huapohen/imagine/docs/business/README.md

# 商业材料索引

所有材料日期2026-09-06。业务、成本与销量是计划/估算；没有已确认融资、订单或生产结果。

- [详细可执行商业计划](business-plan.md)
- [演示结构与口径](outline.md)
- [3分钟/8分钟逐字稿](pitch-scripts.md)
- [投资人60问](investor-qa-60.md)
- [半年生态、8种硬件排序与10个月战略检查](ecosystem-and-exit.md)
- [定价/BOM/财务说明](financial-model.md)
- [SKU输入](financial-inputs-skus.csv)、[公共参数](financial-assumptions.csv)、[情景销量输入](financial-scenarios.csv)
- [单台经济输出](financial-sku-economics.csv)、[月度利润现金输出](financial-monthly.csv)、[情景汇总](financial-summary.csv)
- [重算脚本](calculate_financials.py)：在项目根执行 `python3 docs/business/calculate_financials.py`
- [研究事实与来源](../research/findings.md)
- [工厂RFQ模板](../manufacturing-commercial/rfq-template.md)、[验收与排期](../manufacturing-commercial/acceptance-and-schedule.md)、[BOM CSV](../manufacturing-commercial/bom-cost-estimate.csv)、[采购排期CSV](../manufacturing-commercial/procurement-schedule.csv)

最关键未验证项：299元真实购买选择、鼠标对同一软件的增量价值、D7/D30留存、3家工厂同口径报价、小批成本与良率、USB/供电/人体工学、适用合规、本地agent安装权限、企业聚合重识别风险。官方竞品标价与网页性能主张不能代替这些证据。
