huapohen/imagine/docs/business/business-plan.md

# Imagine 可执行商业计划

2026-09-06｜内部决策版｜创始前验证阶段。成本、销量、留存、收入及估值均无实绩；本文件给出可证伪假设和执行门槛。研究事实见 [findings.md](../research/findings.md)，模型见 [financial-model.md](financial-model.md)。

## 1. 决定先做什么

首款是透明有线鼠标，加一个独立的ESP32-S3灯光/触摸/小屏模块，连接电脑本地agent。鼠标运动、按键和滚轮沿用成熟OEM标准USB HID，AI故障时仍能正常办公。用户看到的是一个会安静等候、遇到有用线索才轻轻提示的伙伴。AI能力在电脑运行，不是ESP32运行大模型；云模型仅接收用户选择并明确授权的必要内容。

首批只制造299元目标售价的单一核心版，其他99/199/499/899元是定价验证卡和后续包装方案，不同时采购五套模具。99元普通透明鼠标不承诺AI硬件能力；199元无屏版在299元留存成立后考虑。499元是核心鼠标、桌面底座和受限服务的套装；899元是核心硬件、企业试点配置和明确额度支持包，不是永久无限AI。

成立条件：用户因为减少一次真实遗漏、顺利完成一次交接而继续启用，而不是仅因为透明外壳第一次很漂亮。若相同软件配普通鼠标的效果接近，就转向软件＋可选配件，停止为差异不足的硬件压库存。

## 2. 客户、场景和付费者

首批选择有自主软件安装权、每天处理多个文档/任务、愿意授权单一任务来源的知识工作者：产品经理、项目协调者、独立开发者和小型服务团队负责人。暂不进入金融交易、医疗、涉密办公或严禁外围设备的企业；暂不让HR成为采购与指标定义者。

| 场景 | 用户提供的最少证据 | 主动介入时机 | 最终动作 | 成功证据 |
|---|---|---|---|---|
| 下班前交接 | 手动任务、截止时间、本人更新 | 出现未交接的新状态且接近截止 | 显示交接草稿，用户批准后复制/导出 | 用户确认完成交接，草稿采纳 |
| 等待同事反馈 | 用户明确标记的任务与授权消息增量 | 相关新回复解决阻塞，安静窗口结束 | 灯提示→解释证据→建议下一步 | 提醒“有帮助”，无重复提醒 |
| 长程任务 | 用户自建目标与选择的资料 | 新证据足以改变下一步 | 更新私人任务卡、请求必要批准 | 中断后可恢复，步骤可解释 |
| 专注陪伴 | 用户手动设定专注时段 | 用户允许的休息/结束节点 | 低亮度灯与简短陪伴文字 | 用户愿保留且不觉得被评判 |

“陪伴”是可关闭的语气和可见状态，不是假装有情感需求，不用内疚、连续签到或“老板正在看”等手段驱动使用。休息提醒仅依据用户选择的时间，不推断疲劳、抑郁或身体健康。

企业买的是本人批准的业务交付物和流程阻塞汇总。个人任务原文、浏览轨迹、私聊、录音、键鼠频次、情绪和生理信息不上企业看板。团队统计至少5名不同授权参与者、固定统计周期、禁止个人钻取；不足5人不显示。还必须抑制极端值、小切片、相邻窗口差分推断，并明确撤回/删除流程。人数阈值不是匿名化证明。

## 3. 产品边界与首期实现

从Active Agent已有思路复用事件、长期任务、证据、安静窗口、决策、审批和outbox等概念，实际代码兼容性、测试与许可需工程检查。首期只承诺手动任务和本地演示事件源；飞书/企微/钉钉是待接入的单独里程碑，不能把模拟数据说成已上线连接器。

本地端保存任务和偏好；默认不常驻抓屏、不读全盘、不录音。选择屏幕/文档内容时先展示具体范围。设备端仅显示简化状态，不缓存任务原文。USB串口/伴随协议和鼠标HID分离；原型双线或小型合规USB hub是可接受取舍，单线化必须通过供电、兼容与EMC评估。触摸事件只触发本地待审批界面，不能作为“不可绕过的硬件安全隔离”宣传。

不做：员工评分、考勤推断、老板隐身模式、环境监听、键盘记录、医疗诊断、生物识别、情绪识别、自动对外发送、远程控制锁屏电脑、首期电池与无线认证、机器人关节或复杂运动。

## 4. 为什么可能需要鼠标

鼠标是办公中高频接触、自然可触达的物体，有机会在屏幕通知之外提供低强度提示和一键查看的仪式感。透明结构让电子状态可见，有传播辨识度。但这些都是假设：高端鼠标用户可能拒绝更换设备，左手用户/手型差异和有线方式会缩小市场；灯光也可能被视为干扰。

实验必须把硬件增量从AI本身剥离：20人随机交叉体验一周软件通知、一周灯/触摸通知，保持相同任务和内容，记录“有帮助”比例、处理延迟、关闭频次和主观打扰。提前定义成功：硬件确认率绝对提升>=15个百分点，打扰评分不劣于软件，且至少8人愿在299元真实价格选择购买或付明确可退订金。小样本只作方向性证据，不宣称统计显著或普适效率提升。

## 5. 市场规模：先用可到达客户算账

本次没有抓取可用于中国AI鼠标细分市场的可靠官方销量，不引用泛AI万亿市场。用自下而上验证替代伪精确TAM：第一阶段可触达名单目标200名个人＋30个小团队；预计试用转化20%和10%都只是销售假设，需要逐周更新。1000台×299元=29.9万元含税商品流水，不能称ARR；100名愿付19元/月的服务用户才对应2.28万元年化订阅毛额，且留存未验证。模型未计入订阅，以免硬件补贴依赖尚不存在的经常性收入。

可服务人群的下一层估计应来自：目标城市/行业公司数×每家公司适配工位数×允许本地agent比例×预算接受度。每一个乘数必须有调查出处。得到20名稳定活跃用户之前不花钱购买宏观市场报告，也不把鼠标存量设备总量当成交付潜力。

## 6. 定价、服务和渠道

| 档位（人民币，目标含税） | 交付边界 | 推出条件 | 核心风险 |
|---|---|---|---|
| 99 | 普通透明有线鼠标，软件基础任务可自行安装；无伴随AI模块承诺 | OEM稳定且有独立需求 | 售后/CAC吃掉毛利，容易成为低价比较入口 |
| 199 | 灯＋触摸，无屏；本地基础任务 | 共板设计降本成立 | 价格带拥挤、视觉反馈不足 |
| 299 | 灯＋触摸＋小屏主推；规则模式离线可用 | 首批唯一制造SKU | 人体工学与可用性决定留存 |
| 499 | 299版＋桌面底座/外观套件＋3个月限定服务额度 | 299复购/推荐成立 | 套件增加库存，服务不能无限承诺 |
| 899 | 核心设备＋单席企业试点配置/培训/3个月限定支持 | 企业授权与安全验收通过 | 实施工时、采购账期侵蚀收益 |
| 1499/3999 | 未来桌面计算底座/团队任务终端的生态概念 | 半年后独立立项 | 未定规格/成本，不收预售，不计收入 |

服务探索价格19元/月个人、39元/席/月团队，仅作访谈卡；供应商模型单价、调用量、上下文与退款未实测前不得上线无限额度。个人可以只用离线规则和自有模型凭据；本项目不接收或记录他人完整API key。企业采购最初采用标准试点协议、验收后明确账期，尽量不要先垫资给长账期大客户。

渠道顺序：创始人展示真实使用案例→自愿用户研究→小批直销→少量企业设计伙伴。前100台不铺经销，不做高额信息流广告。后续每个渠道按退款后贡献和售后时间核算，不仅看GMV。财务模型已保守计入获客成本，不把创始人时间当作永久免费流量。

## 7. 分阶段预算和负责人

| 阶段 | 责任角色 | 预算上限（估算，不是批准支出） | 交付证据 | 下一阶段触发 |
|---|---|---|---|---|
| D1—D7 | 硬件负责人＋本地agent工程师 | 1.5万元 | 5台可重复演示原型、BOM、装配记录 | 核心鼠标不受模块崩溃影响，授权链完整 |
| D8—D30 | 工程＋质量＋创始人 | 累计12万元NRE内分批释放 | 20人试用、10台EVT、小批报价/合规适用性确认 | 无重大隐私/电气缺陷；需求门槛达标 |
| M2—M3 | 产品/供应链 | 不超过下一批100台所需现金＋缓冲 | 50—100台受控试产、售后记录 | 一次合格率>=95%、7天留存目标达标 |
| M4—M6 | 3人核心团队＋按次外包 | 月固定支出5.5万元模型假设 | 分批累计1000台、两个供应源评估 | 退货率<=5%、每台贡献为正、现金覆盖3个月 |

12万元NRE估算分项：结构/电气设计3万、打样与小批治具2.5万、合规评估与预扫2万、软件发布/权限安全评审2万、外观与包装0.5万、预备金2万。不能把这笔钱同时再计入单台BOM；正式模具未包含，只有通过需求门槛后另立项。

## 8. 关键指标与停止条件

北极星指标：每周至少一次被本人确认“有帮助”的主动介入用户数。配套指标：激活率、D7/D30仍启用比例、每用户提醒数/忽略率、每次被采纳动作的模型成本、退款、售后分钟数、单位现金贡献、库存周转和审批拒绝率。数据默认个人可见；产品研究上传最少匿名事件必须自愿授权。

D7原型不工作：缩小到灯/触摸外置模块，不追加定制结构。20人中D7仍启用<40%，两轮内容/打扰改进后仍不提升：停止备货并改为软件研究。连续两个小批退款>10%或制造一次良率<90%：冻结新批采购。发现未经授权外传/外部动作：立即停用相关功能并按流程修复、通知受影响者；不以增长目标压过边界。现金预测未来90天转负：停止非必要NRE和营销，先完成已承诺交付/退款。

## 9. 壁垒与竞争

短期不存在专利式护城河。可累积资产是可信的授权交互、任务证据质量、低打扰策略、设备可靠性数据、可复用工厂工装和愿意推荐的用户群；它们必须用结果证明。开源同类和操作系统助手能复制单个提醒功能，大厂鼠标可快速添加灯/屏，因此更应跑通具体任务与分发，而非讲“硬件入口垄断”。

Microduck启发可见人格和可维护架构；其运动复杂度是本项目应避免的第一期风险。Violoop展示独立算力/屏幕理解/实体审批的另一种路线，我们以电脑已有算力换更低硬件复杂度，代价是依赖本地安装、系统权限与电脑在线。不得复用其商标、网页素材、性能结论或未明确许可的硬件设计。

## 10. 半年生态与第10个月选择

M1只证明任务闭环；M2受控交付；M3用真实使用数据决定是否继续鼠标；M4开放灯/触摸/状态协议和一个参考配件；M5招募少量开发者制作经人工审核的只读插件；M6决定是否立项199无屏版或桌面灯，1499/3999仅概念研究。每件新硬件要有独立需求、完整BOM、售后责任与现金门槛，禁止一次铺八类产品。

第10个月不是承诺退出日，而是董事/创始人战略检查点。若留存和单位贡献成立且现金允许，可以继续经营或讨论融资；若有产业方提出合适条件，可评估分销、技术授权或股权/资产交易；若需求不成立，优先退款、保修安排、员工与供应商义务及数据删除，剩余资产可出售但不能按理想售价估值。没有投资人承诺，没有保证收购方，不把融资计为营业收入。

## 11. 建议融资目标及用途（与演示稿统一）

本方案建议讨论人民币500万元天使融资。500万元是为当前融资叙事提出的建议金额，并非用户原文指定金额，也不是已获投资承诺、已到账资金或已确定估值。以下用途为讨论建议，不构成支出授权；先依原型、用户需求、合规、留存和交付证据分段释放预算。

| 建议用途 | 金额（万元） | 占比 | 释放前提 |
|---|---:|---:|---|
| 产品与Agent研发 | 200 | 40% | 岗位职责落实、最小任务闭环与授权验收通过后分段推进 |
| 硬件试制与合规 | 100 | 20% | DFM、实际BOM报价与目标市场合规路径明确 |
| 用户验证与设计伙伴 | 60 | 12% | 自愿研究、真实价格选择与清晰试点范围，按证据扩大 |
| 量产准备与周转 | 80 | 16% | 需求/留存、质量及90天现金义务门槛通过后分批采购 |
| 预备金 | 60 | 12% | 仅针对经评审的供料、质量、合规或现金偏差动用 |
| **合计** | **500** | **100%** | **逐项批准，不一次性支出** |

既有财务CSV是“60万元假设起始现金”的精简验证情景：12万元NRE、5.5万元月固定支出及提前备货规则均属于该独立模型。不得将500万元融资额直接替换进去后沿用原团队、研发和市场投入来宣称长期跑道。500万元建议用途尚未建立同口径分月招聘、研发、采购、回款及现金模型，因此暂不报告其跑道、收入、估值或投资回报。融资到账前不以预期融资承担采购与人员承诺；下一步应在岗位、报价、试点范围和实际融资条件明确后另建扩张预算模型。
