huapohen/imagine/docs/business/financial-model.md

# 定价、BOM和财务模型使用说明

币种：人民币。口径：全部成本和销量是估算，非供应商报价、销售实绩或融资到账。计算脚本实际运行并生成CSV，模型真实可改可算，不意味着假设是真实成交数据。美元竞品价格不参与换算定价。

## 文件与重算

输入：[SKU参数](financial-inputs-skus.csv)、[公共假设](financial-assumptions.csv)、[月度情景销量](financial-scenarios.csv)。输出：[单台经济](financial-sku-economics.csv)、[月度利润及现金](financial-monthly.csv)、[情景汇总](financial-summary.csv)。脚本：[calculate_financials.py](calculate_financials.py)。

在项目根目录运行：`python3 docs/business/calculate_financials.py`。仅Python标准库、无网络/凭据，CSV使用UTF-8 BOM方便表格软件打开。修改输入后重算；不要手改生成输出。现金勾稽自动检查：期末现金=起始现金＋累计损益－应收款－期末库存。模型以未四舍五入值计算、输出保留两位，汇总可能有分位差异。

## 主推299版BOM：1000台规模设计目标

| 项 | 估算元/台 | 待验证 |
|---|---:|---|
| 成熟有线鼠标OEM底座（不含定制上壳） | 19 | 传感器/微动、合法USB身份、供货稳定性 |
| 透明壳/底结构件 | 11 | 材料、是否可用公模；不含新开模费 |
| ESP32-S3模块 | 16 | 内存版本、授权渠道、可获得性 |
| 小屏及排线 | 15 | 尺寸分辨率、坏点/供货、非定制屏 |
| 灯及导光、触摸件 | 5 | 电极一致性、误触、透明反光 |
| PCB/电源/连接器/线材或hub分摊 | 14 | 单线化可能大幅加价，先用双线 |
| 装配与100%功能测试 | 12 | 工时与产测治具，不含NRE |
| 包装/标签/说明书 | 6 | 实际运输保护 |
| 制造损耗/返工预留 | 10 | 不再重复加同口径损耗 |
| **完整制造成本设计目标** | **108** | 无书面报价，不是采购承诺 |

**成本版本说明（最终一致性复核补充）**：早期简化原型曾估5台每台260—480元（不含工程工时/NRE）、50—100台145—190元、规模目标90—130元。这些是结构/工艺未冻结时的历史假设，已被当前DevKit工程估价替代，不再作为现行EVT采购或小批预算依据。当前口径见[工程与制造交接](../hardware/engineering-and-manufacturing.md)：5台透明打印/CNC及手工抛光EVT，材料/电子/外协450—1000元/台，装配240—480元/台，整台690—1480元未税；按80%有效良率约863—1850元/合格台。100台打印/复模小批按90%良率约283—467元/合格台；以上仍是工程估算，未获供应商报价。

**108元/台继续仅作为未来1000台、模块/公模路线的商业模型假设**，不等于当前官方开发板与定制透明壳方案的采购价；**170元只用于成本敏感性算例，不代表当前EVT或100台小批报价**。模型尚未按最新DevKit工艺逐月重算，前期现金支出可能显著高于模型；不能据现有现金表批准采购。当前脚本修改SKU成本会作用于全部月份，精细预算需增加分月/分工艺成本。若屏、hub和壳体空间冲突，先评估外置模块，不把目标成本写成已达成。

99/199/499/899档制造完整成本估算分别32/72/158/255元。499/899包含套装物料/包装的额外成本，实施支持另计到单台支持费；所有模具/NRE在月0独立列示，避免重复摊销。1499/3999不进财务表，因为尚无可报价规格。

## 单台经济（已运行模型）

| 售价 | 完整制造成本 | 扣除全部列示变动费用后贡献 | 贡献/含税流水 | 仅该SKU覆盖5.5万元月固定支出的销量 |
|---:|---:|---:|---:|---:|
| 99 | 32 | 13.04 | 13.17% | 4218 |
| 199 | 72 | 33.74 | 16.95% | 1631 |
| 299 | 108 | 66.51 | 22.24% | 827 |
| 499 | 158 | 137.50 | 27.56% | 400 |
| 899 | 255 | 259.55 | 28.87% | 212 |

“贡献”不是毛利，也不是净利润。299元逐项：销项税现金预留34.40、渠道8.97、退款11.96、制造108、履约12、质保2.16、支持8、获客45、退货逆向物流2，剩66.51。退款按销售额4%全额预留且假设退货不能回收价值，质保按制造成本2%；两者分属退货退款与未退货保修，实际发生时需避免重复归类。税按13%含税价销项预留、不抵进项，退款也不减销项预留，偏保守；实际税率、纳税身份和抵扣必须由会计按真实业务替换。

## 10个月情景（非预测承诺）

假设起始现金60万元（不是已获投资）；月0投入12万元NRE；固定开支5.5万元/月；上行情景M4起固定开支6.6万元。M1—M3只卖299主推版；M4以后才假设其他概念SKU获准上线，不能据表提前备货。下行/基准/上行为基准销量的0.35/1/1.7倍。企业899全额延后1个月回款，其他当月；采购假设提前1个月全额付现＋10%缓冲库存。M10仍按M11预计增长15%备货，不用期末清仓制造好看现金。

| 情景 | 10个月台数 | 含税流水 | 累计贡献 | 含NRE累计损益 | 期末现金 | 最低现金 |
|---|---:|---:|---:|---:|---:|---:|
| 下行 | 1613 | 553287 | 132936 | -537064 | -24820 | -24820 |
| 基准 | 4610 | 1580890 | 379789 | -290211 | 60494 | 45908 |
| 上行 | 7837 | 2687263 | 645556 | -101444 | 75107 | 23002 |

基准仍亏损，上行销售更多却经历更低现金谷底，因为提前采购和企业回款。下行第10个月现金转负，模型显示缺口，不假定自动融资填平。基准期末库存190860元、应收58435元，并非现金。所有情景都未形成3个月固定费用缓冲（至少16.5万元），应更早缩减采购/开支或明确增加已确认资金。禁止靠“计划融资”继续透支。模型不含利息、所得税、订阅、汇兑、资产残值、潜在强制认证新增费和模具费；有任何此类承诺须纳入后再决定。

## 敏感性与行动

- 299制造成本每增加10元，贡献下降约10.20元（质保联动）；从108升至170元，贡献仅约3.27元。首批不可能自然有规模毛利，须作为限额验证投入。
- 获客成本45升至75元，299贡献减为36.51元，覆盖月固定开支约1507台；渠道扩张前先验证退款后获客成本。
- 退款率4%升至10%，299贡献少17.94元，还可能增加逆向运费/不可销售库存，实际更差。
- 三个月前110台若实际制造170而非108，直接差额6820元，加质保约136元；演示原型与NRE另算，不可从账上消失。
- 固定支出每月增加1万元，10个月少10万元现金；供应商要求更早/更多预付款同样恶化资金峰值。
- 提价到399不是免费改善：要重新验证转化和退货，不能保持销量假设不变只改售价。

下一步优先取得3家同口径报价、实测20人使用与真实价格选择、记录每个售后工单分钟数、测量10种任务的模型成本。完成前，现金模型仅用于决定验证预算，不用于保证投资收益或估值。
