huapohen/imagine/docs/business/ecosystem-and-exit.md

# 半年生态、八种硬件及10个月战略情景

2026-09-06。此文件是决策路线，不是已开发产品、市场订单或融资退出承诺。首发目标售价299元；1499/3999只是远期生态概念。

## 半年只解锁一层复杂度

| 月份 | 核心交付 | 可进入下一步的证据 | 暂停条件 |
|---|---|---|---|
| M1 | 5台原型、10台EVT候选、20人授权试用、完整BOM/隐私/质量记录 | 7天仍启用目标>=60%；有用提醒目标>=50%；鼠标基本功能独立 | 重大安全/隐私缺陷；有用性不足不下批量单 |
| M2 | 50—100台受控试产；量化售后分钟和退款原因 | 首次良率>=95%，出货100%功能验收；安装成功率目标>=90% | 关键合规未完成；安装失败未解决 |
| M3 | 决定硬件增量是否成立；对软件/灯触摸做交叉比较 | 硬件确认率增量目标>=15个百分点且不增加打扰；实际付费选择 | 两轮改进后仍不被使用则转软件/配件 |
| M4 | 达标后分批到累计约1000台；冻结状态协议v1和一款参考配件 | 每台贡献为正；退款<=5%；现金覆盖至少未来90天必要义务 | 不为销量提前采购超90天预测；不同时开多模具 |
| M5 | 只读插件SDK、权限清单与人工审核；3个设计伙伴工作流 | 插件可撤回授权、可审计、不会扩大数据范围 | 未授权外传/外部执行直接停相关插件 |
| M6 | 根据付费与留存决定下一个硬件立项；供应链第二来源评估 | 新SKU至少10位真实价格意向/选择、BOM报价、独立现金表 | 生态叙事不能掩盖主SKU低留存或亏损 |

时间目标与财务情景分开：M4累计1000台是有条件的工程/运营能力目标，财务基准M4累计仅260台；不能在演示中混为已承诺同一销量。若走模型基准，1000台累计约在M7达到。订阅、插件市场佣金、数据收入都没有进入模型。

## 八种其他硬件：按资源和验证难度排序

评分1—5分，越高越好；总分=共享软件/供应链30%＋低制造复杂度25%＋需求可验证性25%＋低隐私风险20%。这是团队决策假设，不是消费者调研结果。目标售价均人民币概念价，未报价。

| 排名 | 硬件与目标价 | 共用/简单/需求/隐私 | 加权分 | 用户任务与差异 | 首个实验及停止条件 |
|---|---|---|---:|---|---|
| 1 | USB桌面状态灯，149—299 | 5/5/4/5 | 4.75 | 不换鼠标也能安静提示，直接覆盖高端鼠标用户 | 10人借测外置灯，同软件比较；价值相当则优先做它替代定制鼠标 |
| 2 | 触摸确认旋钮，199—399 | 5/4/4/5 | 4.50 | 查看待办、稍后、调提醒强度；无需语音 | 打印壳＋现成编码器/按键；误触>5%先改交互，不做“安全硬件”夸大 |
| 3 | USB任务宏键小键盘，199—499 | 4/4/4/5 | 4.20 | 3—6键切换任务/生成草稿；适合不愿换鼠标者 | 先现成宏键盘；任务完成快捷性无增量则不自研 |
| 4 | 桌面电子纸任务牌，299—699 | 4/3/4/5 | 3.95 | 常驻显示本人选择的下一步，低频刷新且无持续动画 | 用现成开发板，测文字可读性/刷新和肩窥；不默认显示敏感原文 |
| 5 | USB脚踏确认/稍后开关，149—299 | 4/4/2/5 | 3.70 | 双手忙时请求查看或推迟，适用于特定创作岗位 | 5名真实岗位试用；误触或姿势负担不可接受即停止；无健康改善宣传 |
| 6 | 无摄像头桌面表情伙伴，499—899 | 4/2/3/5 | 3.45 | 小屏/灯表达任务状态，面向陪伴偏好用户 | 先静态屏幕无电机；一周后主要互动只剩玩表情则不进办公主线 |
| 7 | 独立桌面计算底座，1499概念 | 3/1/3/3 | 2.50 | 用户电脑之外运行有限本地工作流，较少依赖主机在线 | 先现有小主机验证；功耗/热/更新/合规/成本未闭环前不做定制硬件 |
| 8 | 团队公共任务终端，3999概念 | 3/1/2/2 | 2.05 | 公共空间只展示授权业务结果与满足门槛的汇总 | 先用现有平板/浏览器；若被要求显示个人排行或监控数据则拒绝该场景 |

这些排序不是一次性产品矩阵承诺。前六个月最多一个新增硬件试验，优先桌面灯或旋钮；高价计算底座要独立人员预算和用户需求，不以复用agent就忽略计算硬件、散热和系统维护成本。任何麦克风、摄像头或生理数据功能均不在以上规格中。

## 开放生态的最小合同

设备只理解有限状态、颜色/亮度、脱敏短标签和触摸事件；不直接拥有企业数据源凭据。插件声明读取的具体数据、用途、保留时间和可触发动作；默认只读，外部写入必须审批。签名版本、兼容矩阵、撤销和升级回滚先于插件市场收费。第三方配件不能借品牌暗示医疗、员工监控或安全芯片认证。SDK许可、商标使用和第三方责任需单独明确，不自动照搬Microduck仓库的软件许可。

## 10个月检查点：四种可执行情景

| 情景 | 所需证据/触发条件 | 接下来30天动作 | 财务与承诺边界 |
|---|---|---|---|
| A 继续经营 | 留存/有用性与单位贡献成立，现金覆盖90天义务 | 缩到主SKU、争取分批采购，更新12个月现金；创始人决定节奏 | 不是已经盈利；基准模型累计损失仍约29万元 |
| B 讨论外部融资 | 有可验证使用/订单/退款/账目，明确新增资金购买哪些里程碑 | 准备脱敏数据室、规格/BOM/知识产权/合同与现金证据；由授权负责人沟通 | 无保证投资者、估值或到账日；未签到账资金不用于采购承诺 |
| C 产业合作或交易 | 出现实际相对方和书面可评估意向，资产/许可归属明确 | 比较分销、联合开发、许可、资产或股权交易；审慎尽调用户与合同义务 | 不预设收购方、不在收入中计退出金额，不保证10个月成交 |
| D 有序停止 | 两轮改进后无需求、现金覆盖不足或重大不可修复问题 | 立即停止新预售/非必要采购；列清已付款客户/员工/供应商/税费/保修义务；安排退款与数据导出删除 | 资产按实际可实现价处置，股东可能无法收回全部本金 |

## 退出价值只按可核实资产评估

可以进入尽调：合法可转让的软件/固件、设计文件、品牌权利、工装所有权、库存及状态、合法合同和脱敏聚合运营证据。不能当作出售资产：个人私聊、任务原文、生理/情绪画像或隐蔽采集数据。开源依赖必须有清单和许可兼容核查；网页能下载不代表可复制商标或整机硬件设计。

建立可编辑的现金回收表：实际可出售库存数量×第三方真实报价－退货/返修/运输－优先债务－保修准备－交易费用。原价、账面成本和理想销售价都不是清算价。不要用一个假设并购倍数倒推投资回报，更不要承诺回购本金或固定收益。
