huapohen/imagine/docs/business/outline.md

# Imagine 商业叙事与演示大纲

版本：2026-09-06。所有销售、成本、用户指标和时间表均为计划/估算，未发生融资、订单或量产。

## 一句话

Imagine 把每天握在手里的透明鼠标变成主动式办公伙伴：只在有新证据、能帮上忙时，用低打扰的灯光和触摸，把待办、进展与下一步带到你面前。

## 12页投资人演示结构

1. 封面：透明鼠标＋主动式办公伙伴；员工先受益，企业只看被授权的业务结果。
2. 问题：跨应用任务遗漏、提醒过载、聊天式AI需反复主动召唤；是假设，待访谈和测试。
3. 场景：授权一项任务→等待新证据→灯光轻提示→点击看理由→选择确认/稍后/忽略→个人回顾。
4. 产品：标准鼠标HID与ESP32-S3伴随模块分离，电脑本地agent；无麦克风/摄像头/生理传感。
5. 核心价值：任务证据、安静窗口、主动介入、可恢复任务与审批；不是把聊天框塞进鼠标。
6. 双边信任：员工控制数据，企业仅授权结果与>=5人汇总；禁止个人绩效/情绪推断。
7. 市场进入：20名自愿知识工作者→3个10—30人设计伙伴团队；先证明持续使用再批量备货。
8. SKU：99普通透明鼠标引流概念、199灯触摸、299主推带屏、499套装、899企业试点包；1499/3999仅生态远期概念，不接预售。
9. 经济：主推299元，1000台假设下制造完整成本108元；每台现金贡献估计约67元，含渠道/税/履约/质保/支持/CAC后的口径，须以模型实际输出为准。
10. 交付：7天目标是5台演示原型；30天只在EVT/小批安全合规/用户及采购门槛均满足后，争取50—100台受控试产交付，绝非注塑量产承诺。
11. 半年：验证有用→100台→1000台分批→开放配件协议；生态基于留存而非同时做多种硬件。
12. 资金与选择：以里程碑释放预算；10个月评估持续经营/战略合作/资产交易/有序停止，不承诺下一轮融资或退出。

## 对标必须准确

Microduck是公开的小型双足机器人项目；官方产品页标预售399美元（税运另计），未验证众筹成绩/订单/交付。Violoop官网是预发布预约，展示399美元起、预约优惠后369美元起；未证实销量。引用见 [研究事实](../research/findings.md)。

## 演示口径

允许：“目标”“设计”“原型”“在授权前提下”。禁止：“已融资”“爆卖”“提升30%效率”“已获大客户”“100%本地AI”“7天量产”“30天必出货”。若屏幕为模拟数据，现场清楚标示；真实硬件未完成时播放明确标注的交互模拟。
