huapohen/imagine/pitch/deliverables/final-20260906/deck-content.md

# 灵伴 LINGBAN 18页演示正文

本文件直接取对应PPTX导出的PDF文字，与展示页一致。演讲扩展与来源见speaker-notes.md。

## 第1页

01
创始前验证阶段   2026.09   品牌与商标待检索
灵伴
LINGBAN
手边的主动式办公伙伴
晶鼠 Crystal Mouse
原创产品概念示意

## 第2页

工作中的下一步，常常等不到人来追问
02
需求假设，尚无访谈或效率实绩
17:40
回复已经到了
交接仍然停在原地
任务跨应用
截止时间、文档和等待状态
缺少同一个任务上下文。
提醒缺少理由
用户需要知道发生了什么变化，
以及现在是否值得处理。

## 第3页

一次主动协作的完整故事
03
合成场景与拟实现交互，现场演示需清楚标识
01 授权任务 仅选择这次交接的资料与截止时间
02 等待新证据 相关回复解除阻塞，安静窗口结束
03 轻提示与解释 灯光提示，触摸后展示依据及交接草稿
04 本人决定 确认、稍后或忽略，审批后复制或导出
05 明确分享结果 本人逐项批准业务交付物，个人回顾私有

## 第4页

鼠标的价值需要独立证明
04
20 人小样本仅作方向性验证，不宣称统计显著或普适效率提升
手边可见、触手可及
低亮度灯表达状态，触摸后再展开信息。
外观吸引首次尝试，任务价值决定留存。
20 人
随机交叉体验
≥15 个百分点
硬件确认率绝对提升目标
≥8 人
299 元购买意愿
若增量不成立，停止为硬件差异压库存。

## 第5页

透明晶鼠，保留日常鼠标的可靠性
05
原创概念示意，尚无实物打样、板级验证、量产或认证完成证据
299 元首发核心版
透明外壳与原创静态城堡
RGB 灯、触摸与小屏状态显示
成熟 HID 底座＋独立交互模块
AI 运行于电脑， HID 保持独立。
小屏仅显示简化状态，不存任务原文。
物理静音与状态指示为设计要求

## 第6页

Agent 架构与协议实现子集
06
本地合成演示子集，非官方互通或认证。 LB1 待实机验证、未验证硬件连通
设备交互
HID 底座独立设计
灯／触摸／小屏可模拟
LB1 待实机验证
电脑本地规则 Agent
任务与证据、专注静默
人工审批只写本地 outbox
无外部发送，模型适配另验收
本地授权服务
员工／企业角色鉴权
明确提交的业务聚合
企业连接器待接入
MCP 2025-06-18
stdio JSON-RPC ：握手、 ping
tools/list 、 tools/call （ 4 个工具）
A2A 0.3.0
Agent Card 、 message/send 、 tasks/get
同步文本摘要与持久化任务
测试记录：真实 stdio ／ HTTP 鉴权、握手与错误、任务生命周期／归属／持久化。
MCP 未覆盖： resources 、 prompts 、 HTTP 、 OAuth 等，完整清单见讲稿。
A2A 未覆盖：流式、取消、推送、异步、多轮上下文等，未做官方 SDK 互通。

## 第7页

员工掌握分享范围，企业获得业务结果
07
≥5 人是产品阈值，不能替代合法处理依据、访问控制与匿名化评估
个人可见
任务原文、资料与私人回顾
本人选择范围，可撤回和删除。
企业可见
逐项批准分享的业务结果
≥5 名授权参与者的固定周期聚合
禁止个人钻取与敏感切片
无秘密录音摄像、键盘记录或情绪／生理员工评分。
无自动雇佣决策，单次雇佣同意不等于全部共享。

## 第8页

首发只制造 299 元核心版
08
99/199/499/899 为定价验证及后续方案。 1499/3999 仅生态探索，不收预售
目标含税价 交付边界 推出条件
99 元 普通透明有线鼠标，无伴随 AI 模块 有独立需求、 OEM 稳定
199 元 灯＋触摸，无屏 共板降本与 299 元留存成立
299 元 灯＋触摸＋小屏，离线规则可用 首发唯一制造 SKU
499 元 核心版＋底座／套件＋ 3 个月限定服务 复购与推荐成立
899 元 核心设备＋单席试点配置与限定支持 企业授权和安全验收通过

## 第9页

Microduck 与 Violoop 提供不同路线的启发
09
研究快照日期 2026-09-06 。官网主张不等于独立测试， GitHub stars 不等于销量
对象 可确认的公开事实 对灵伴的启发与边界
Microduck
25cm 双足机器人， 15 个舵机
预售价 399 美元，税运另计
可见人格、可维护架构
成交／订单／众筹成绩未证实
Violoop
官网预发布预约
399 美元起，优惠后 369 美元起
独立算力与实体确认路线
交付／销量／性能未独立验证
灵伴方案
电脑 Agent ＋成熟 HID 底座
ESP32-S3 仅负责交互
降低首期硬件复杂度
依赖本地安装与电脑在线

## 第10页

市场测算从可触达名单开始
10
名单规模与转化率均为计划假设，尚无客户、订单或收入实绩
200 名个人
×20% 试用转化假设＝ 40 人
30 个小团队
×10% 试用转化假设＝ 3 个团队
先完成 20 名自愿用户研究
再争取 3 个 10–30 人的设计伙伴团队。
下一层规模按适配工位、安装权限与预算接受度逐项调查。

## 第11页

收入先来自硬件，服务先验证付费意愿
11
全部为假设。财务模型暂不计订阅收入，融资不计营业收入
29.9 万元
1000 台 × 299 元
含税商品流水示例
个人 19 元／月
服务访谈价，先实测调用成本与留存。
100 名付费者对应 2.28 万元年化订阅毛额。
团队 39 元／席／月
服务访谈价，另行约定授权、
模型额度、实施与支持边界。
直销试用案例积累后，再扩大渠道。

## 第12页

299 元版的单位现金贡献估算
12
1000 台规模估算， 108 元含 10 元损耗预留，良率未验证。税款按 13% 销项预留、不抵进项。
66.51 元
每台现金贡献估计
22.24%  贡献率
约 827 台／月
覆盖 5.5 万元月固定支出
小批成本 170 元时，贡献仅约 3.27 元。
售价与扣项 元／台
含税目标售价 299.00
制造完整成本 108.00
税款及退款预留 46.36
渠道、履约、质保、支持等 33.13
获客成本 45.00
剩余现金贡献 66.51

## 第13页

7 天样机与 30 天试销的交付门槛
13
计划目标，尚无完成证据。 30 天试销受硬件、安全合规、用户与采购验收门槛约束
D1–D7
5 台演示原型
HID 独立可靠，授权链完整
预算上限估算 1.5 万元
D8–D30
20 人试用＋ 10 台 EVT
安全合规评估与采购确认
累计 12 万元 NRE 内分批释放
达标后
50–100 台受控交付
一次合格率目标≥ 95%
未达门槛顺延至 M2–M3
试用门槛： D7 仍启用≥ 60% ，每周“有帮助”提醒用户≥ 50% 。

## 第14页

半年生态，按留存与交付证据推进
14
半年路线为目标，财务基准 M1–M6 累计 910 台。 1499/3999 元生态概念不计收入
M1
任务闭环
授权、证据、审批
M2
受控交付
质量与售后记录
M3
留存决策
继续鼠标或转软件
M4
开放交互协议
一个参考配件
M5
少量开发者
审核后的只读插件
M6
下一款立项
无屏版或桌面灯

## 第15页

待招团队与外部专业能力
15
岗位与预算均为计划，未提供可核验的成员姓名、履历或招聘完成证据
计划岗位 优先交付责任
产品／商业负责人 用户研究、定价验证、设计伙伴与现金纪律
本地 Agent 工程师 任务证据、权限审批、可恢复执行与发布
硬件／供应链负责人 HID 独立链路、结构装配、质量与交付
按次外部专业能力 工业设计、测试、隐私法律与合规认证
精简验证模型：月固定支出 5.5 万元，其中人员 4.2 万元。

## 第16页

建议融资 500 万元，按证据分段投入
16
500 万元及用途为融资建议，未获承诺。 60 万元精简验证模型为独立情景，不能推算 500 万元跑道
500 万元
建议融资目标
按原型、需求、合规和
交付证据释放预算
60 万元精简模型（ 10 个月）
期末现金 6.05 万元，累计亏损 29.02 万元
建议用途 万元 占比
产品与 Agent 研发 200 40%
硬件试制与合规 100 20%
用户验证与设计伙伴 60 12%
量产准备与周转 80 16%
预备金 60 12%
合计 500 100%

## 第17页

风险对应明确的停止条件
17
阈值是管理规则，尚无达到或触发的实际测试记录
风险 停止或纠偏条件
用户不持续启用 D7 仍启用 <40% ，两轮改进无效，停止备货
质量与售后失控 连续两批退款 >10% 或制造一次良率 <90% ，冻结新批
授权与信任受损 发现未经授权外传／动作，立即停用并修复通知
现金与库存压力 未来 90 天现金预测转负，暂停非必要 NRE 和营销
可累积资产：可信授权、任务证据质量、低打扰策略与可靠交付。

## 第18页

18
10 个月 1 亿美元退出仅为目标情景，无估值依据或收购承诺，不进入财务预测
让下一步，更容易发生
员工先受益
团队获得本人批准的业务结果
建议融资 500 万元，验证 299 元晶鼠的持续任务价值。
第 10 个月战略检查点：持续经营、合作或有序停止。
