huapohen/imagine/docs/research/findings.md

# 研究事实与决策底稿

抓取日期：2026-09-06（Asia/Shanghai；UTC 原始时间见 sources.json）。用途：产品取舍、融资材料事实核验。网页宣称不等于独立测试，不得转换为已实现能力或销售证据。

## 可确认的公开信息

| 对象 | 确实抓取的官方来源 | 可证实内容 | 不可由本次证实 |
|---|---|---|---|
| Microduck | [官方仓库](https://github.com/pollen-robotics/microduck)、[README](https://raw.githubusercontent.com/pollen-robotics/microduck/main/README.md)、[GitHub API](https://api.github.com/repos/pollen-robotics/microduck)、[官方产品页](https://pollen-robotics.com/microduck) | 官方称约25cm、800g；RK3566、15个舵机、50Hz控制环；强化学习策略；Rust守护进程；签名更新和回滚。GitHub API快照7374 stars/858 forks，许可证元数据Apache-2.0。产品页写2026-08-27开启预售、入门预售价399美元（税运另计），配件包39/119美元 | 实机性能、整机BOM、实际成交价、订单数、众筹金额、生产良率、全部硬件许可范围；stars绝非销量 |
| Violoop | [官网](https://violoop.ai) | 官网展示HDMI输入＋USB-HID、本地优先、实体确认键；标注RK3576＋26TOPS、8B本地模型、STM32H563；预发布预约页写10美元可退预约、早鸟399美元起及额外30美元优惠后的369美元起 | 已交付数量、众筹爆卖、真实利润、性能独立复现；页面写53tok/s、2.7倍M4、90%token节约均仅厂商主张 |
| 个人信息保护法 | [中国人大网全文](http://www.npc.gov.cn/npc/c2/c30834/202108/t20210820_313088.html) | 第5—7条合法正当必要/最小范围/透明；第13条处理依据；第15条撤回同意；第24条自动化决策；第28—29条敏感个人信息及单独同意 | 本项目是否满足所有法定义务，需要按实际业务和部署地区法律审查；>=5人聚合不是法律免责或可靠匿名保证 |

Violoop 页面显示 Kickstarter 预发布，并写 SEP 15 09:00 PDT；页面倒计时与抓取日可能不一致。只能写“官网预发布预约中”，不能写“众筹已成功”。价格是美元网页宣称，非本项目定价基准。Microduck 把人格化表达和开源运动栈结合，提供传播形式启发，但15舵机机器人不适合99—899元鼠标的首期成本/交付约束。Violoop有独立计算和屏幕采集硬件，我们用现有电脑本地agent，不能宣称相同性能或权限模型。

Espressif [ESP32-S3官方USB设备文档](https://docs.espressif.com/projects/esp-usb/en/latest/esp32s3/usb_device.html)已完整抓取：支持USB Full-Speed、CDC/HID等类与复合设备；USB-OTG和USB-Serial-JTAG共享一个PHY，不能未经设计就假设两者同时独立工作。这只证明平台能力，不证明本项目接线/固件/供电已通过实机测试。首次代理下载超时的残缺副本不作引用，之后直连完整获取322082字节。Microduck产品页代理握手超时后直连2.40秒成功。

## 本项目必须守住的边界

首期：标准USB有线鼠标OEM底座保持HID链路独立；ESP32-S3仅处理灯、触摸和小屏；AI运行于电脑本地agent，选定内容外发模型前取得授权。无摄像头、无麦克风、无生理传感、无常驻录屏；原型触摸只是请求动作，不宣称具备独立安全芯片。外部发送/写入先展示对象、内容、范围再批准。企业只看到员工逐项授权分享的业务结果和符合最小人群阈值的汇总，绝不提供个人活跃度/情绪/健康/生产率评分。

## 来源质量与复核

抓取清单及SHA-256见 [sources.json](sources.json)，快照用于内部事实核验，不将第三方整页文案或设计用于本项目产品。直连GitHub约1.03秒、Violoop约1.81秒；动态读取scutil系统代理后分别约4.85秒/0.97秒。raw.githubusercontent.com直连重置后改已验证系统代理成功。政府旧链接404、Espressif主页403均如实留存，不作为事实来源。仅短文本，无依赖/SDK/大文件下载，无合适完整国内镜像，因此未做镜像替代。未请求、记录或使用任何API凭据。

## 待验证优先级

1. 真实员工是否愿意每天开启本地agent及授权至少一个任务源；访谈不采集私密聊天。
2. 20名自愿测试用户中，7天仍启用者>=60%、每周至少一次“有帮助”提醒者>=50%；这是拟定门槛，不是现有结果。
3. 对同一个本地软件能力，鼠标灯/触摸是否让提醒确认率提升>=15个百分点，且主观打扰不增加。
4. 3家OEM含税书面报价、USB双链路供电/EMC、透明材料手汗磨损、100台批次可追溯性。
5. 企业>=5人聚合仍须抑制小分组、敏感切片与差分推断，不以人数阈值替代访问控制。
