huapohen/imagine/hardware/pcb/NOT-FOR-FAB/plots/pcb-routed.png

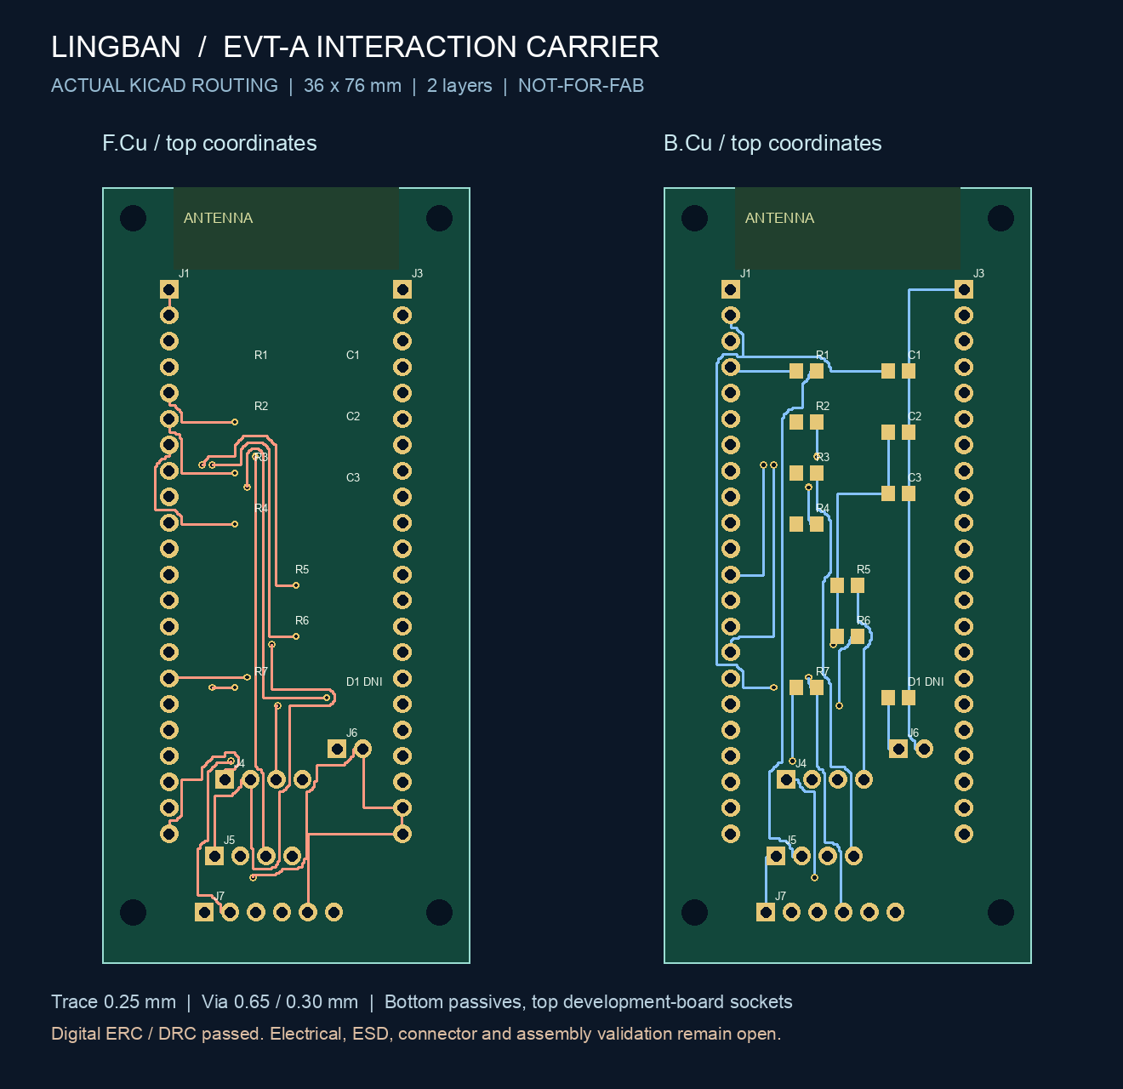
hardware/pcb/NOT-FOR-FAB/plots/pcb-routed.png
