huapohen/imagine/hardware/renders/exploded_raw.png

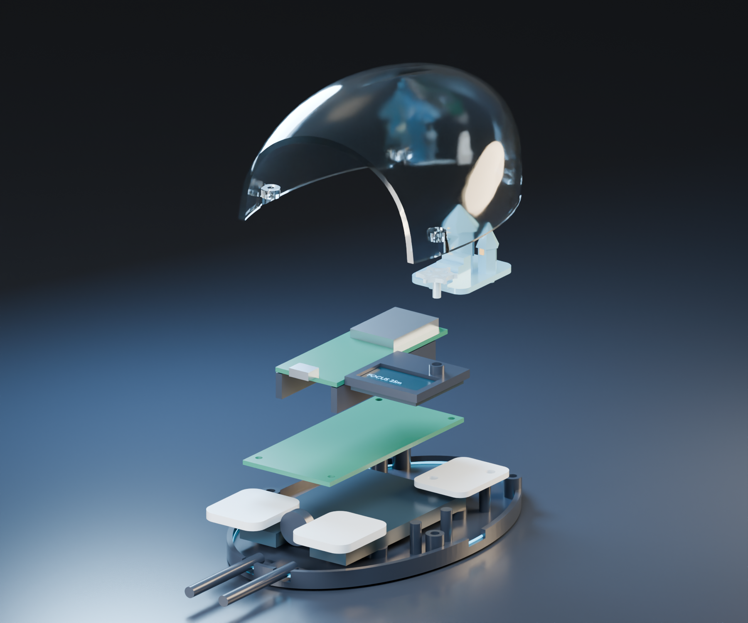
hardware/renders/exploded_raw.png
