huapohen/imagine/hardware/renders/frames-labeled/0001.png

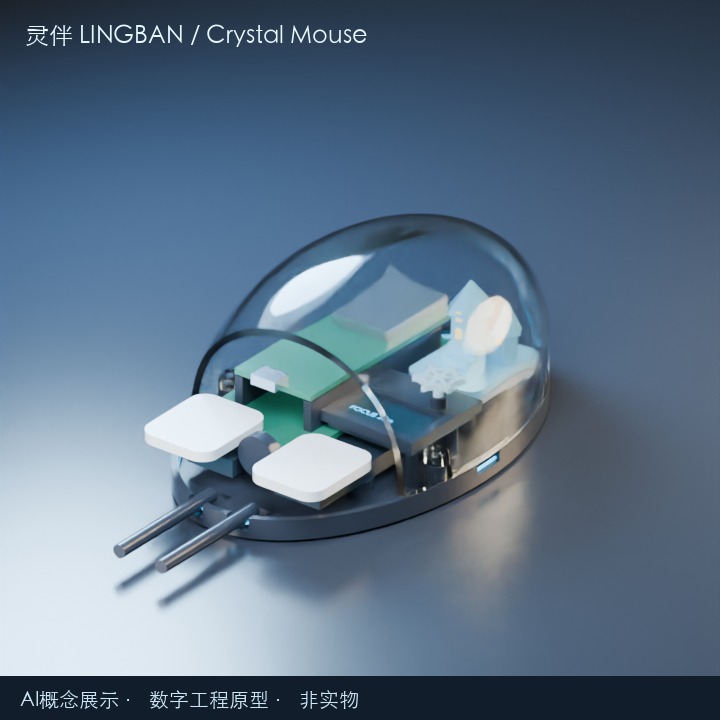
hardware/renders/frames-labeled/0001.png
