huapohen/imagine/hardware/renders/frames-labeled/0002.png

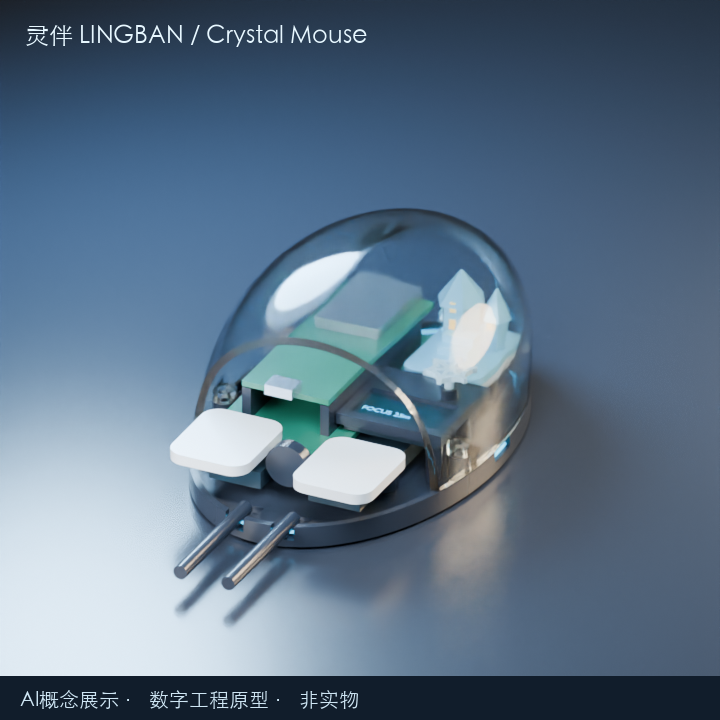
hardware/renders/frames-labeled/0002.png
