huapohen/imagine/hardware/renders/frames-labeled/0003.png

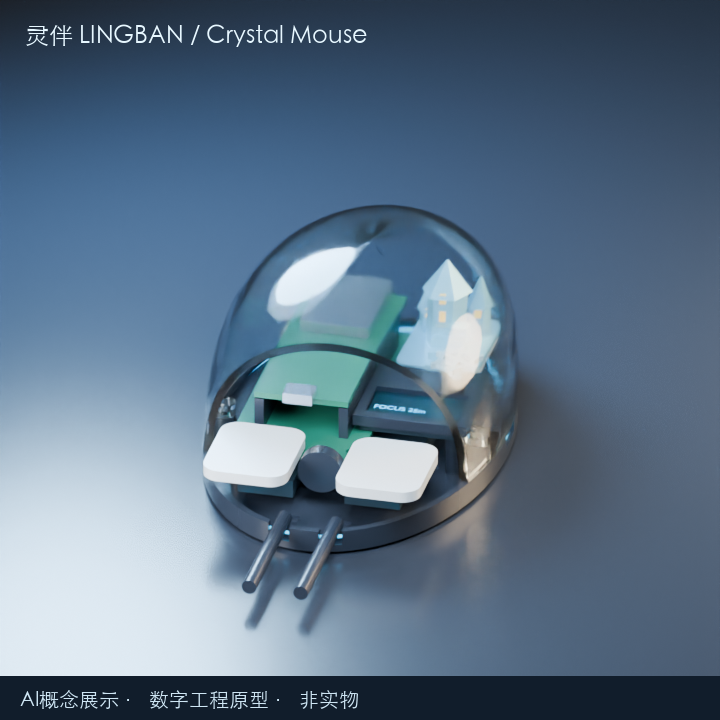
hardware/renders/frames-labeled/0003.png
