huapohen/imagine/hardware/renders/frames-labeled/0005.png

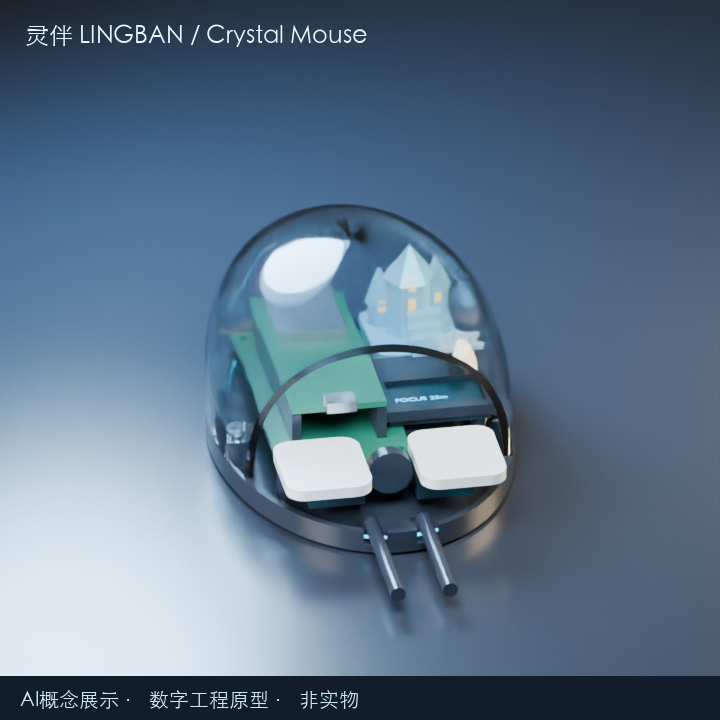
hardware/renders/frames-labeled/0005.png
