huapohen/imagine/hardware/renders/frames-labeled/0006.png

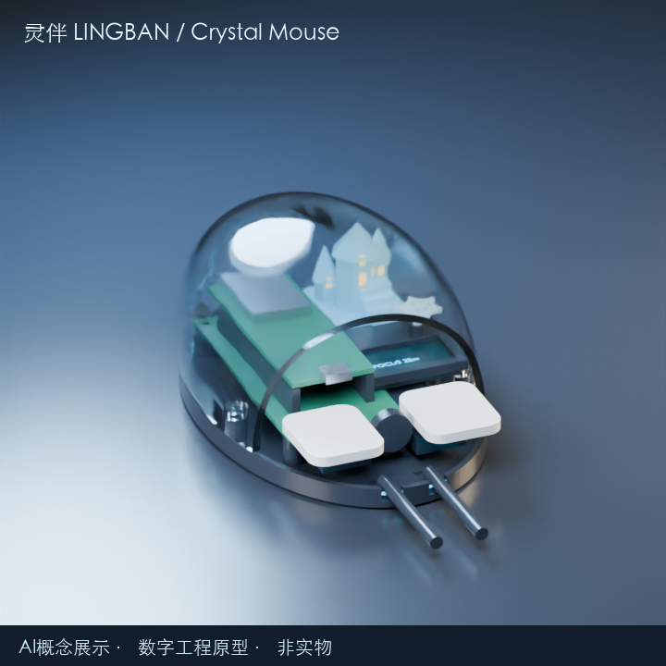
hardware/renders/frames-labeled/0006.png
