huapohen/imagine/hardware/renders/frames-labeled/0007.png

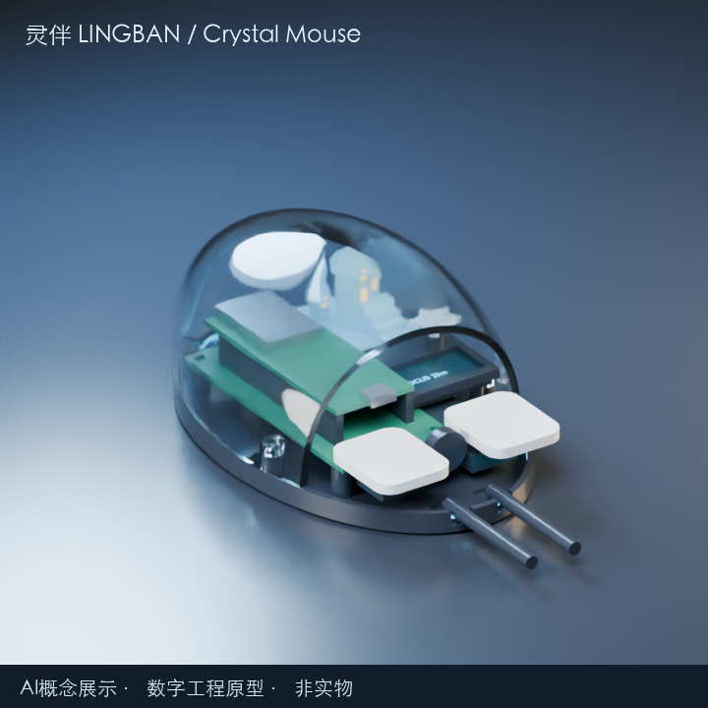
hardware/renders/frames-labeled/0007.png
