huapohen/imagine/hardware/renders/frames-labeled/0008.png

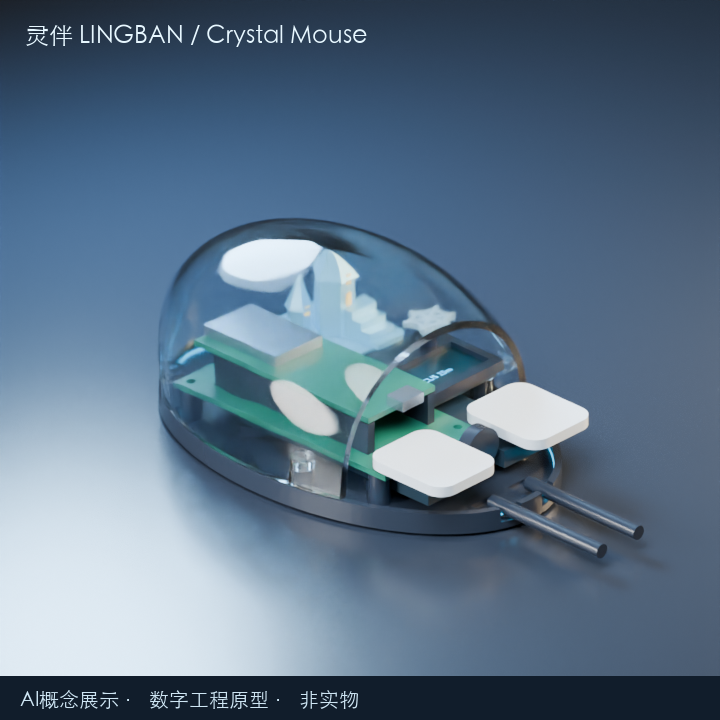
hardware/renders/frames-labeled/0008.png
