huapohen/imagine/hardware/renders/frames-labeled/0009.png

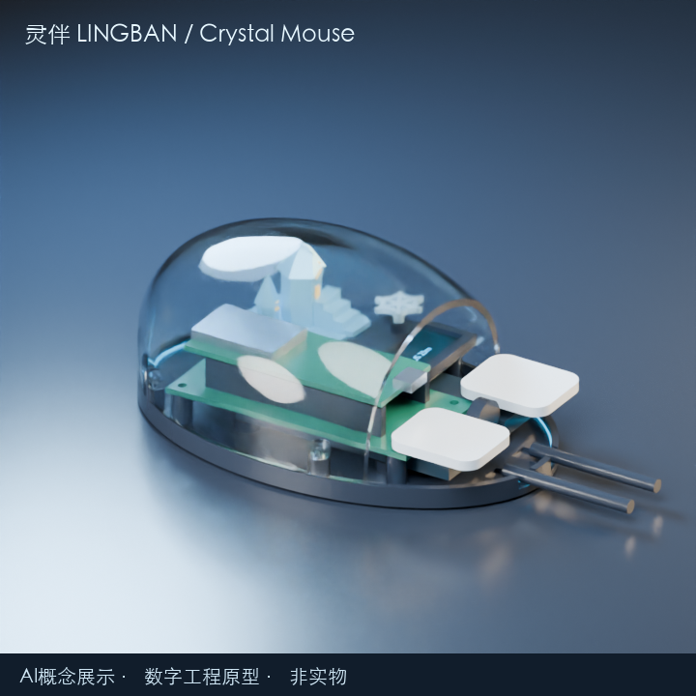
hardware/renders/frames-labeled/0009.png
