huapohen/imagine/hardware/renders/frames-labeled/0011.png

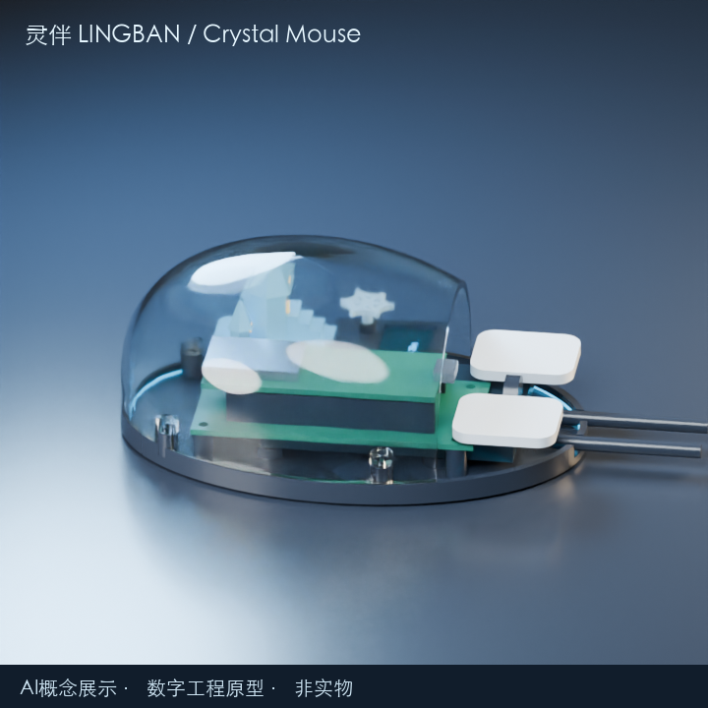
hardware/renders/frames-labeled/0011.png
