huapohen/imagine/hardware/renders/frames-labeled/0014.png

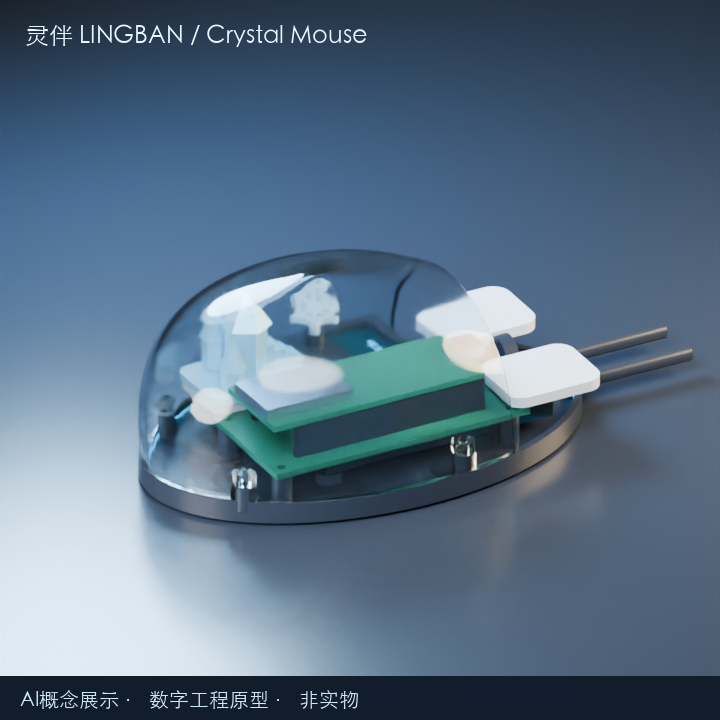
hardware/renders/frames-labeled/0014.png
