huapohen/imagine/hardware/renders/frames-labeled/0016.png

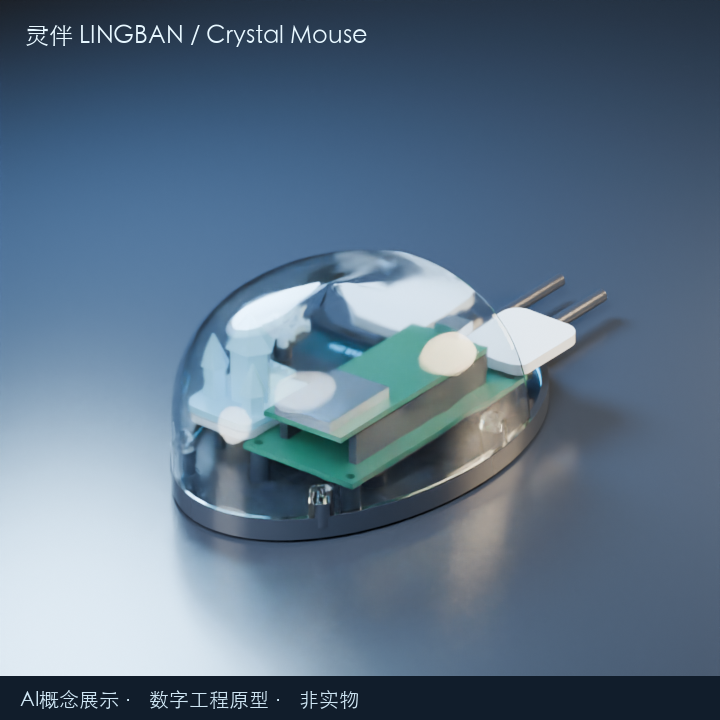
hardware/renders/frames-labeled/0016.png
