huapohen/imagine/hardware/renders/frames-labeled/0017.png

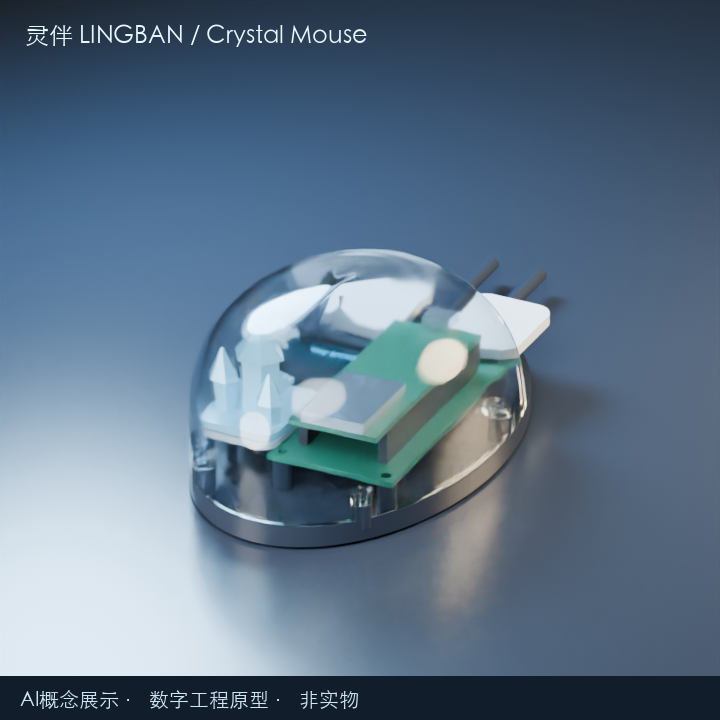
hardware/renders/frames-labeled/0017.png
