huapohen/imagine/hardware/renders/frames-labeled/0018.png

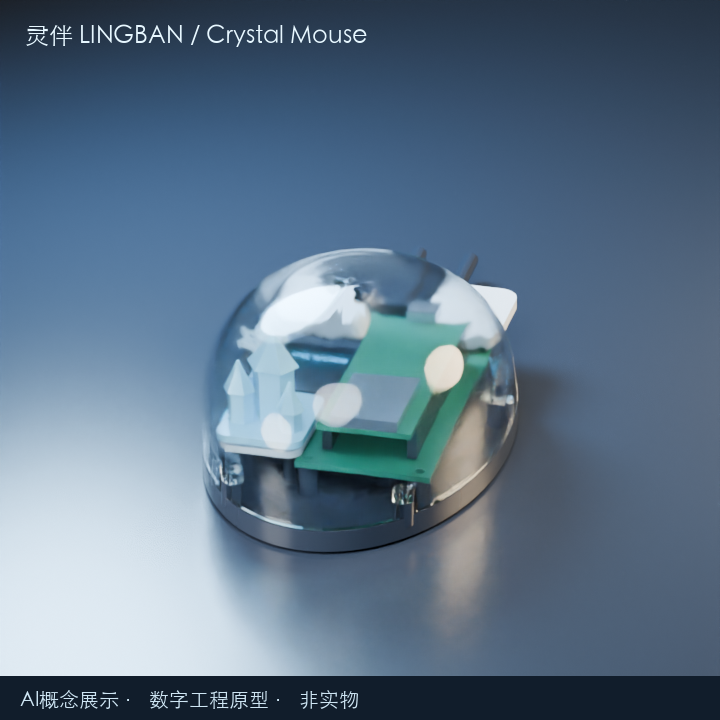
hardware/renders/frames-labeled/0018.png
