huapohen/imagine/hardware/renders/frames-labeled/0020.png

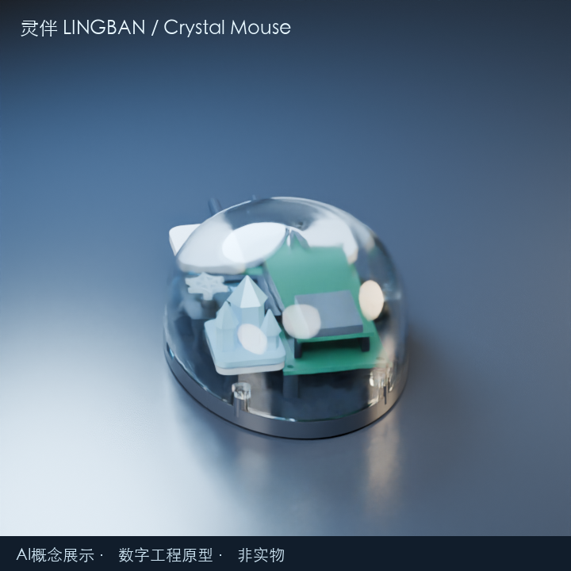
hardware/renders/frames-labeled/0020.png
