huapohen/imagine/hardware/renders/frames-labeled/0021.png

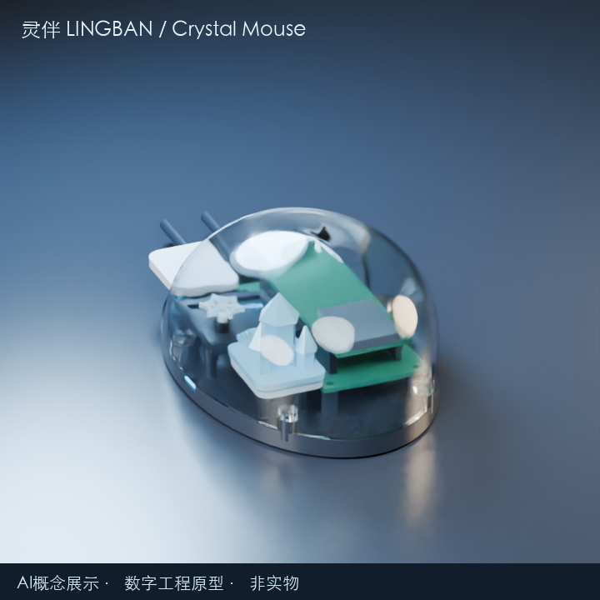
hardware/renders/frames-labeled/0021.png
