huapohen/imagine/hardware/renders/frames-labeled/0023.png

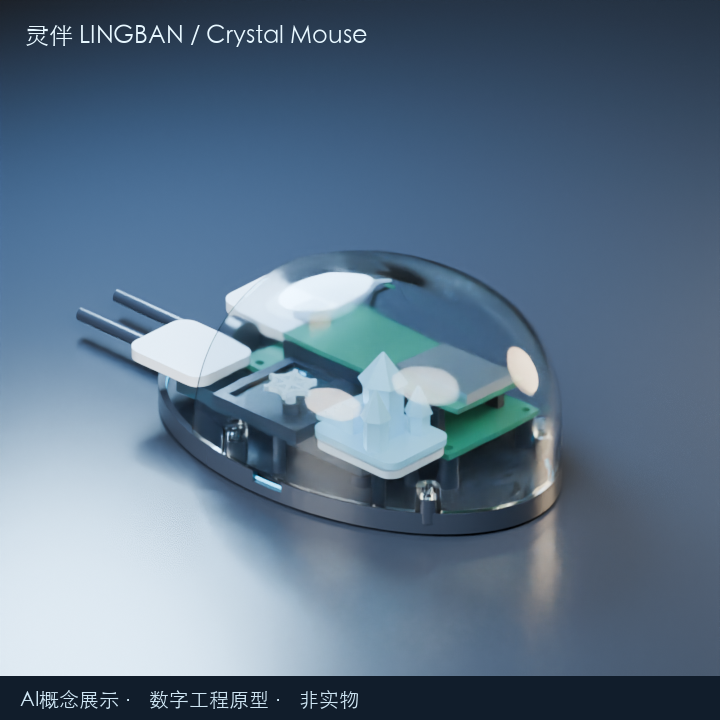
hardware/renders/frames-labeled/0023.png
