huapohen/imagine/hardware/renders/frames-labeled/0024.png

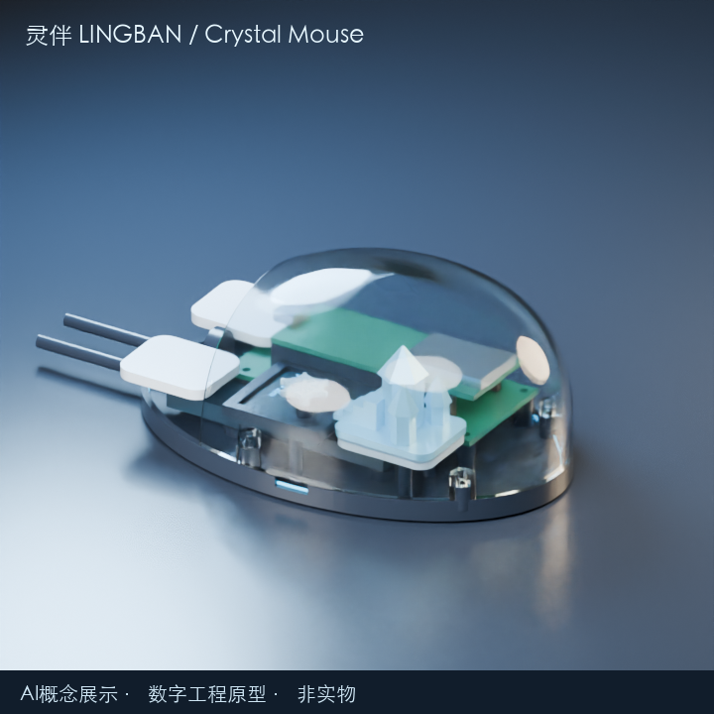
hardware/renders/frames-labeled/0024.png
