huapohen/imagine/hardware/renders/frames-labeled/0025.png

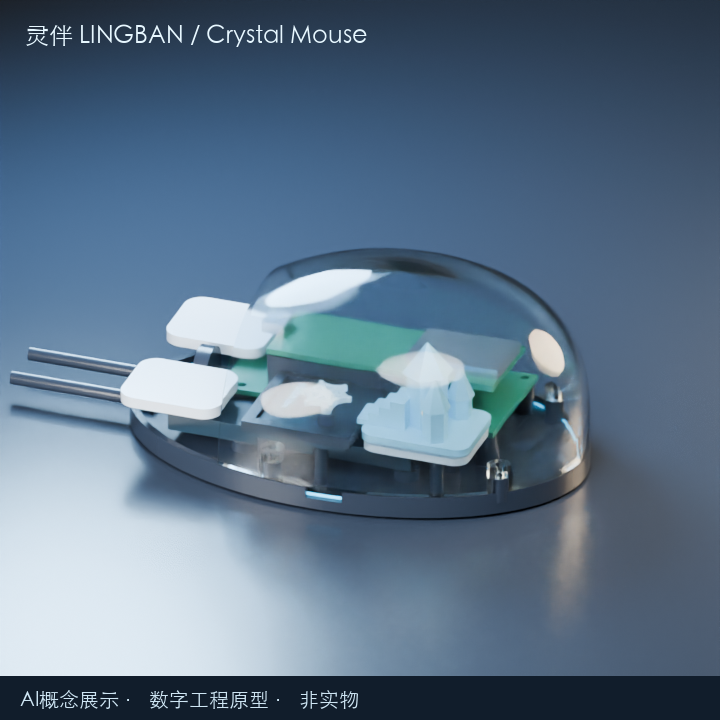
hardware/renders/frames-labeled/0025.png
