huapohen/imagine/hardware/renders/frames-labeled/0026.png

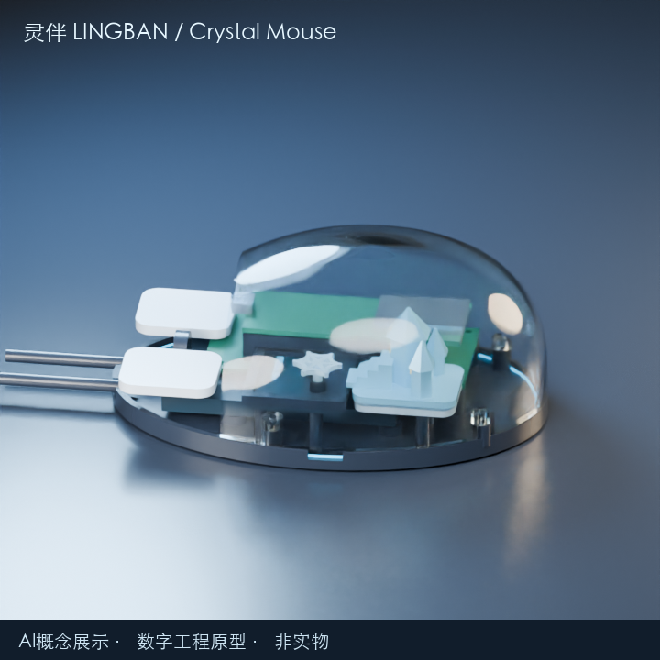
hardware/renders/frames-labeled/0026.png
