huapohen/imagine/hardware/renders/frames-labeled/0027.png

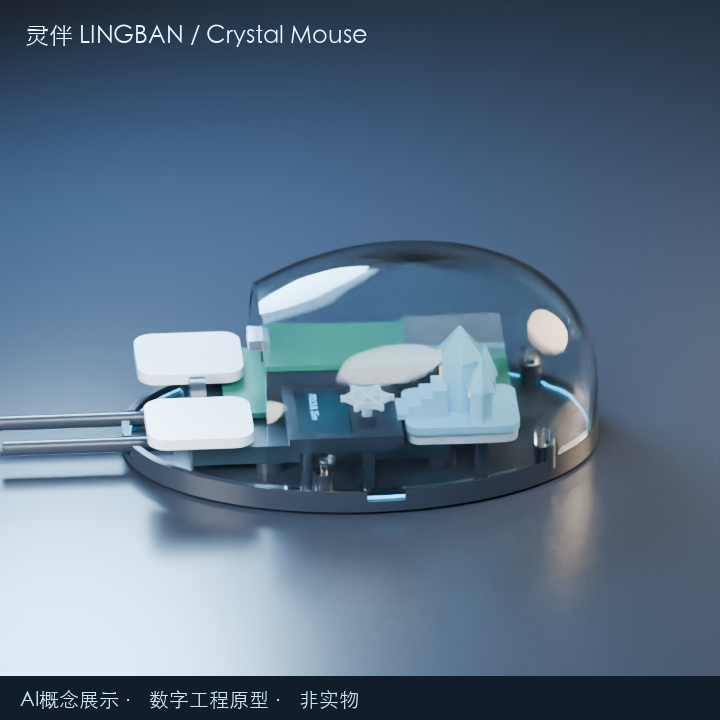
hardware/renders/frames-labeled/0027.png
