huapohen/imagine/hardware/renders/frames-labeled/0028.png

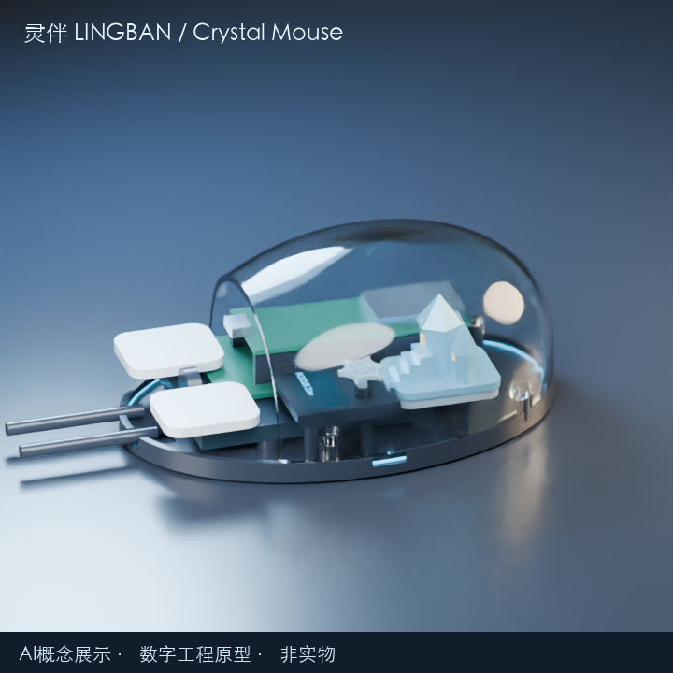
hardware/renders/frames-labeled/0028.png
