huapohen/imagine/hardware/renders/frames-labeled/0029.png

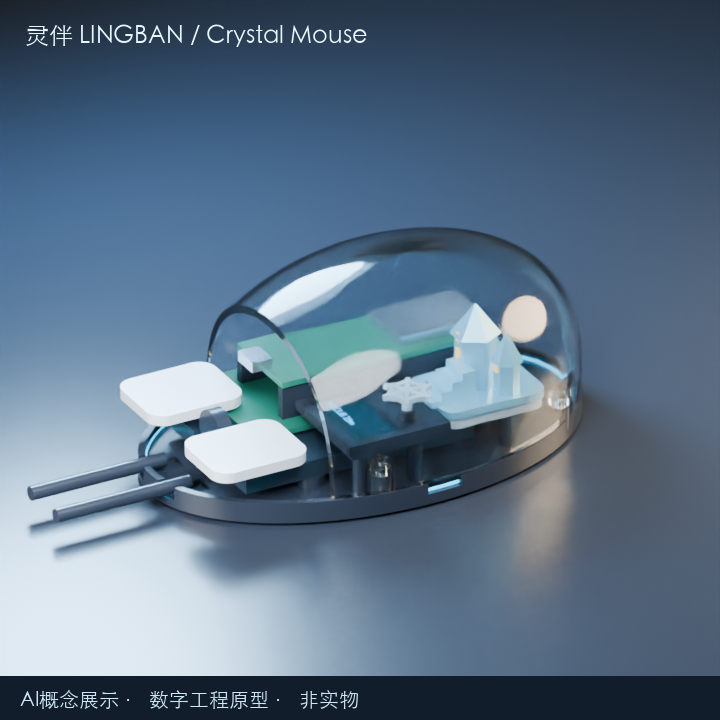
hardware/renders/frames-labeled/0029.png
