huapohen/imagine/hardware/renders/hero_raw.png

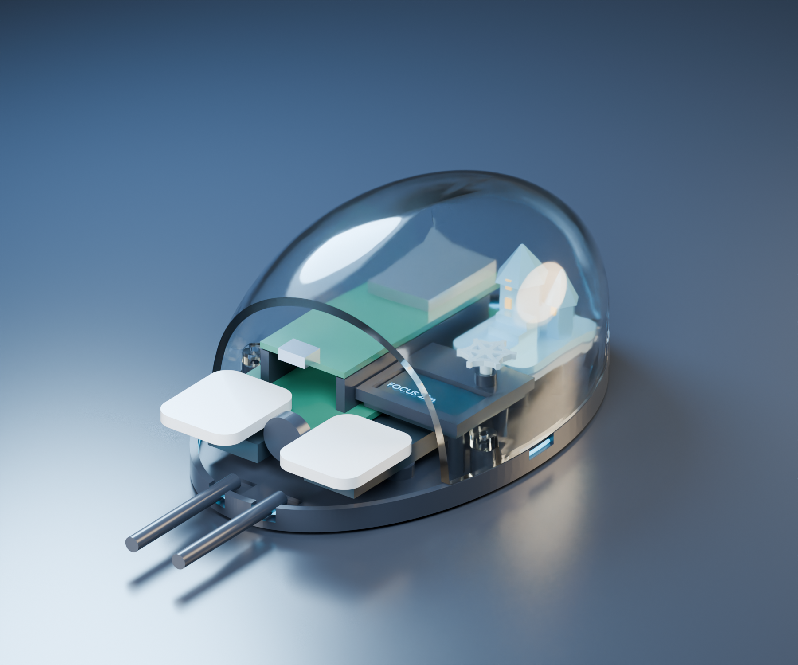
hardware/renders/hero_raw.png
