huapohen/imagine/media/demo/contact-sheet.jpg

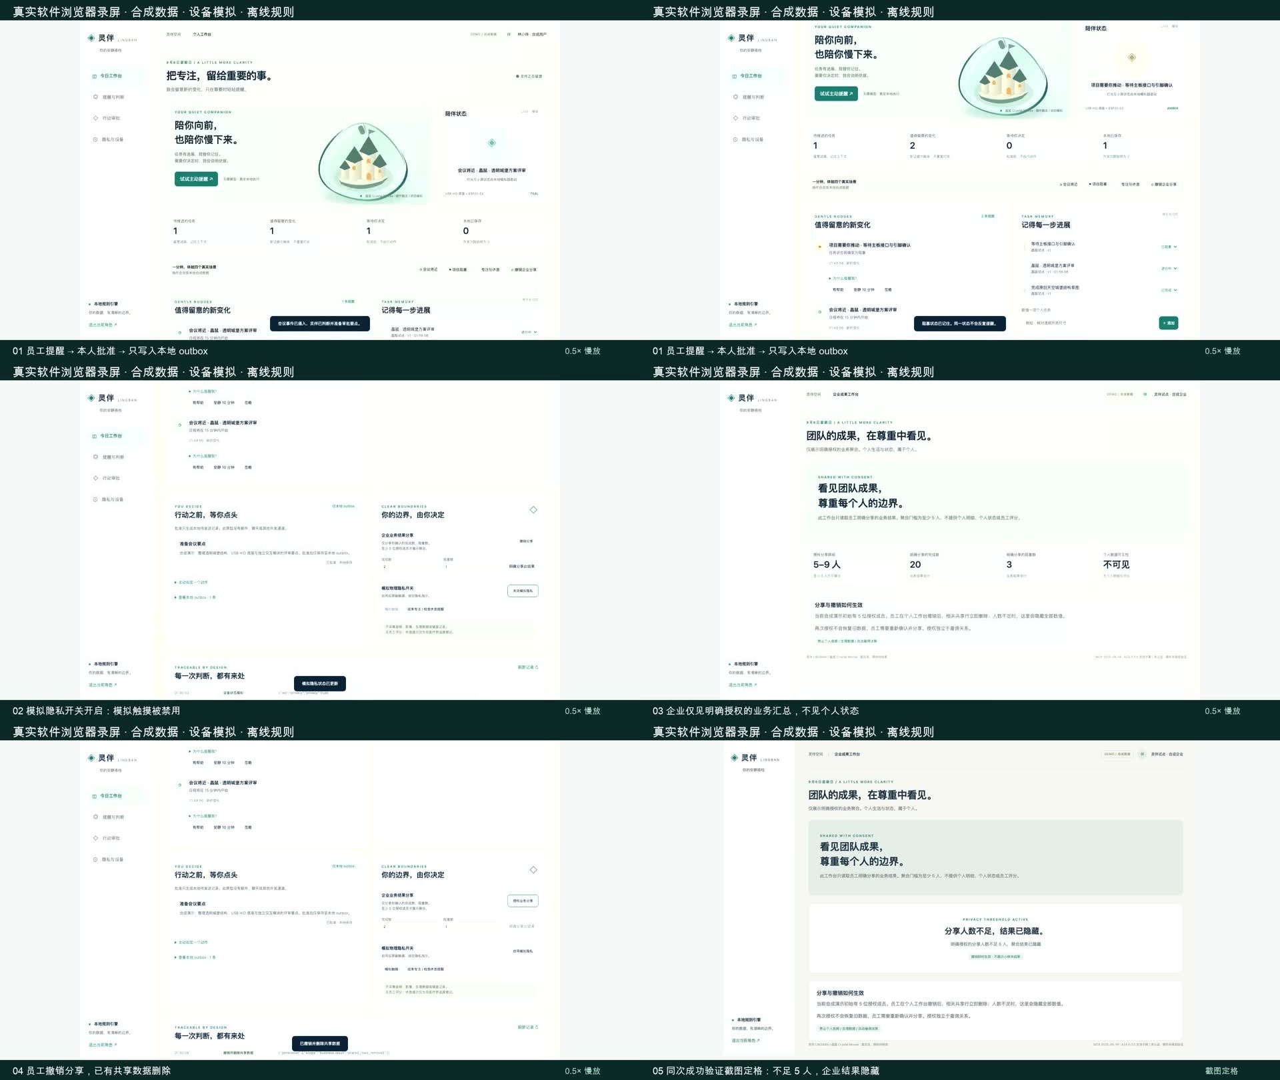
media/demo/contact-sheet.jpg
