huapohen/imagine/media/demo/employee_0.4.png

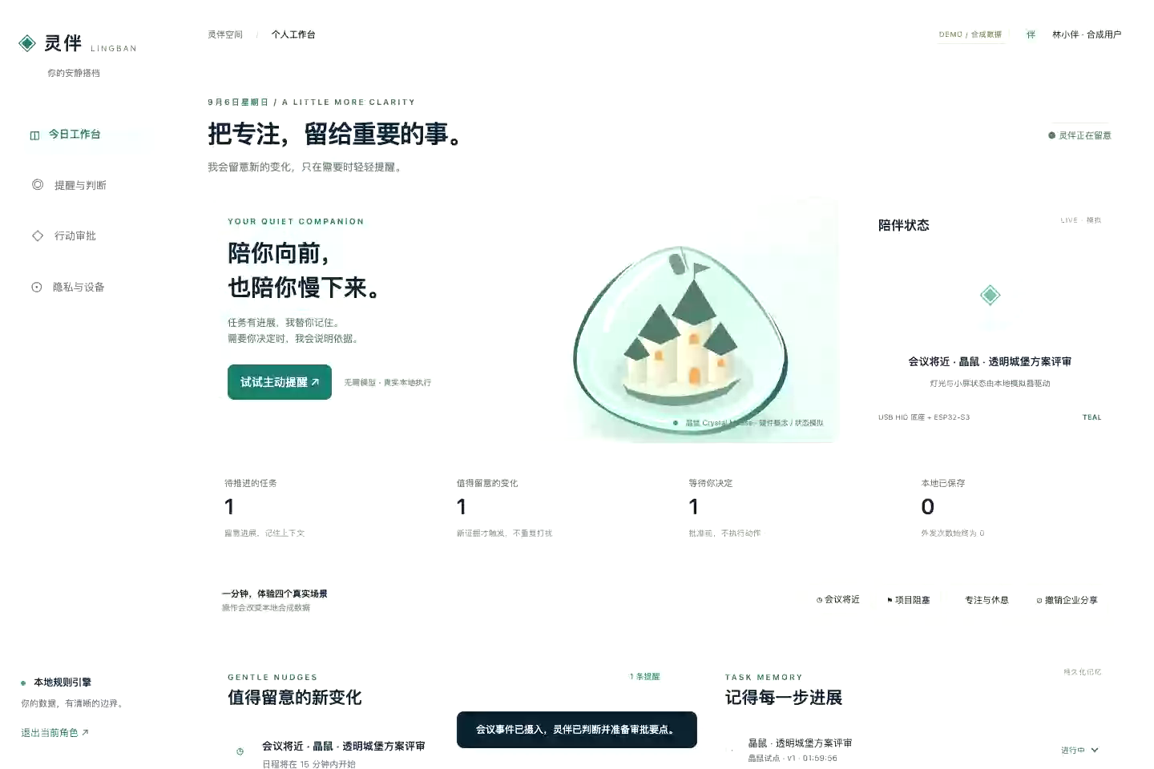
media/demo/employee_0.4.png
