huapohen/imagine/media/demo/employee_1.8.png

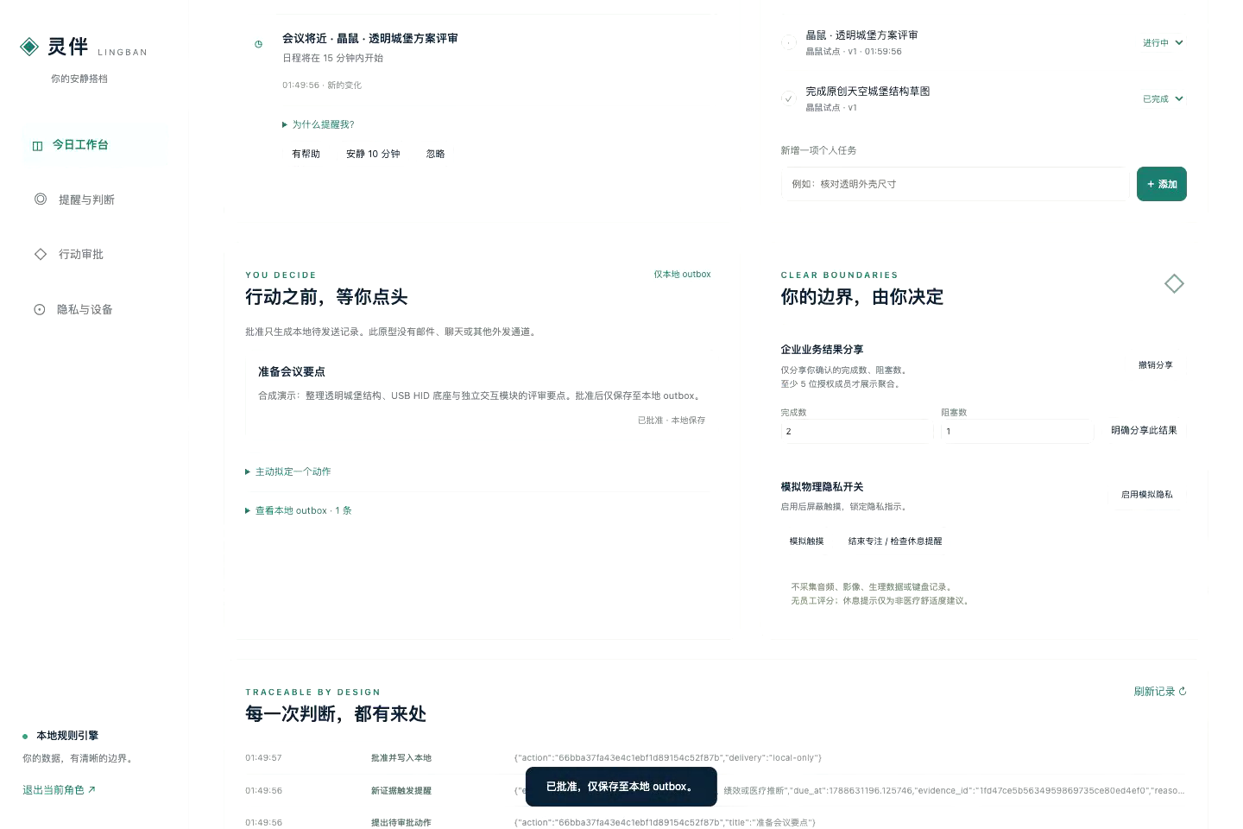
media/demo/employee_1.8.png
