huapohen/imagine/media/demo/employee_8.2.png

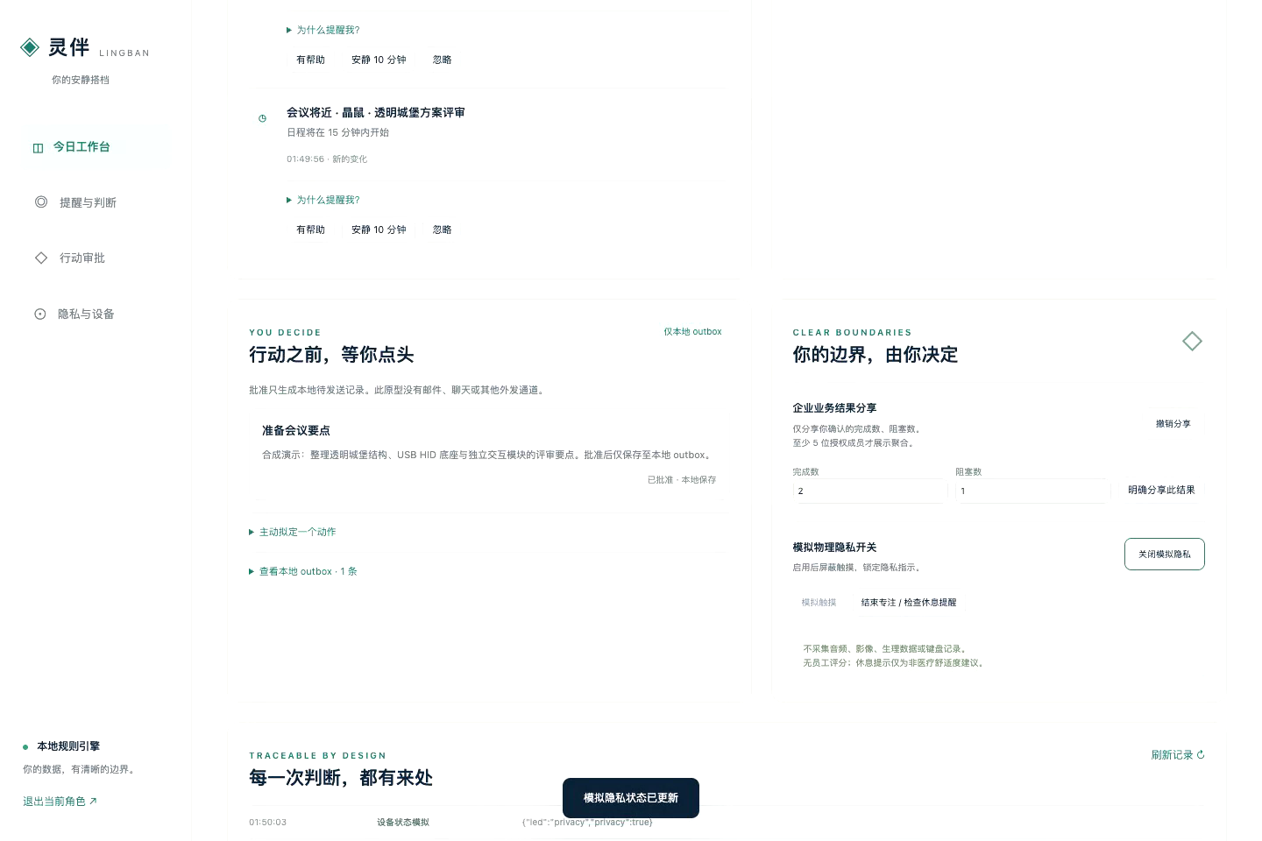
media/demo/employee_8.2.png
