huapohen/imagine/media/demo/enterprise_0.2.png

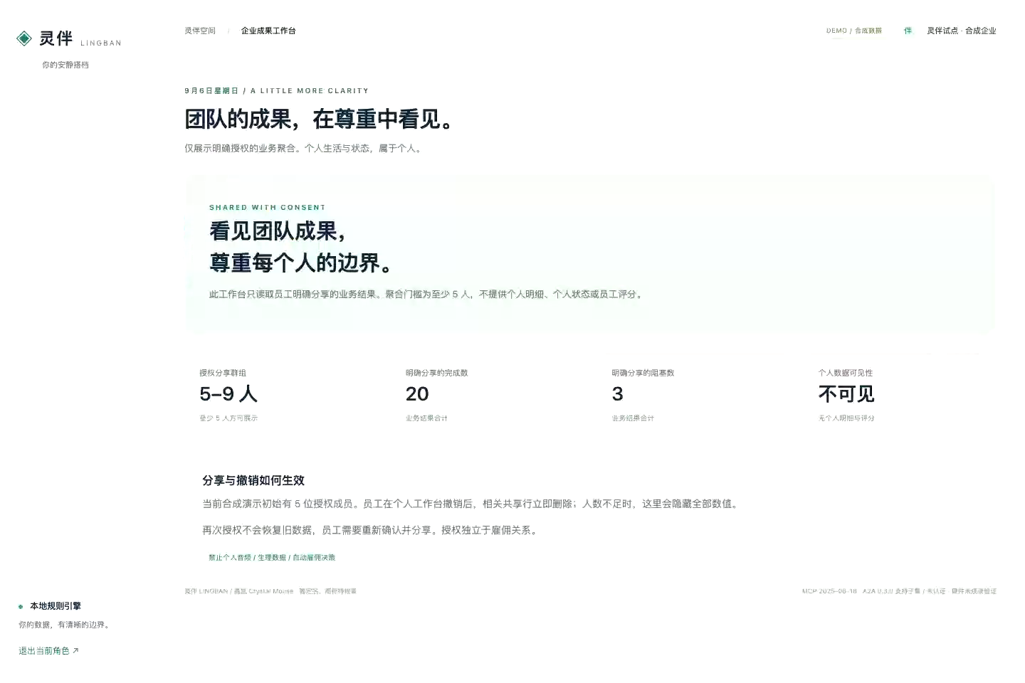
media/demo/enterprise_0.2.png
