huapohen/imagine/media/demo/final_n225.png

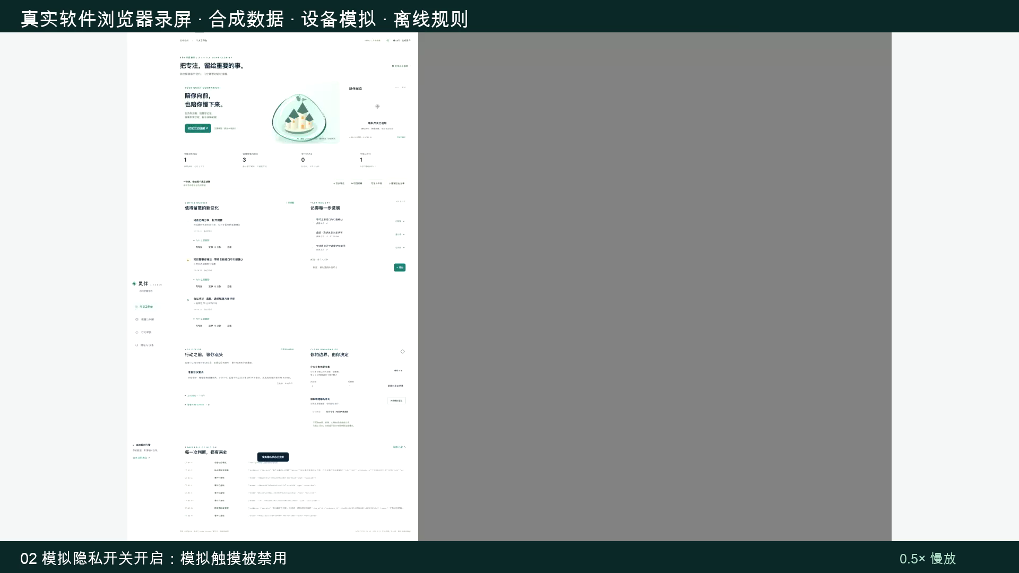
media/demo/final_n225.png
