huapohen/imagine/media/demo/frame_01s.jpg

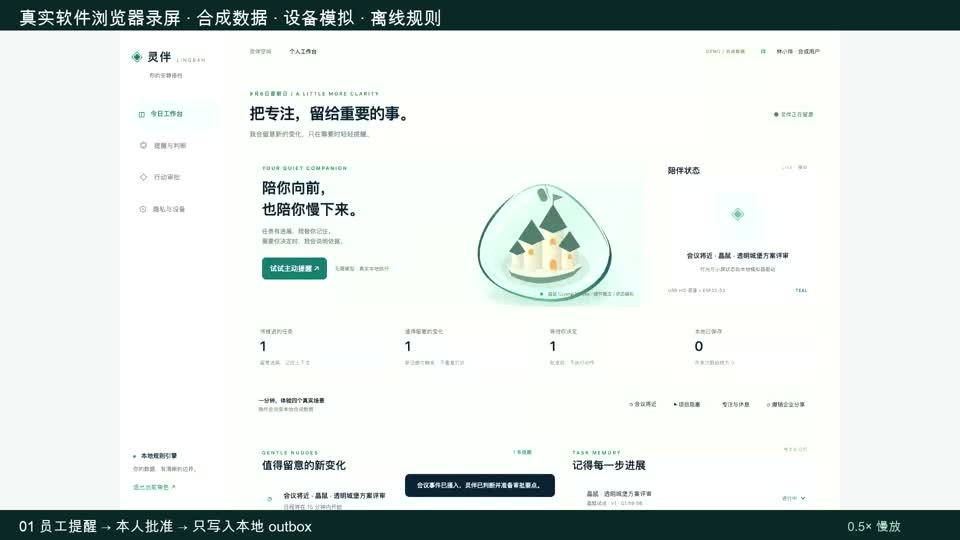
media/demo/frame_01s.jpg
