huapohen/imagine/media/demo/frame_05s.jpg

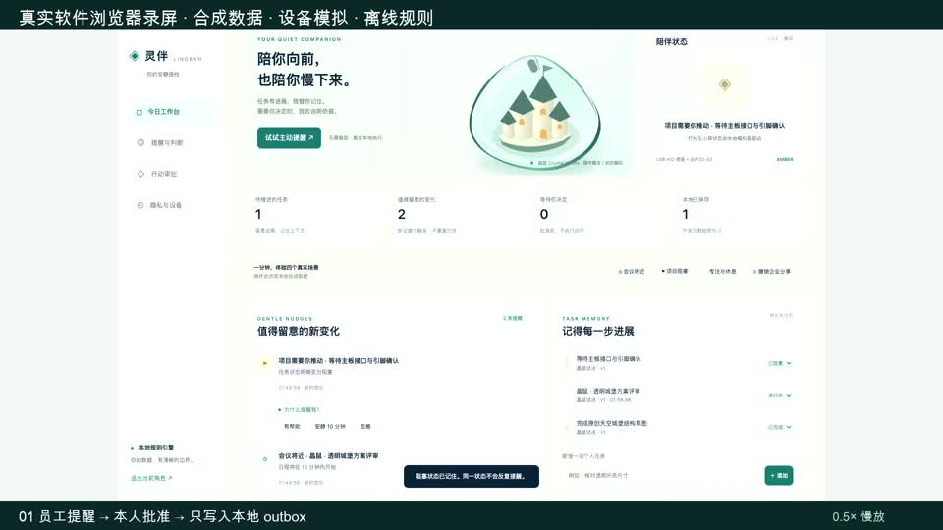
media/demo/frame_05s.jpg
