huapohen/imagine/media/demo/frame_09s.jpg

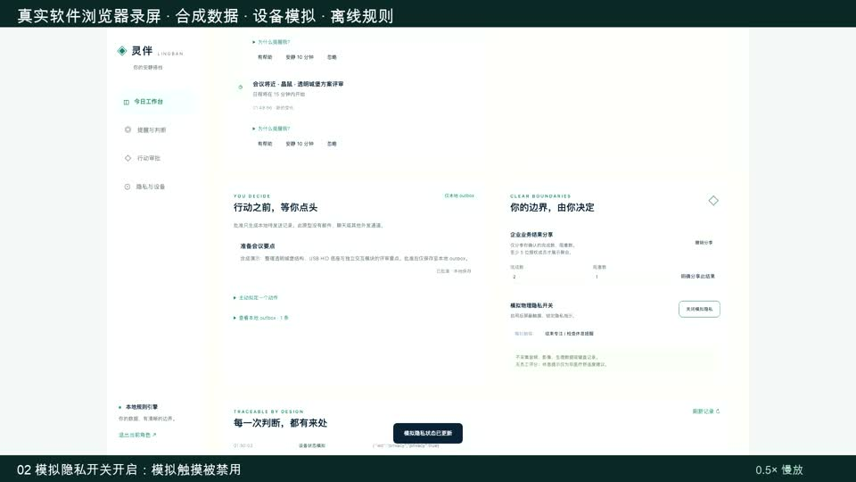
media/demo/frame_09s.jpg
