huapohen/imagine/media/demo/frame_14s.jpg

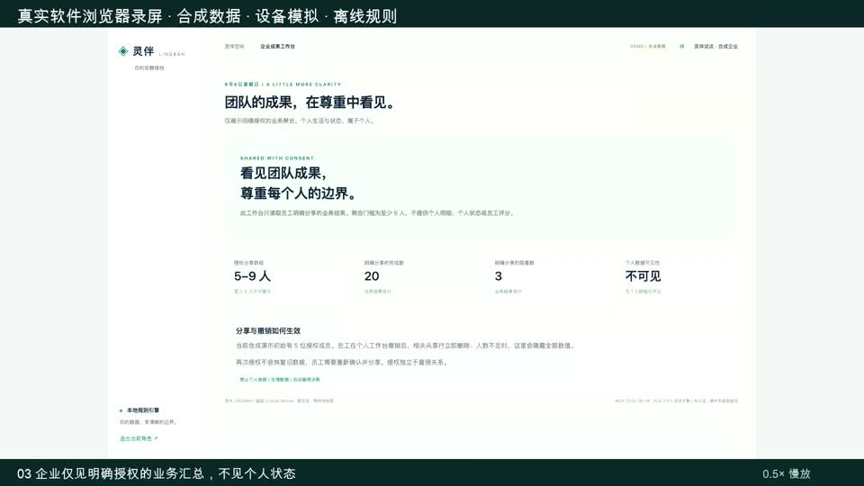
media/demo/frame_14s.jpg
