huapohen/imagine/media/demo/frame_24s.jpg

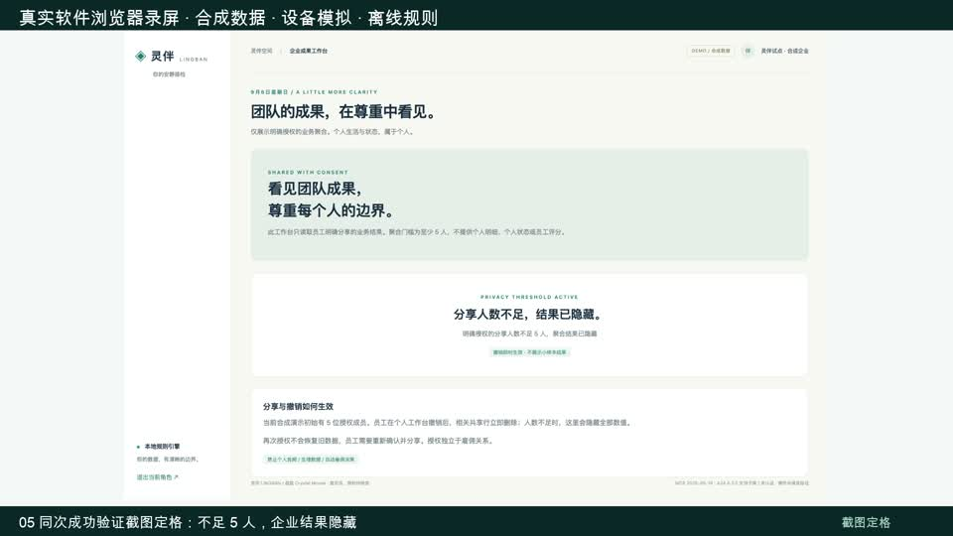
media/demo/frame_24s.jpg
