huapohen/imagine/media/demo/source_69599f6eb1e6de31e93728e8ee1cacb9_contact.jpg

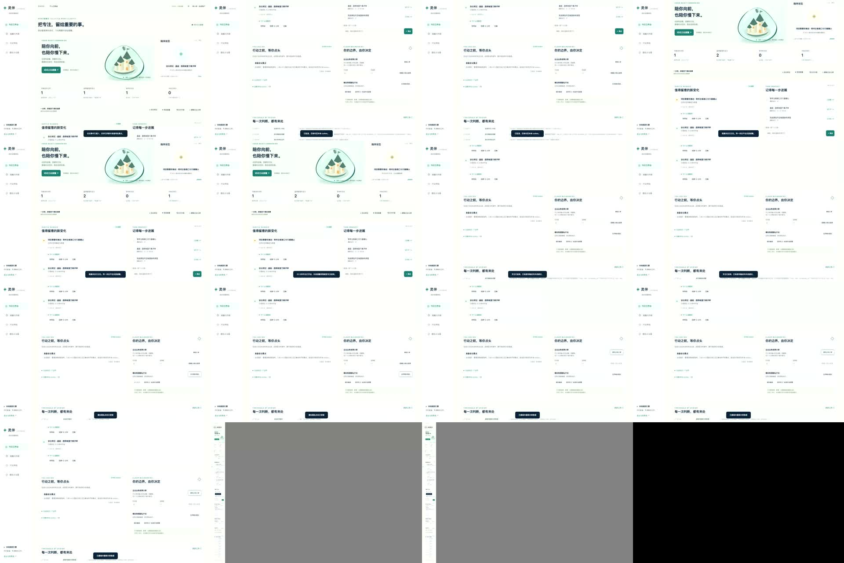
media/demo/source_69599f6eb1e6de31e93728e8ee1cacb9_contact.jpg
