huapohen/imagine/media/demo/source_c66339f90bb24ee53379e2f4e372741b_contact.jpg

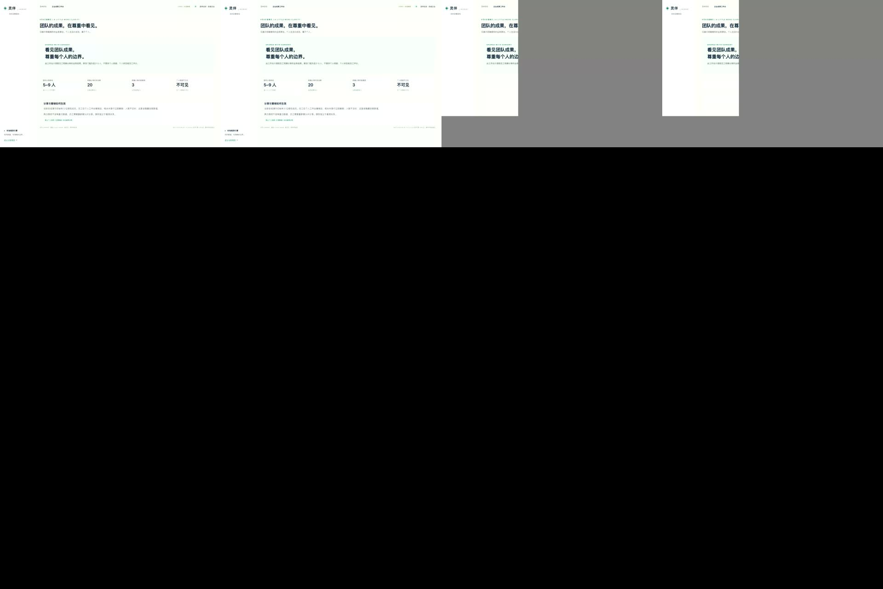
media/demo/source_c66339f90bb24ee53379e2f4e372741b_contact.jpg
