huapohen/imagine/media/qa/ALL_8_CONCEPTS.jpg

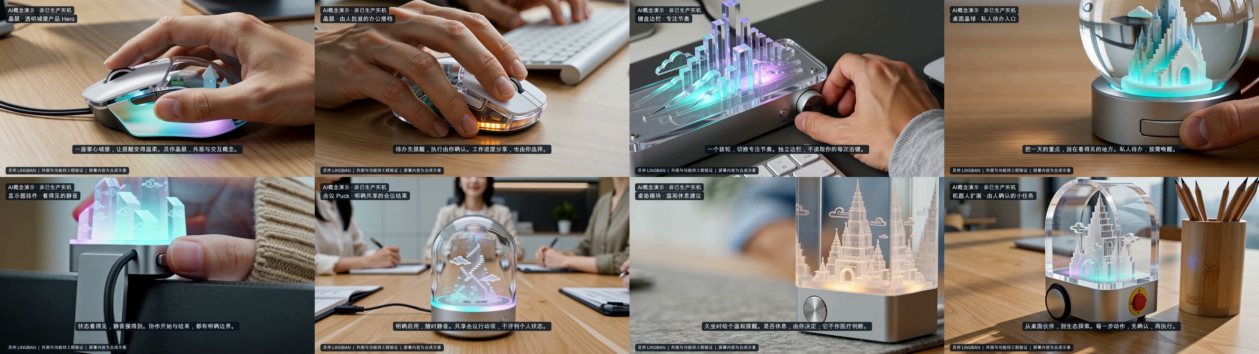
media/qa/ALL_8_CONCEPTS.jpg
