huapohen/imagine/media/references/crystal-mouse-cad-landscape.png

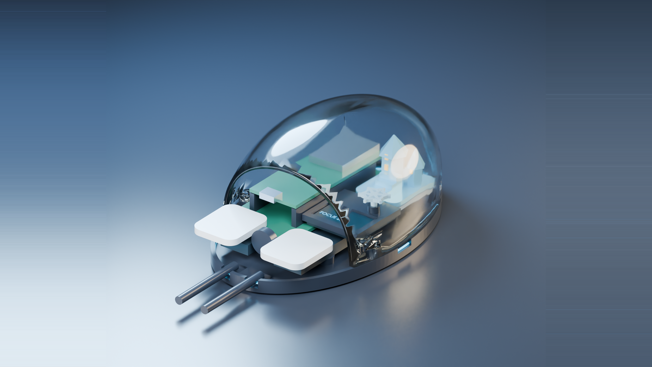
media/references/crystal-mouse-cad-landscape.png
