huapohen/imagine/hardware/cad/exports/08_esp_module_placeholder.step

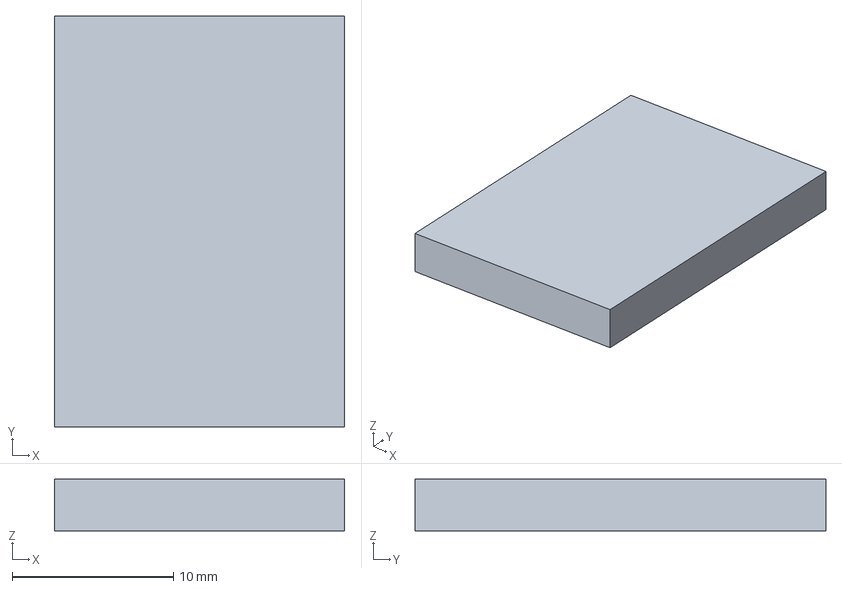
[picture p61: CAD file, 2026-09-05]
hardware/cad/exports/08_esp_module_placeholder.step
18.0 x 25.5 x 3.20 mm
