huapohen/imagine/hardware/cad/exports/16_castle_socket_sled.step

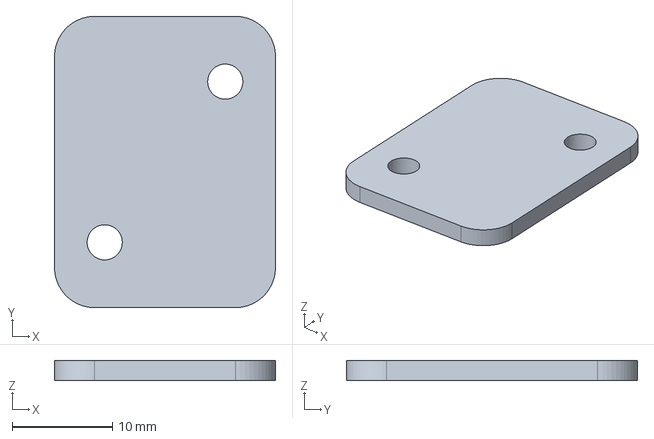
[picture p62: CAD file, 2026-09-05]
hardware/cad/exports/16_castle_socket_sled.step
22.0 x 29.0 x 2.00 mm
