huapohen/imagine/hardware/cad/exports/14_display_placeholder.step

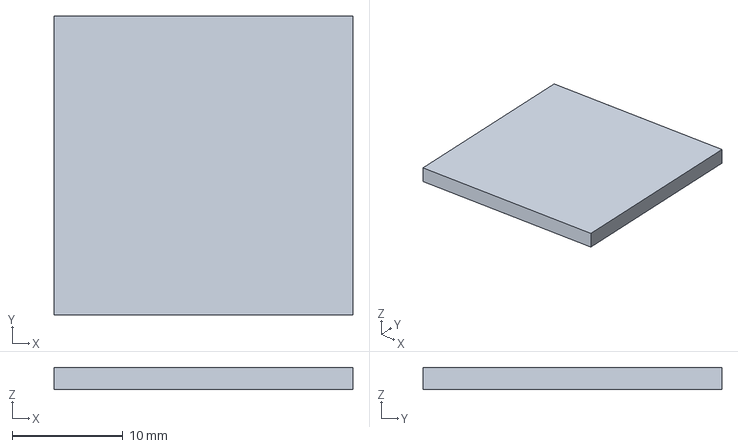
[picture p63: CAD file, 2026-09-05]
hardware/cad/exports/14_display_placeholder.step
27.0 x 27.0 x 2.00 mm
