huapohen/imagine/hardware/cad/exports/11_cloud_stair_castle.step

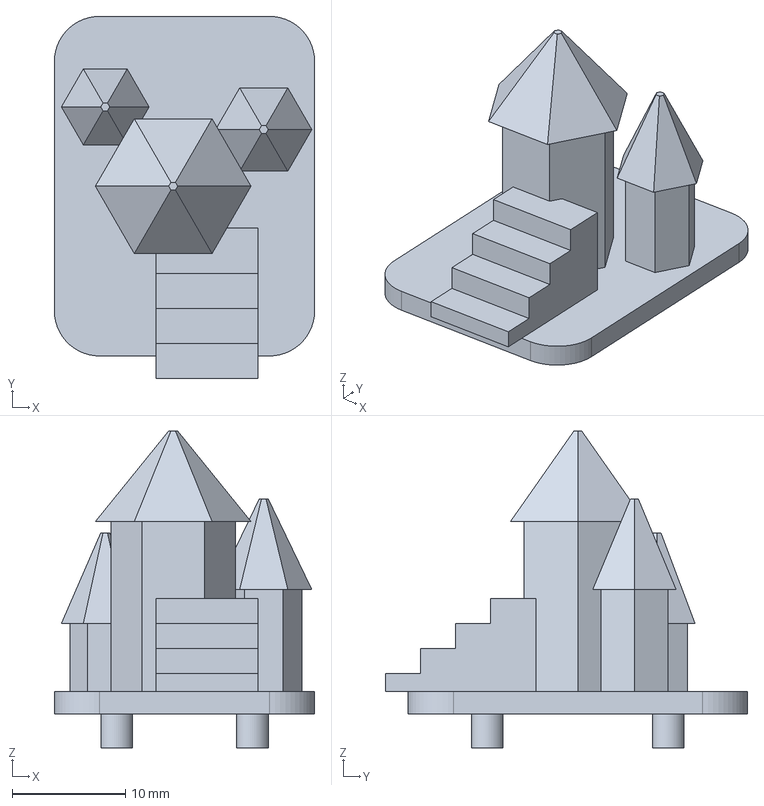
[picture p64: CAD file, 2026-09-05]
hardware/cad/exports/11_cloud_stair_castle.step
23.0 x 32.0 x 28.0 mm
