huapohen/imagine/hardware/cad/exports/13_screen_frame.step

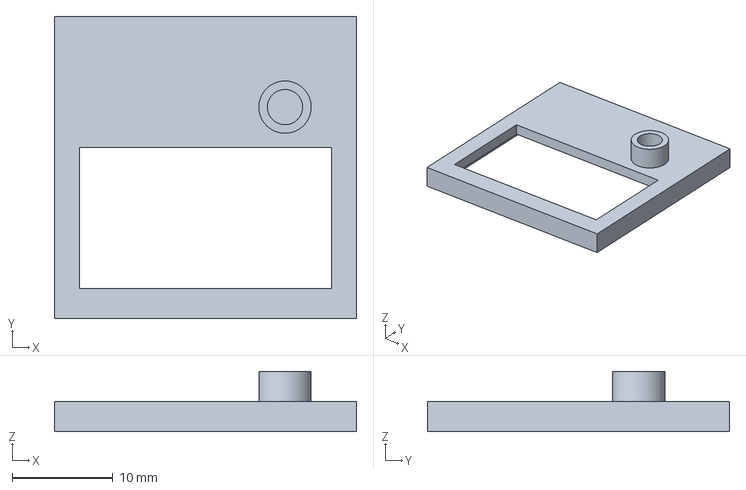
[picture p65: CAD file, 2026-09-05]
hardware/cad/exports/13_screen_frame.step
30.0 x 30.0 x 6.00 mm
