huapohen/imagine/hardware/cad/exports/15_display_glass.step

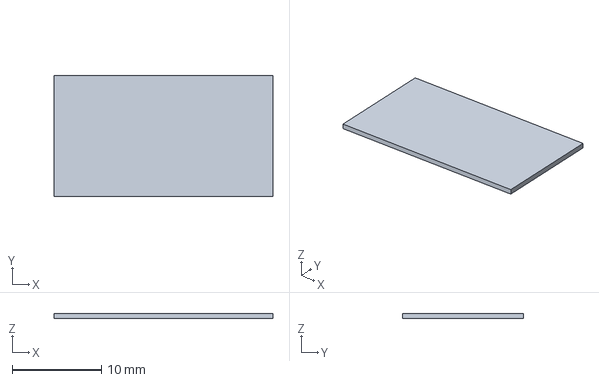
[picture p66: CAD file, 2026-09-05]
hardware/cad/exports/15_display_glass.step
24.5 x 13.5 x 0.6 mm
