huapohen/imagine/docs/verification/browser/employee-desktop.png

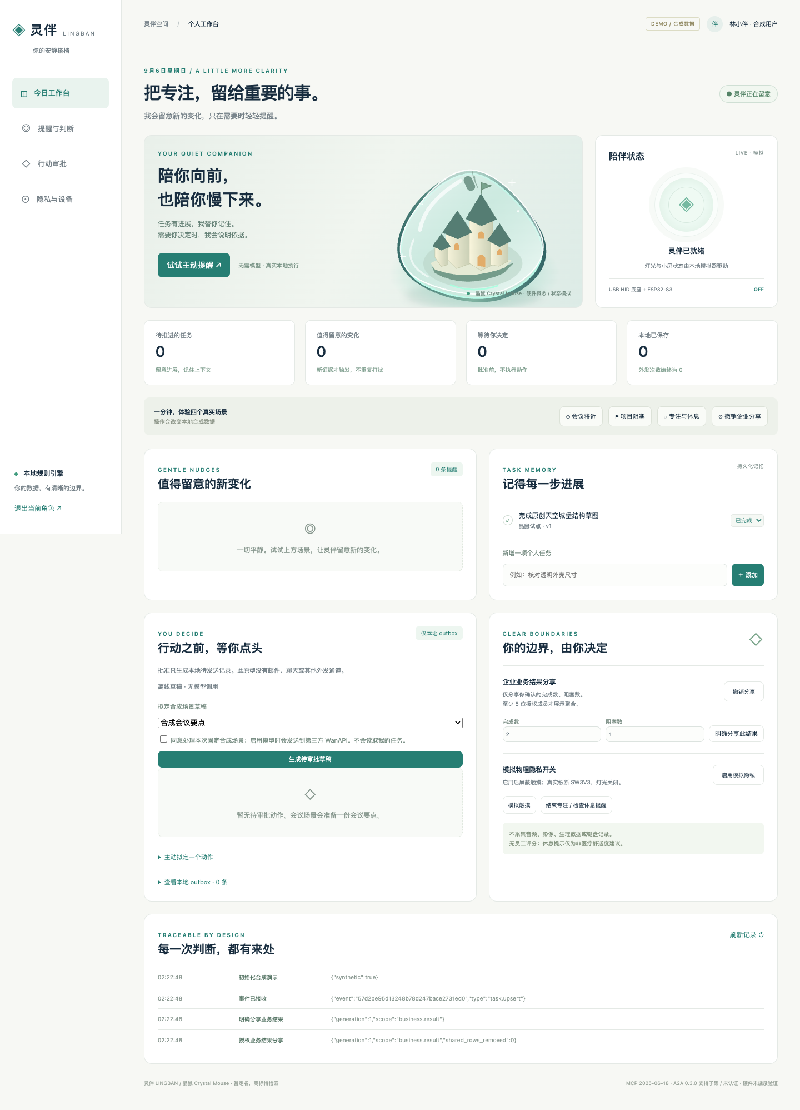
docs/verification/browser/employee-desktop.png
