huapohen/imagine/docs/verification/browser/employee-mobile.png

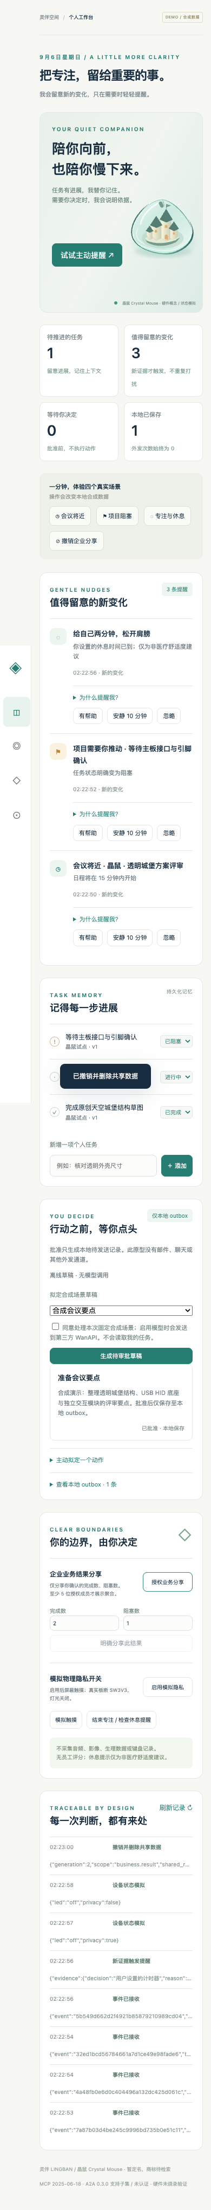
docs/verification/browser/employee-mobile.png
