huapohen/imagine/docs/verification/browser/employee-privacy.png

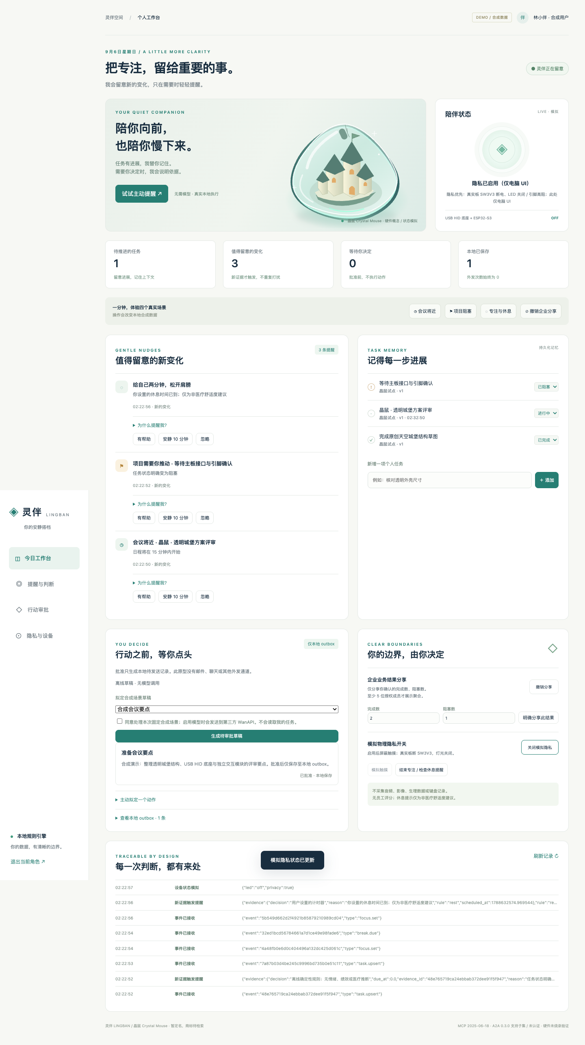
docs/verification/browser/employee-privacy.png
