huapohen/imagine/docs/verification/browser/enterprise-revoked.png

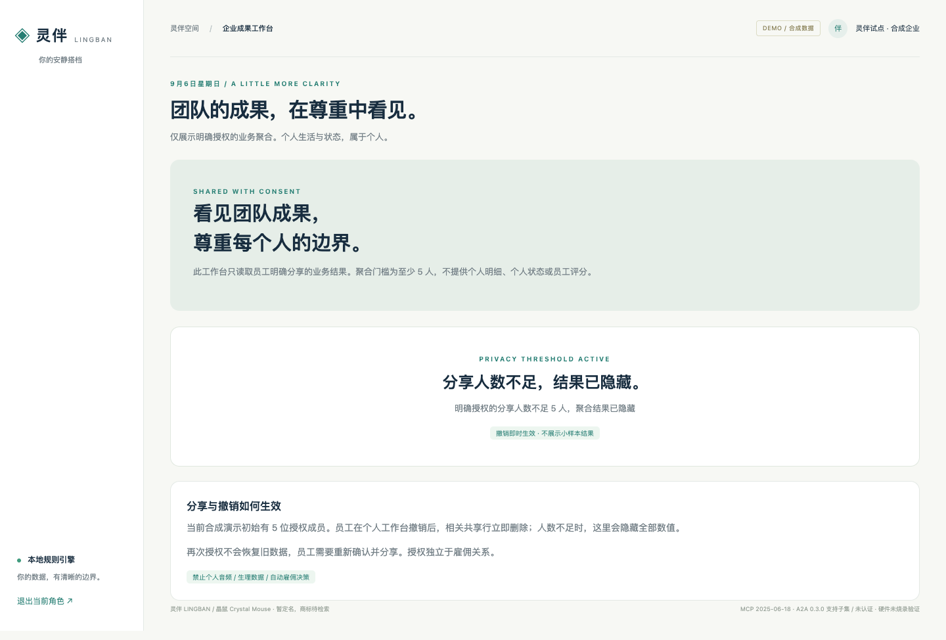
docs/verification/browser/enterprise-revoked.png
