huapohen/imagine/docs/verification/portal-desktop.png

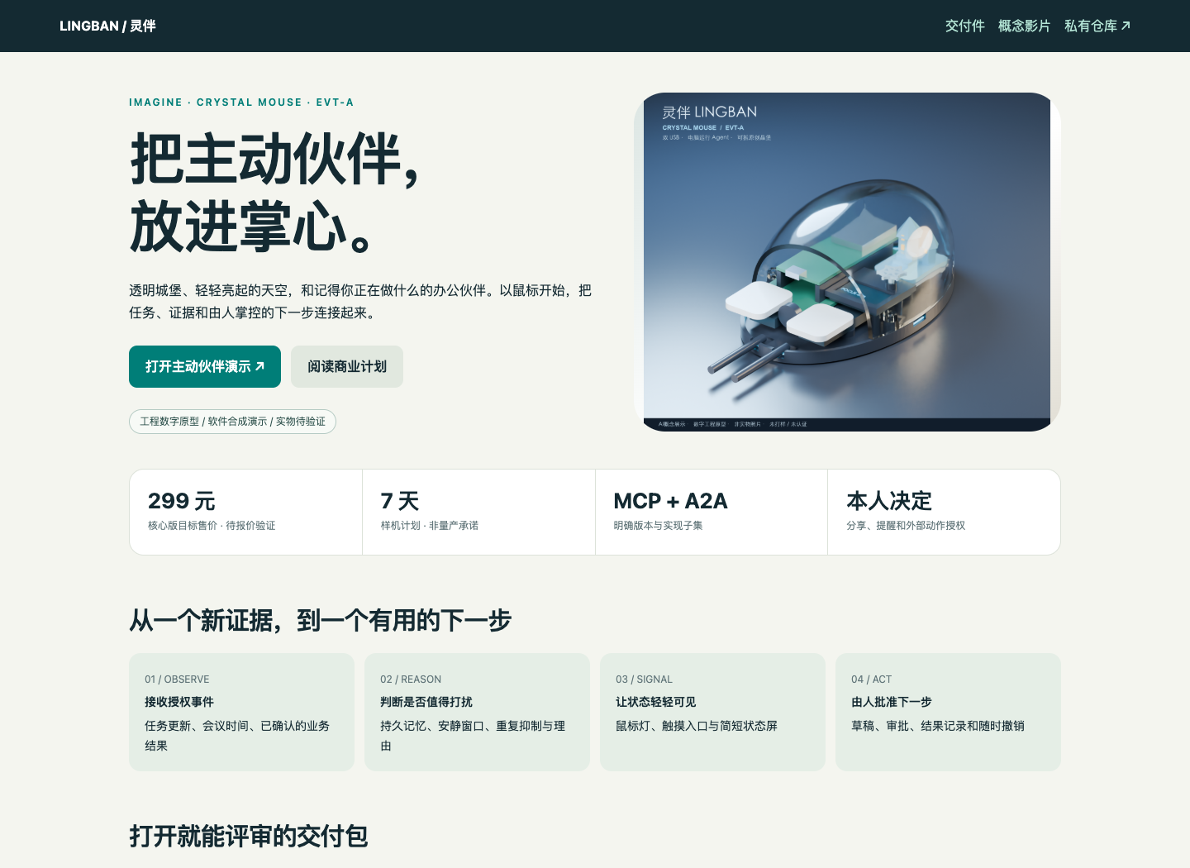
docs/verification/portal-desktop.png
