huapohen/imagine/docs/verification/portal-mobile.png

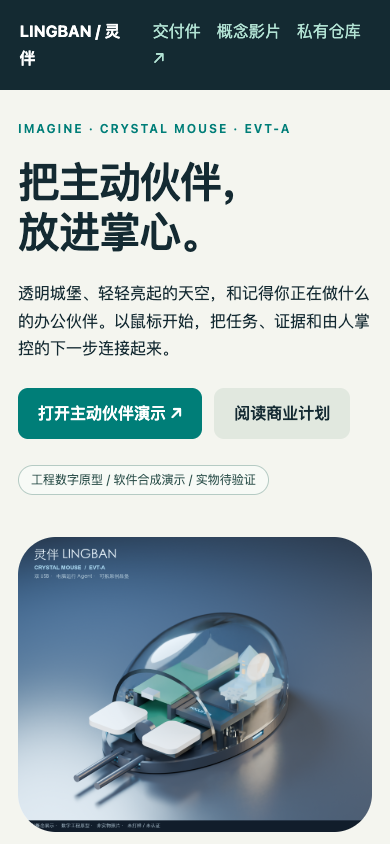
docs/verification/portal-mobile.png
