huapohen/imagine/media/qa/01_crystal_mouse_focus_05s.jpg

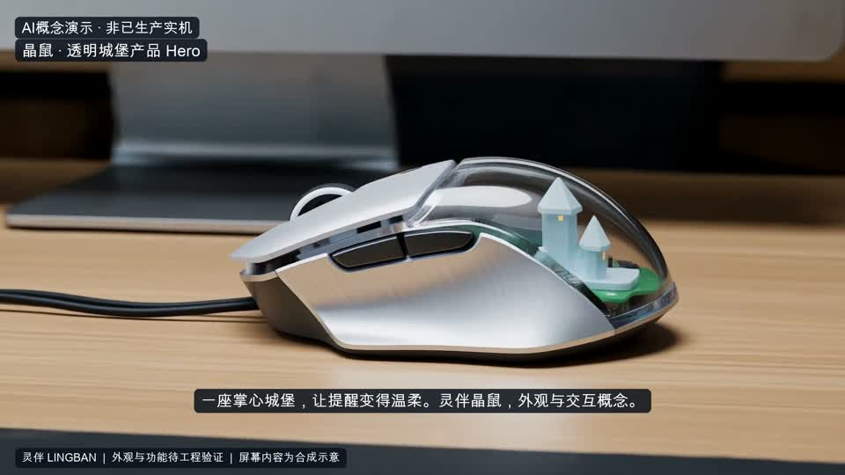
media/qa/01_crystal_mouse_focus_05s.jpg
