huapohen/imagine/media/qa/01_crystal_mouse_focus_09s.jpg

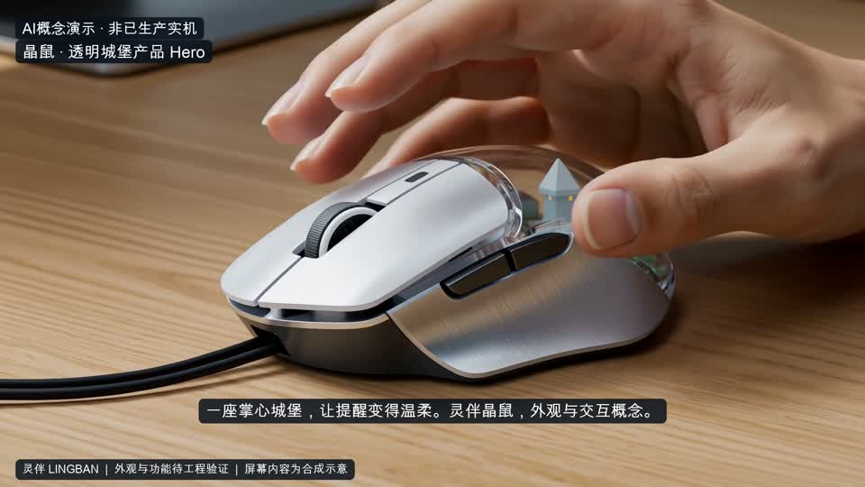
media/qa/01_crystal_mouse_focus_09s.jpg
