huapohen/imagine/media/qa/01_crystal_mouse_focus_13s.jpg

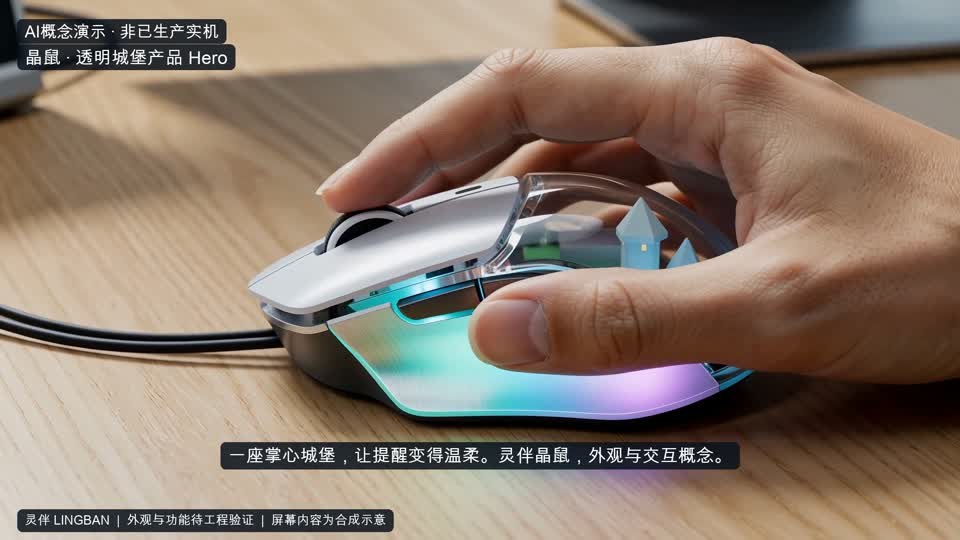
media/qa/01_crystal_mouse_focus_13s.jpg
