huapohen/imagine/media/qa/01_crystal_mouse_focus_contact.jpg

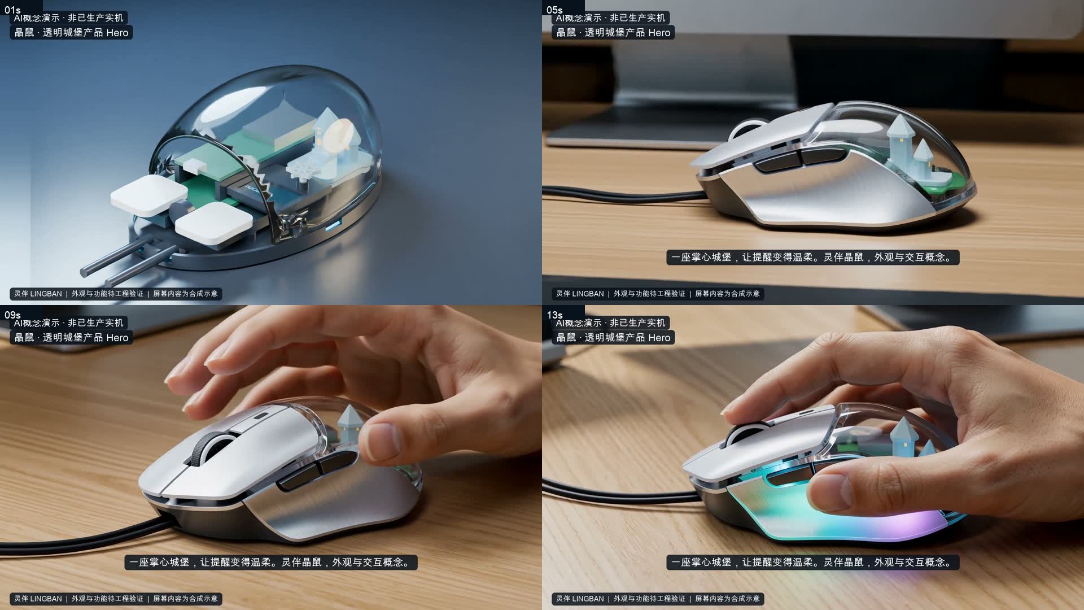
media/qa/01_crystal_mouse_focus_contact.jpg
