huapohen/imagine/media/qa/02_crystal_mouse_workday_05s.jpg

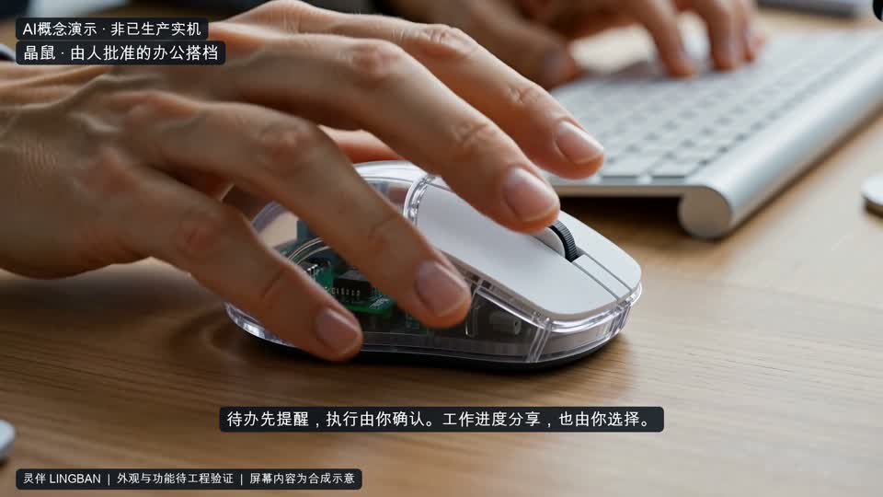
media/qa/02_crystal_mouse_workday_05s.jpg
