huapohen/imagine/media/qa/02_crystal_mouse_workday_09s.jpg

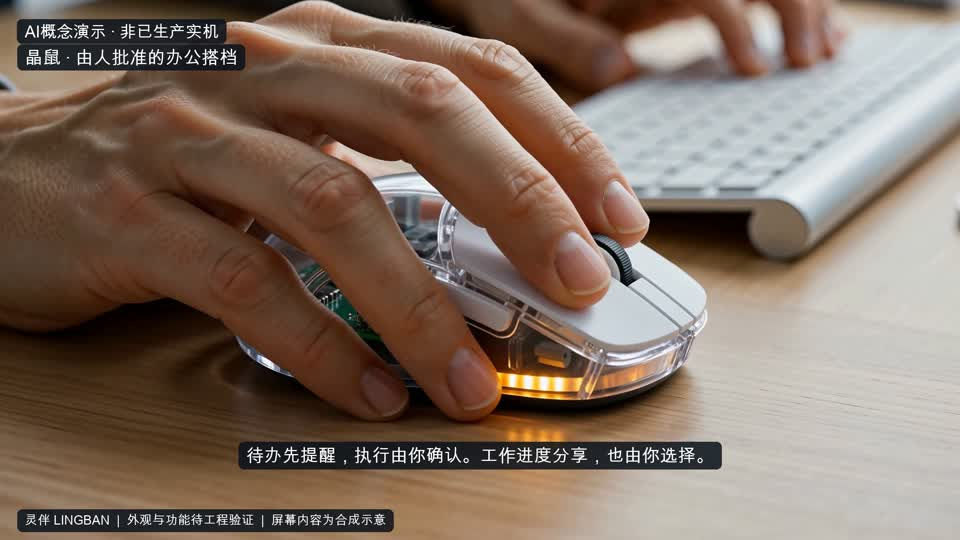
media/qa/02_crystal_mouse_workday_09s.jpg
