huapohen/imagine/media/qa/02_crystal_mouse_workday_contact.jpg

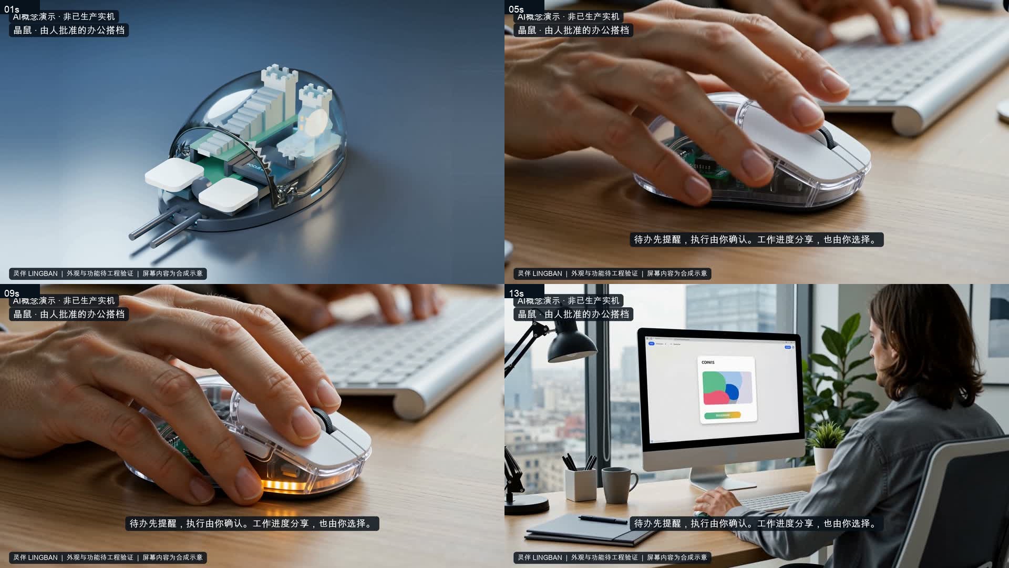
media/qa/02_crystal_mouse_workday_contact.jpg
