huapohen/imagine/media/qa/03_keyboard_sidecar_01s.jpg

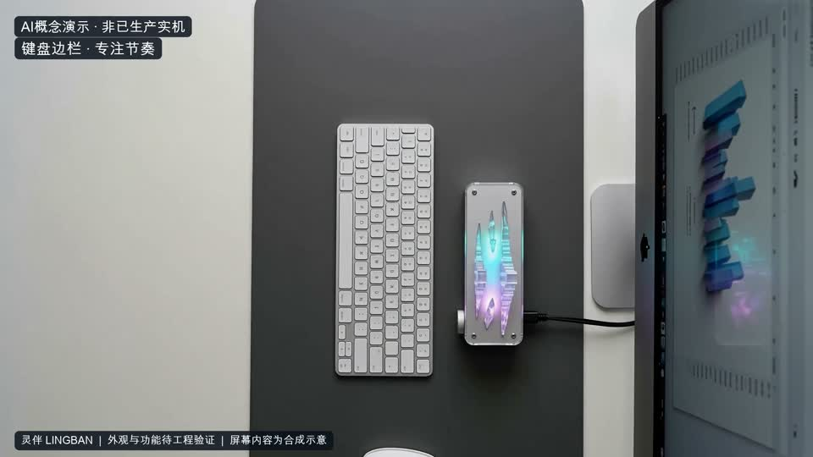
media/qa/03_keyboard_sidecar_01s.jpg
