huapohen/imagine/media/qa/03_keyboard_sidecar_05s.jpg

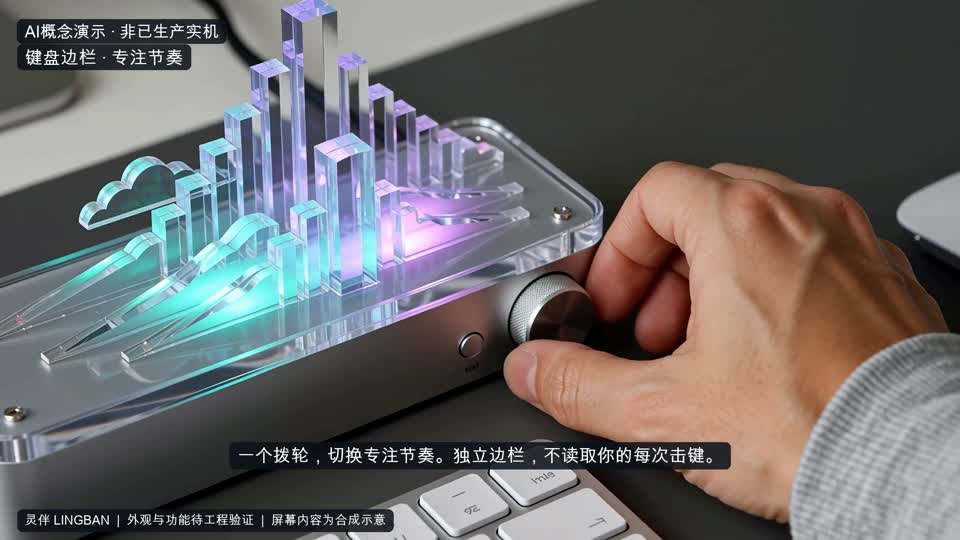
media/qa/03_keyboard_sidecar_05s.jpg
