huapohen/imagine/media/qa/03_keyboard_sidecar_09s.jpg

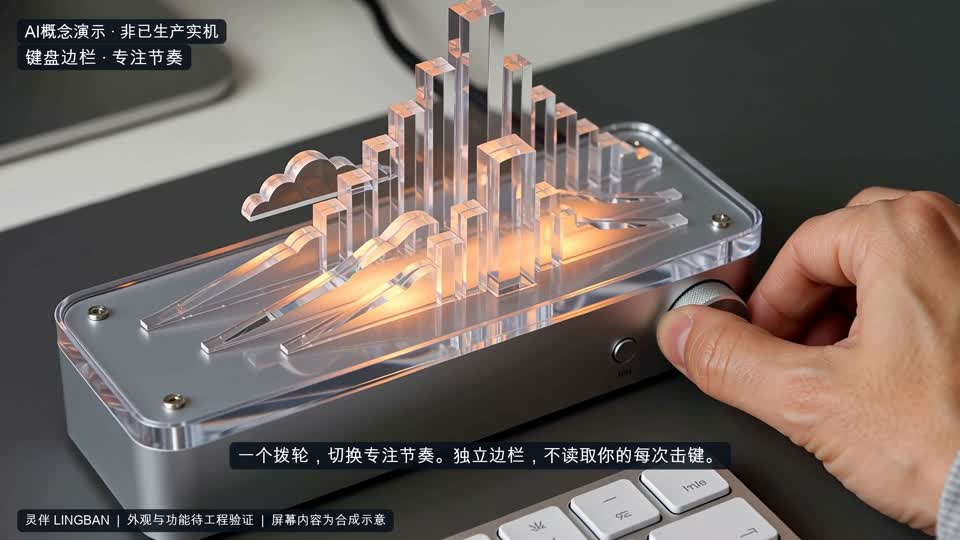
media/qa/03_keyboard_sidecar_09s.jpg
