huapohen/imagine/media/qa/03_keyboard_sidecar_13s.jpg

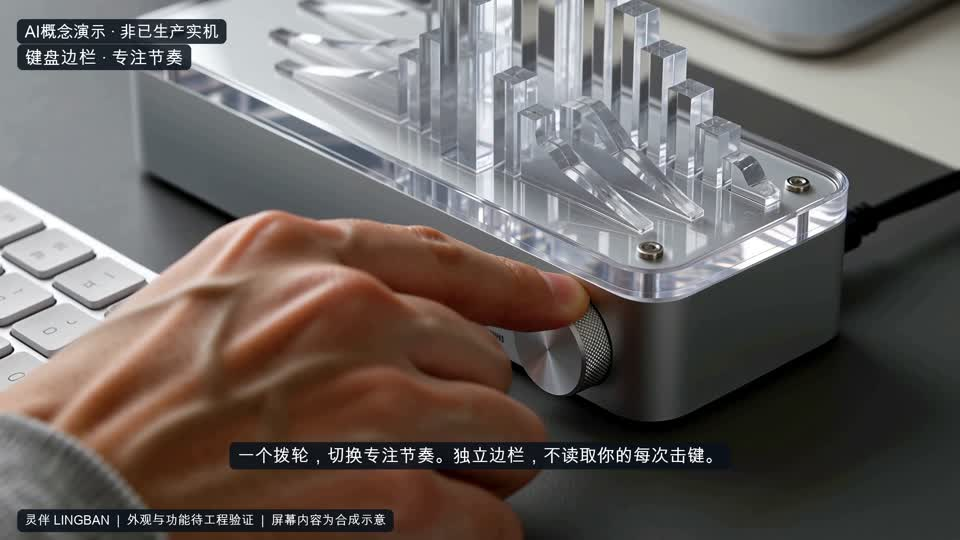
media/qa/03_keyboard_sidecar_13s.jpg
