huapohen/imagine/media/qa/03_keyboard_sidecar_contact.jpg

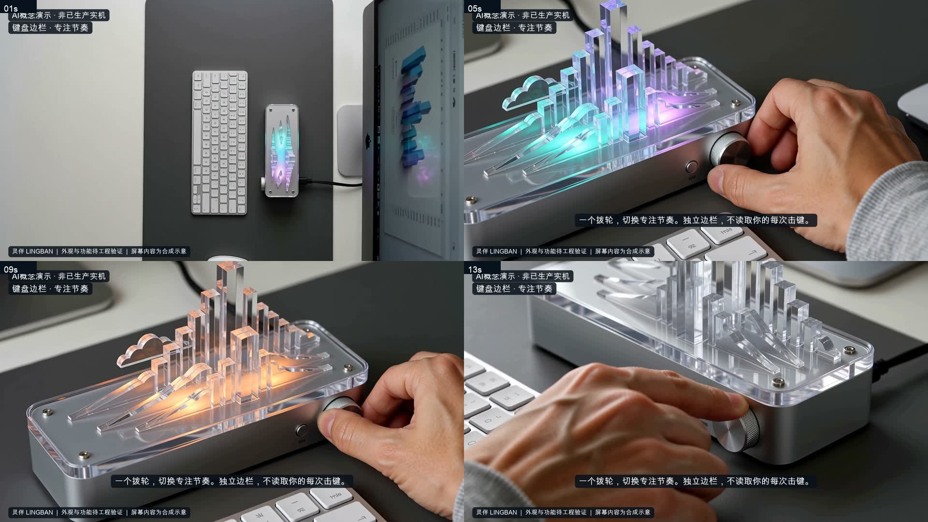
media/qa/03_keyboard_sidecar_contact.jpg
