huapohen/imagine/media/qa/04_desktop_orb_01s.jpg

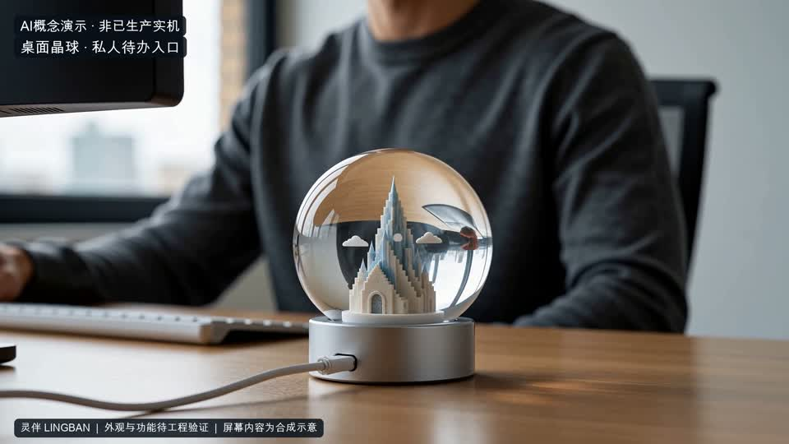
media/qa/04_desktop_orb_01s.jpg
