huapohen/imagine/media/qa/04_desktop_orb_09s.jpg

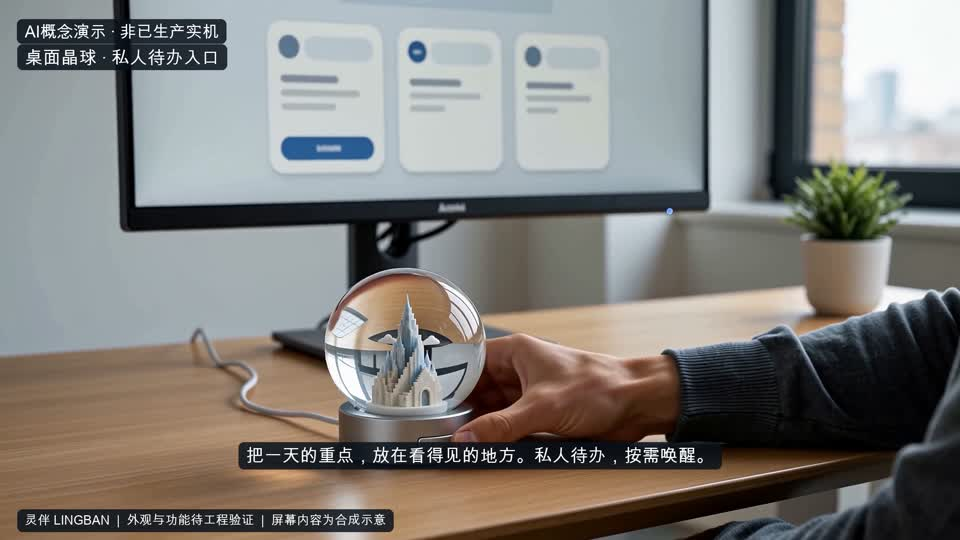
media/qa/04_desktop_orb_09s.jpg
