huapohen/imagine/media/qa/04_desktop_orb_13s.jpg

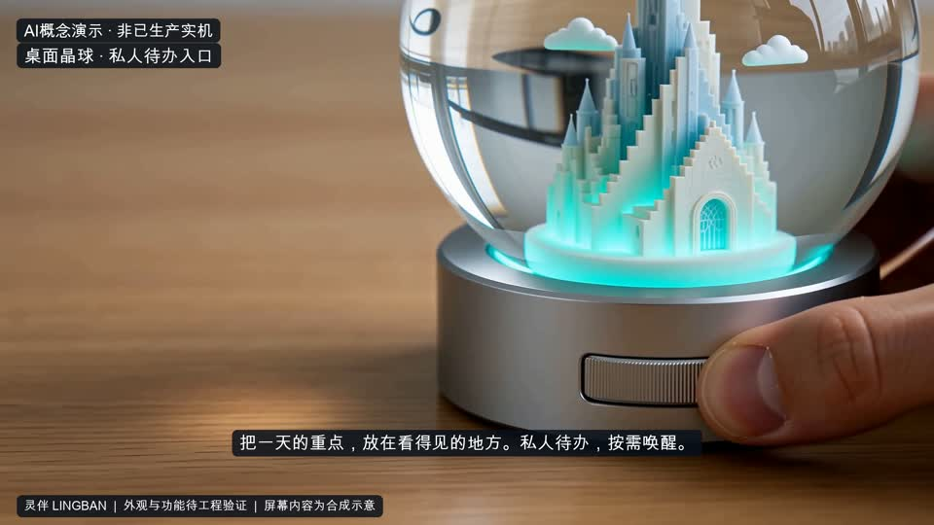
media/qa/04_desktop_orb_13s.jpg
