huapohen/imagine/media/qa/04_desktop_orb_contact.jpg

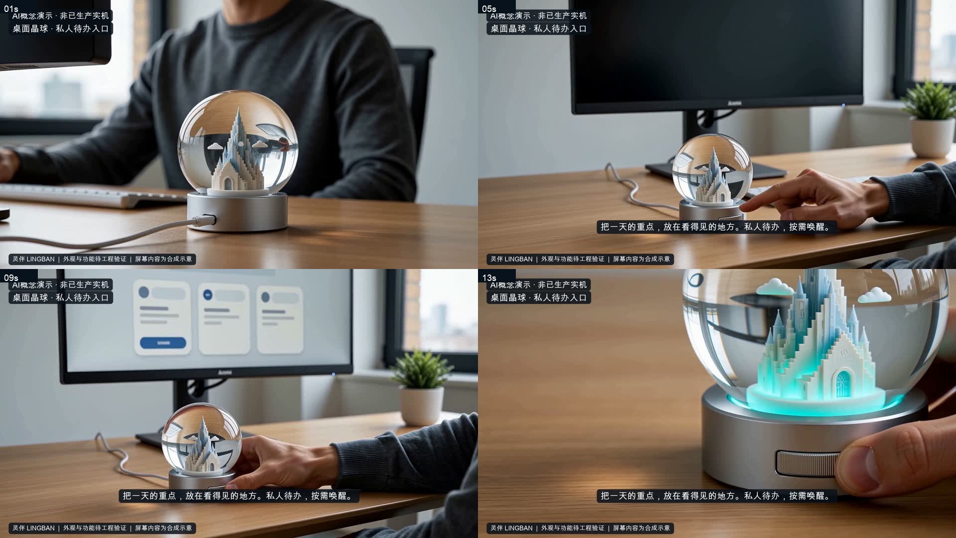
media/qa/04_desktop_orb_contact.jpg
