huapohen/imagine/media/qa/05_monitor_charm_01s.jpg

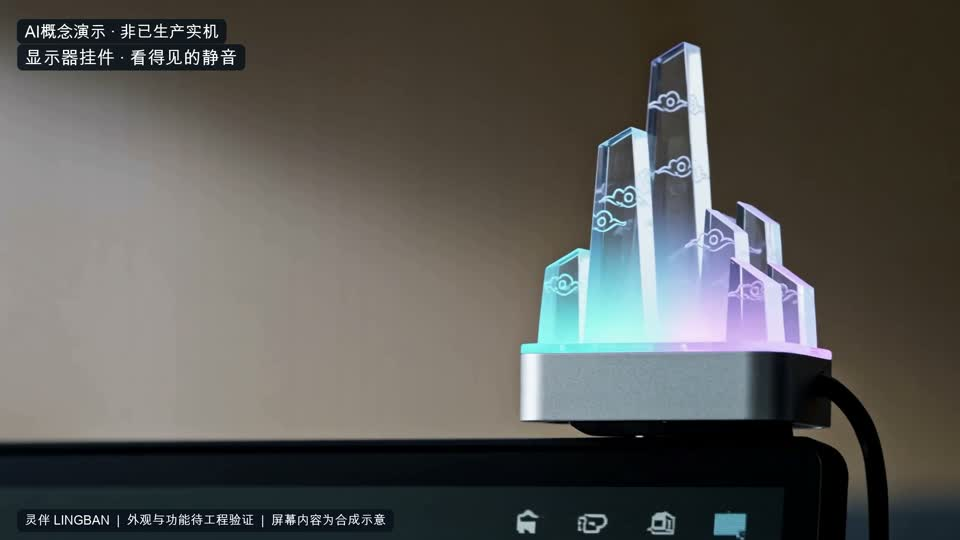
media/qa/05_monitor_charm_01s.jpg
