huapohen/imagine/media/qa/05_monitor_charm_09s.jpg

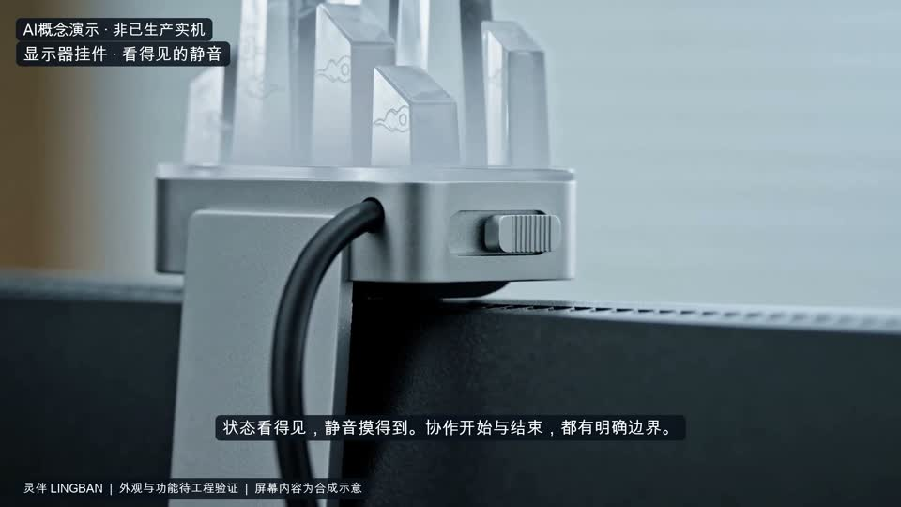
media/qa/05_monitor_charm_09s.jpg
