huapohen/imagine/media/qa/05_monitor_charm_13s.jpg

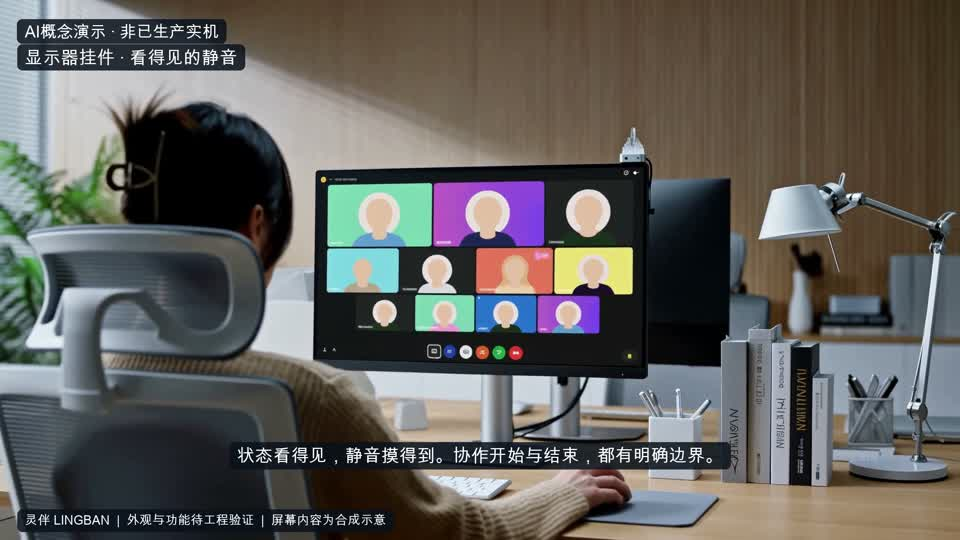
media/qa/05_monitor_charm_13s.jpg
