huapohen/imagine/media/qa/06_meeting_puck_01s.jpg

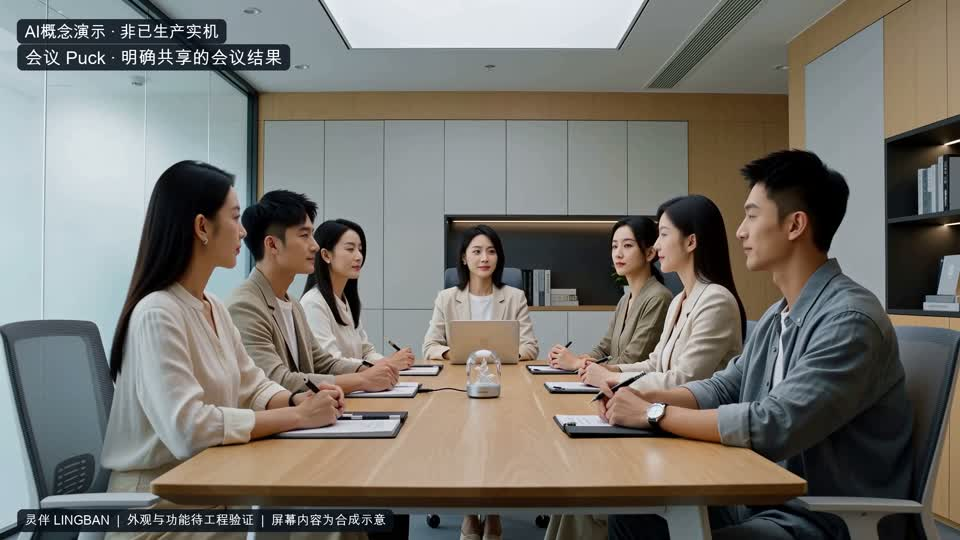
media/qa/06_meeting_puck_01s.jpg
