huapohen/imagine/media/qa/06_meeting_puck_05s.jpg

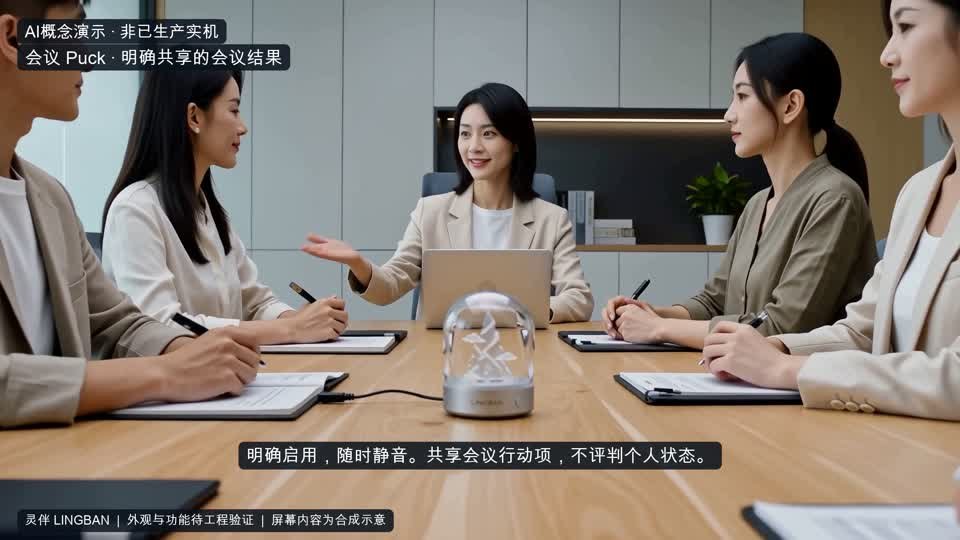
media/qa/06_meeting_puck_05s.jpg
