huapohen/imagine/media/qa/06_meeting_puck_09s.jpg

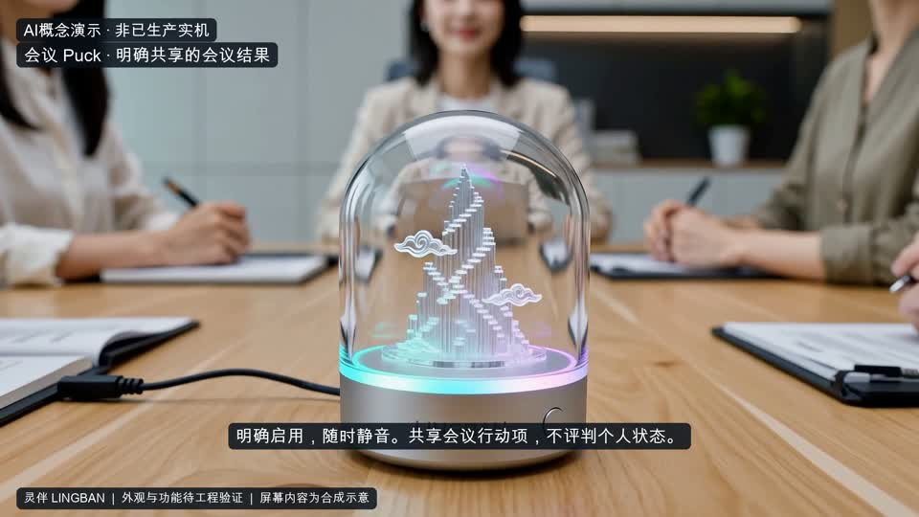
media/qa/06_meeting_puck_09s.jpg
