huapohen/imagine/media/qa/06_meeting_puck_13s.jpg

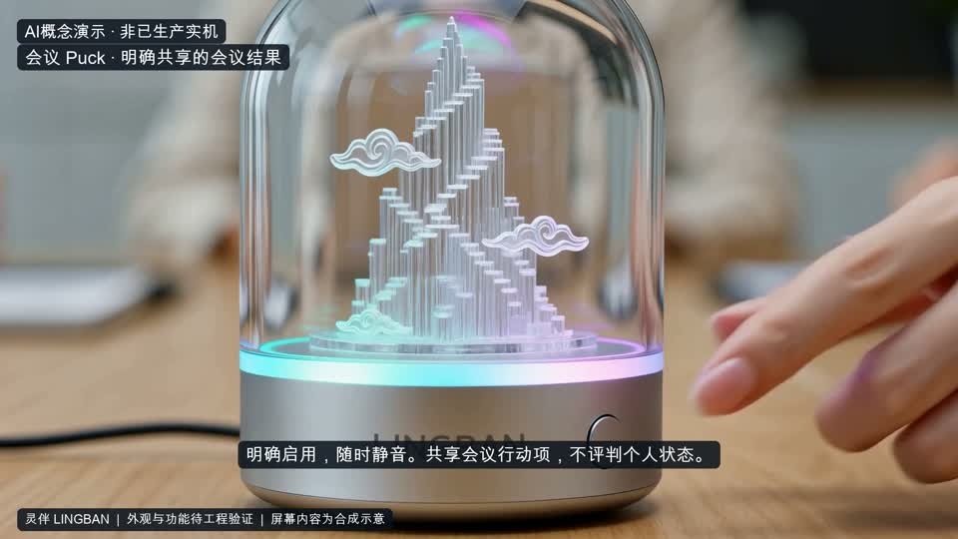
media/qa/06_meeting_puck_13s.jpg
