huapohen/imagine/media/qa/06_meeting_puck_contact.jpg

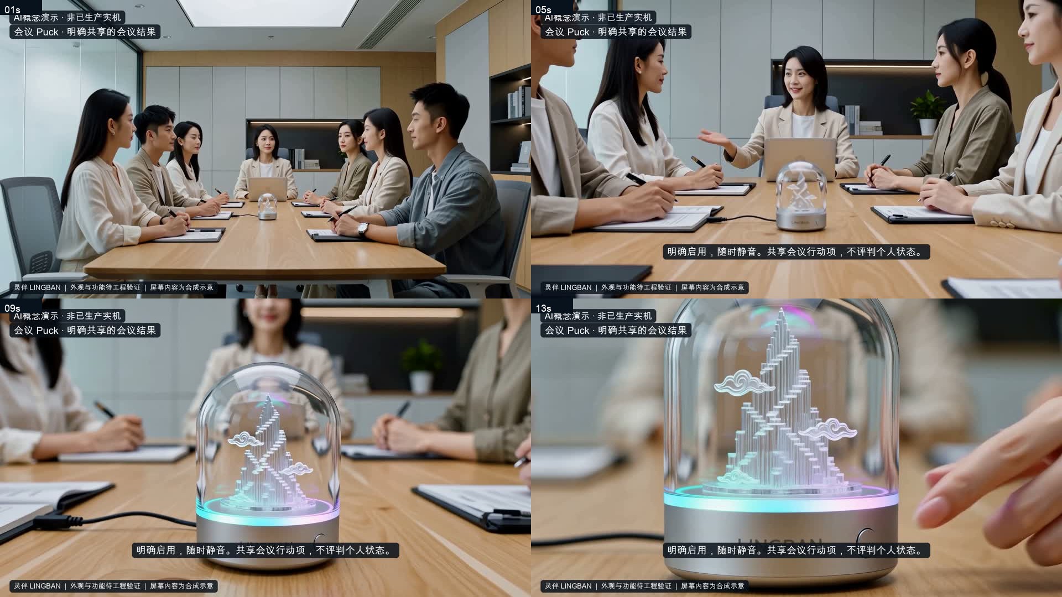
media/qa/06_meeting_puck_contact.jpg
