huapohen/imagine/media/qa/07_deskmat_module_01s.jpg

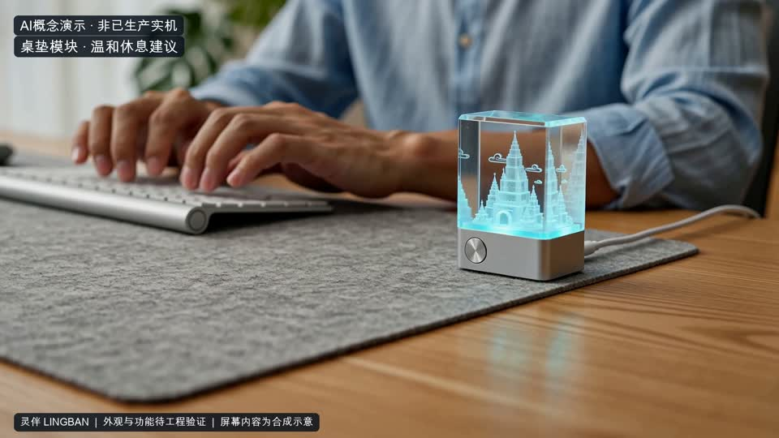
media/qa/07_deskmat_module_01s.jpg
