huapohen/imagine/media/qa/07_deskmat_module_05s.jpg

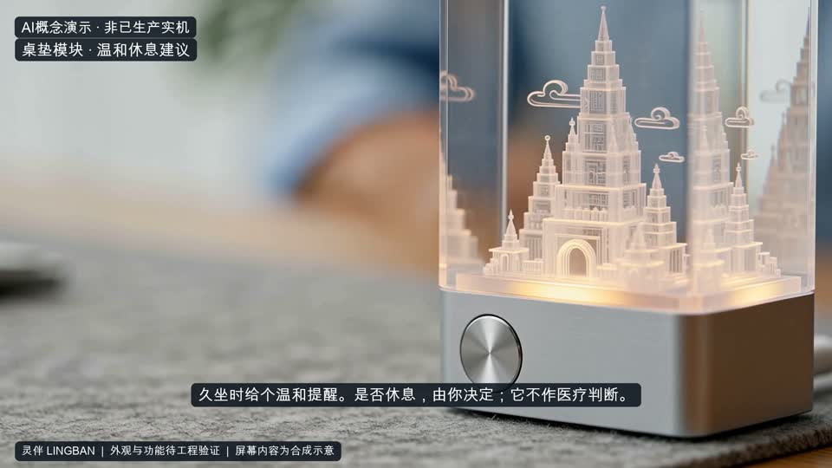
media/qa/07_deskmat_module_05s.jpg
