huapohen/imagine/media/qa/07_deskmat_module_09s.jpg

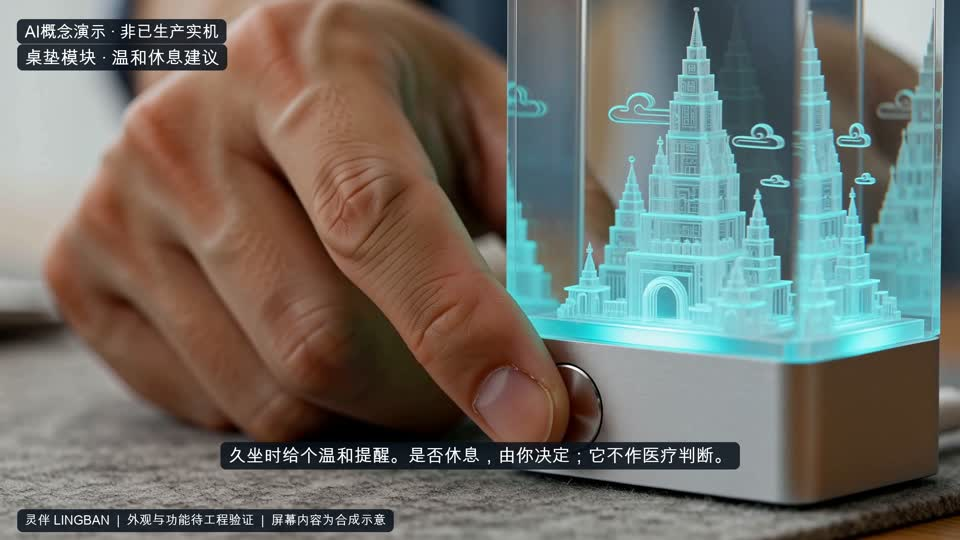
media/qa/07_deskmat_module_09s.jpg
