huapohen/imagine/media/qa/07_deskmat_module_13s.jpg

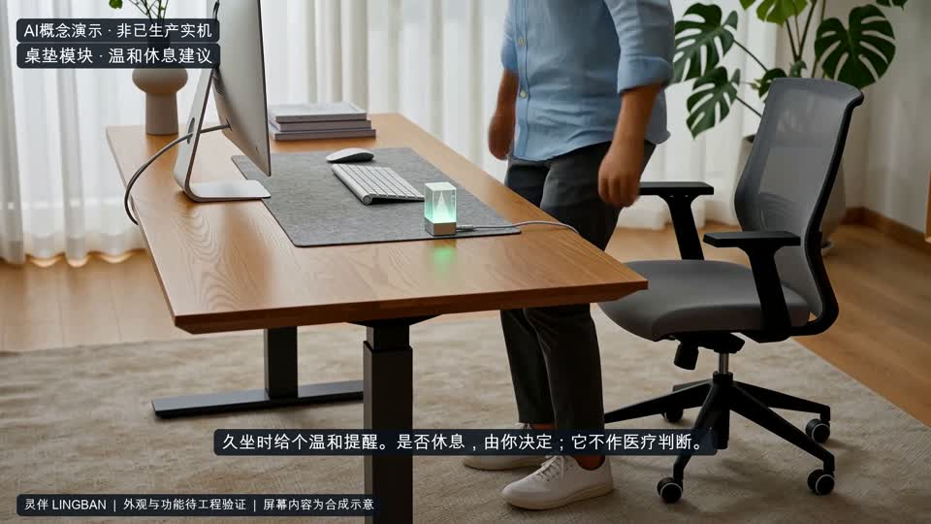
media/qa/07_deskmat_module_13s.jpg
