huapohen/imagine/media/qa/07_deskmat_module_contact.jpg

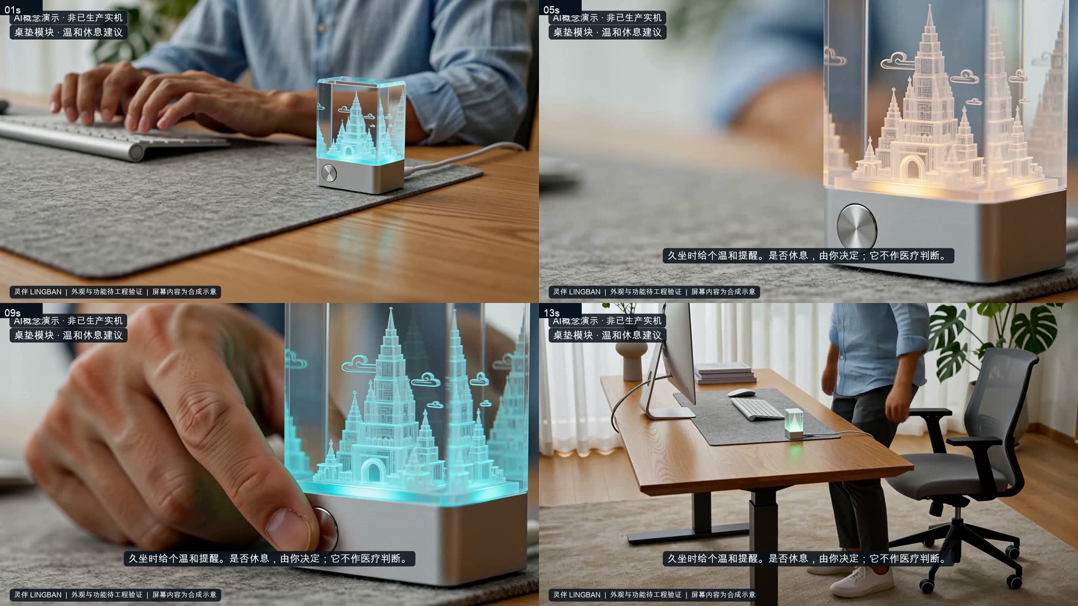
media/qa/07_deskmat_module_contact.jpg
