huapohen/imagine/media/qa/08_robot_extension_01s.jpg

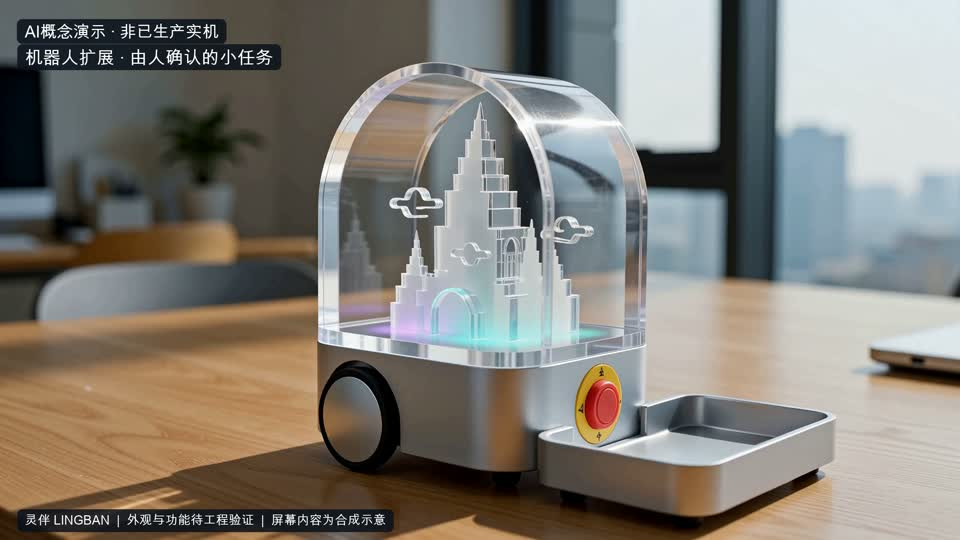
media/qa/08_robot_extension_01s.jpg
