huapohen/imagine/media/qa/08_robot_extension_05s.jpg

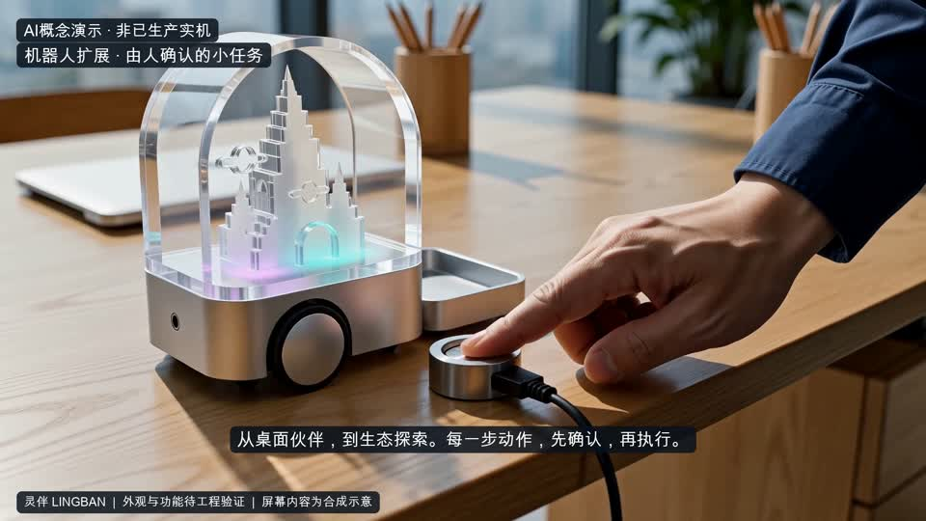
media/qa/08_robot_extension_05s.jpg
