huapohen/imagine/media/qa/08_robot_extension_09s.jpg

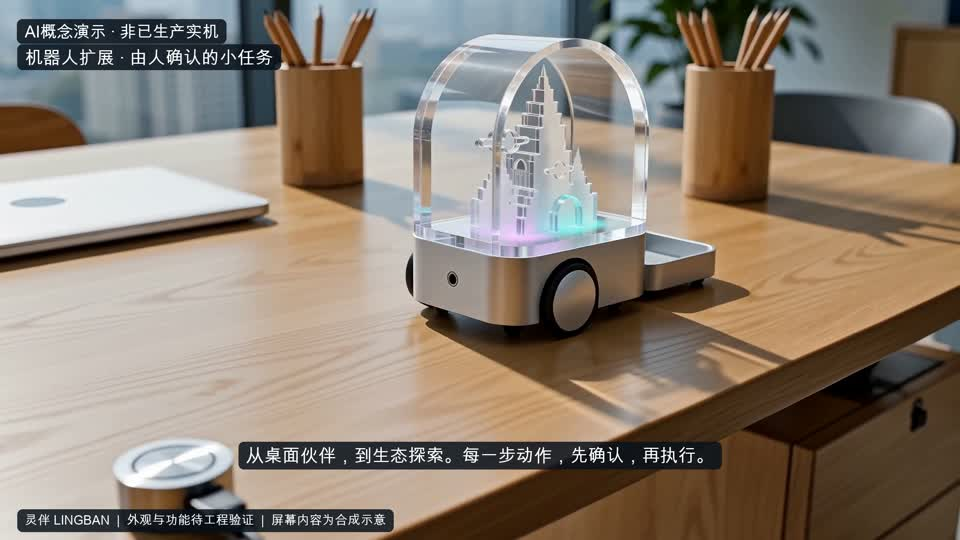
media/qa/08_robot_extension_09s.jpg
