huapohen/imagine/media/qa/08_robot_extension_13s.jpg

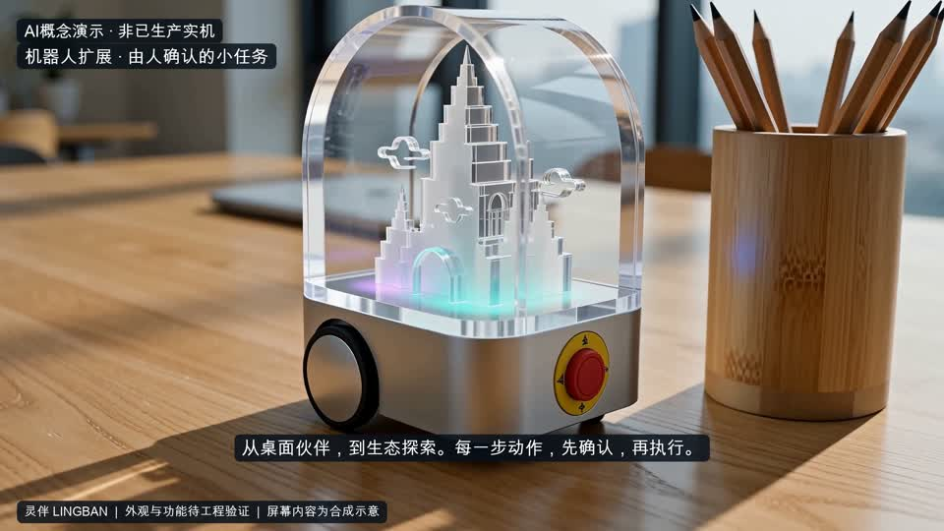
media/qa/08_robot_extension_13s.jpg
