huapohen/imagine/media/qa/08_robot_extension_contact.jpg

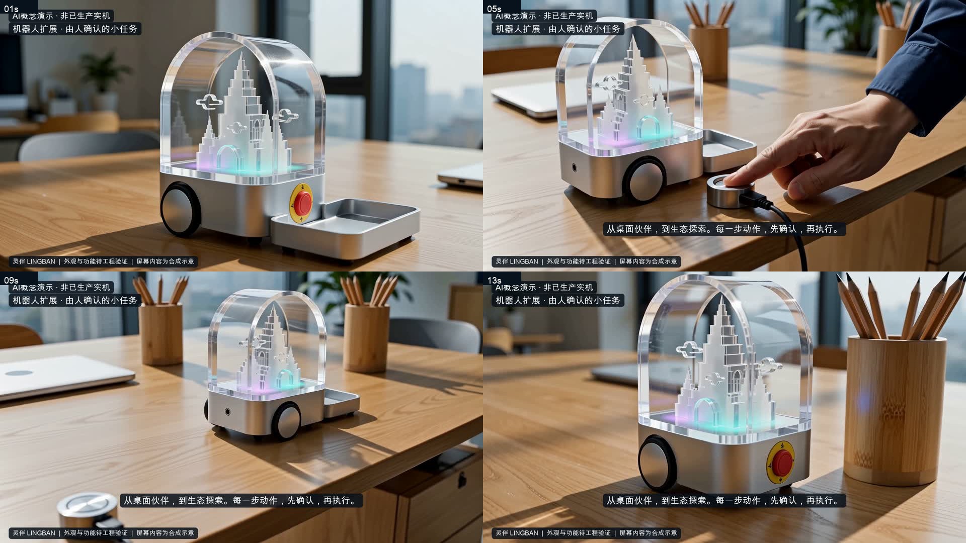
media/qa/08_robot_extension_contact.jpg
