huapohen/imagine/pitch/business-plan/qa/contact-sheet.jpg

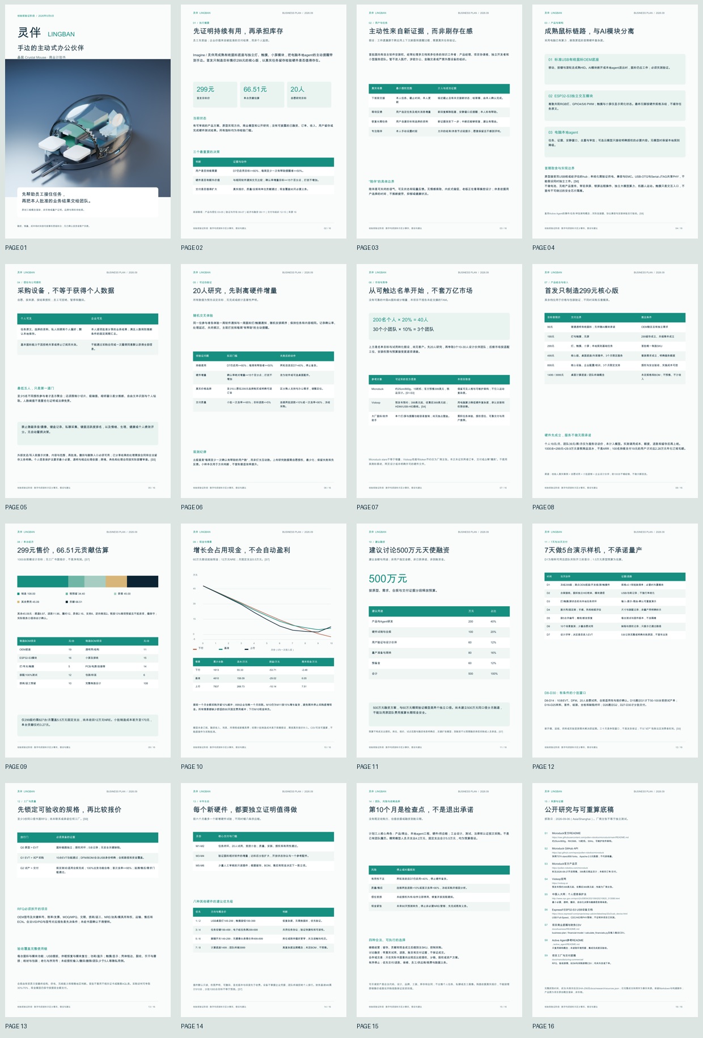
pitch/business-plan/qa/contact-sheet.jpg
