huapohen/imagine/pitch/business-plan/qa/page-02.png

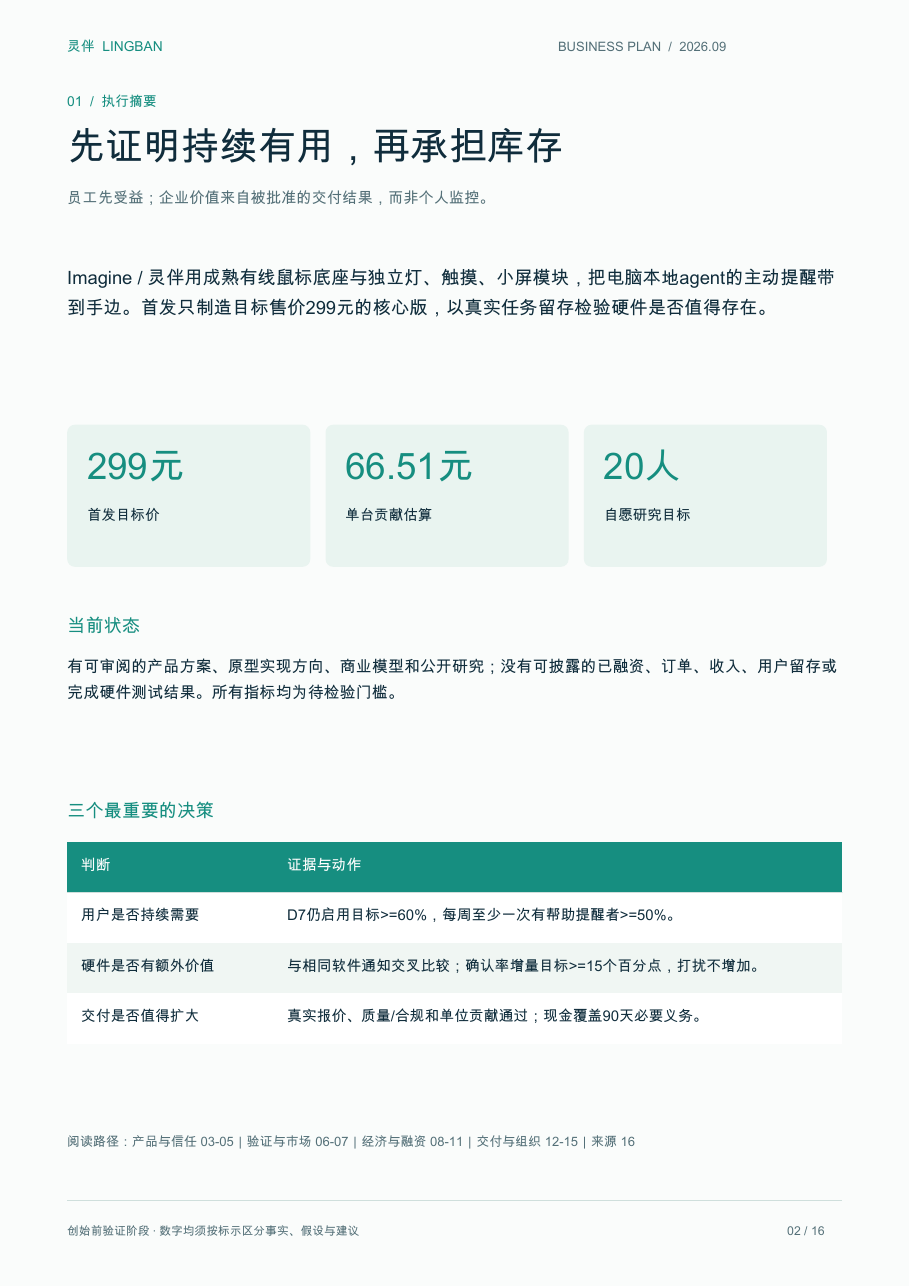
pitch/business-plan/qa/page-02.png
