huapohen/imagine/pitch/business-plan/qa/page-03.png

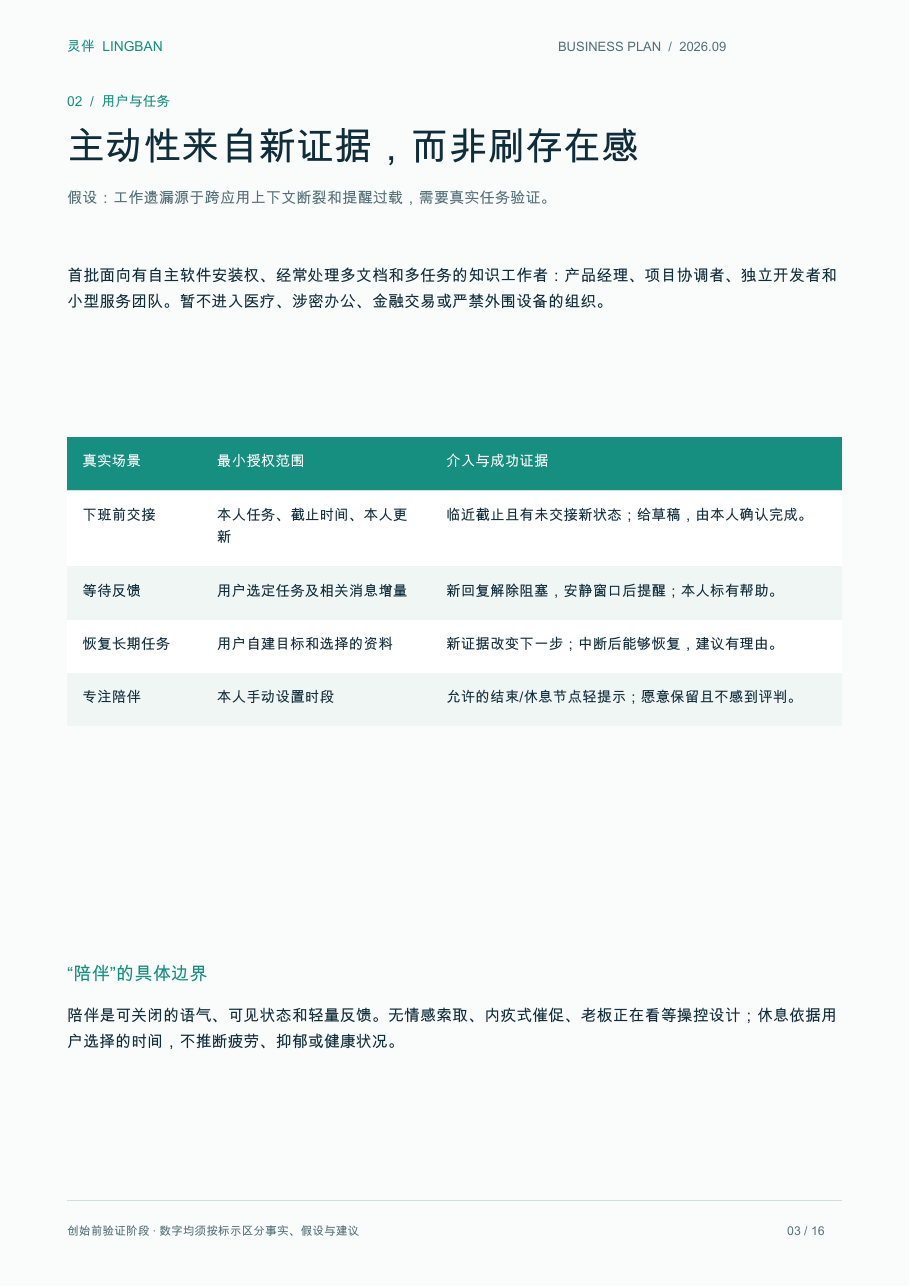
pitch/business-plan/qa/page-03.png
