huapohen/imagine/pitch/business-plan/qa/page-04.png

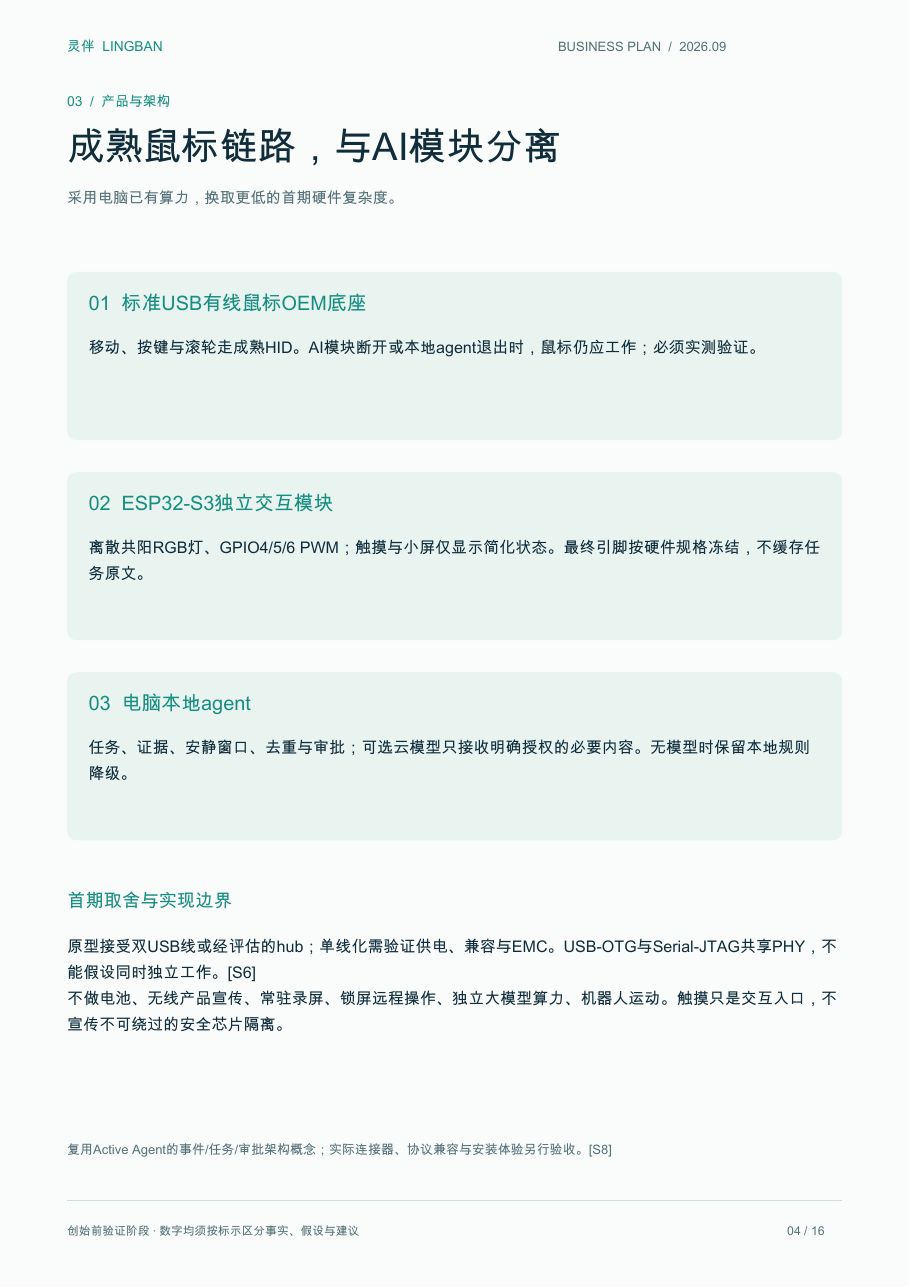
pitch/business-plan/qa/page-04.png
