huapohen/imagine/pitch/business-plan/qa/page-05.png

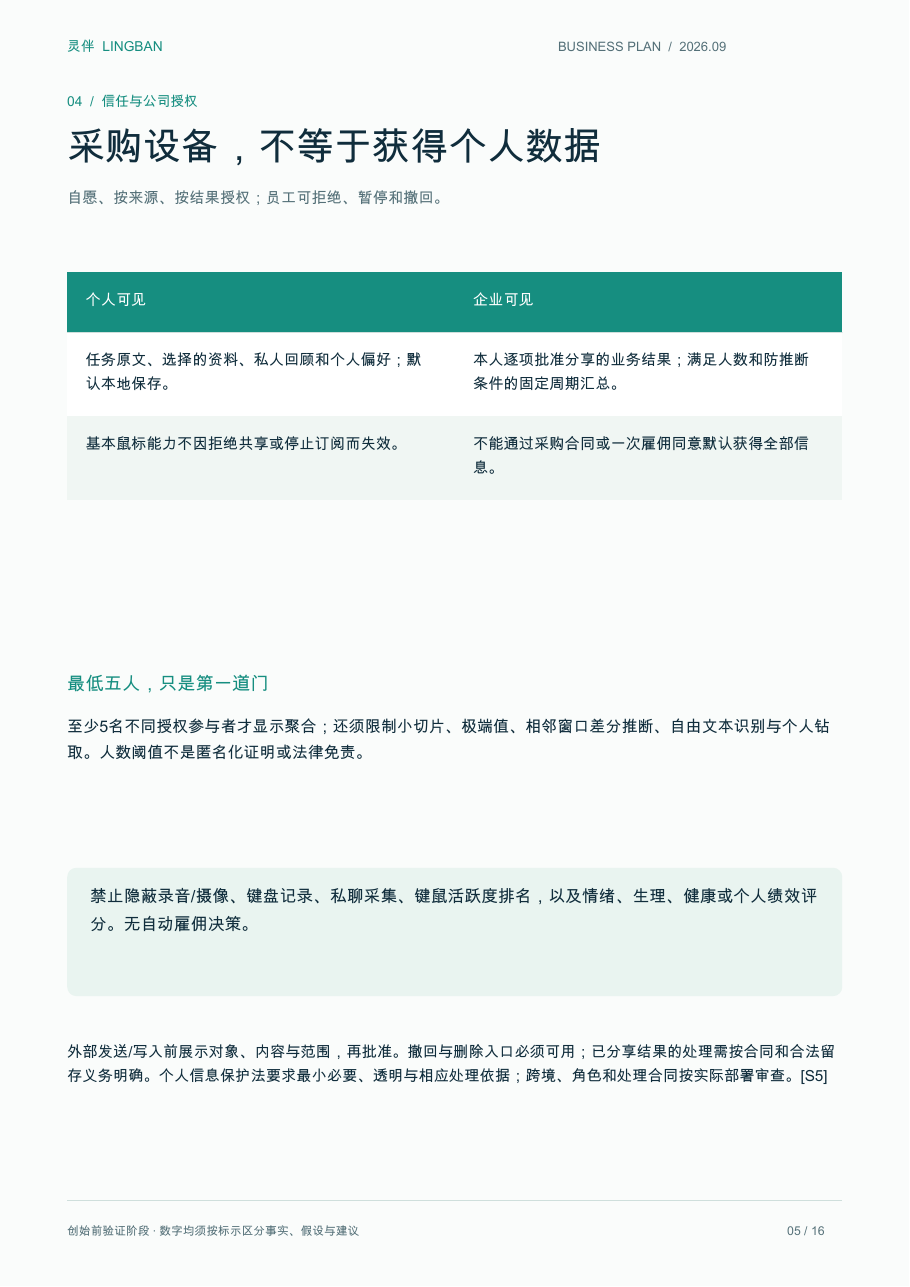
pitch/business-plan/qa/page-05.png
