huapohen/imagine/pitch/business-plan/qa/page-06.png

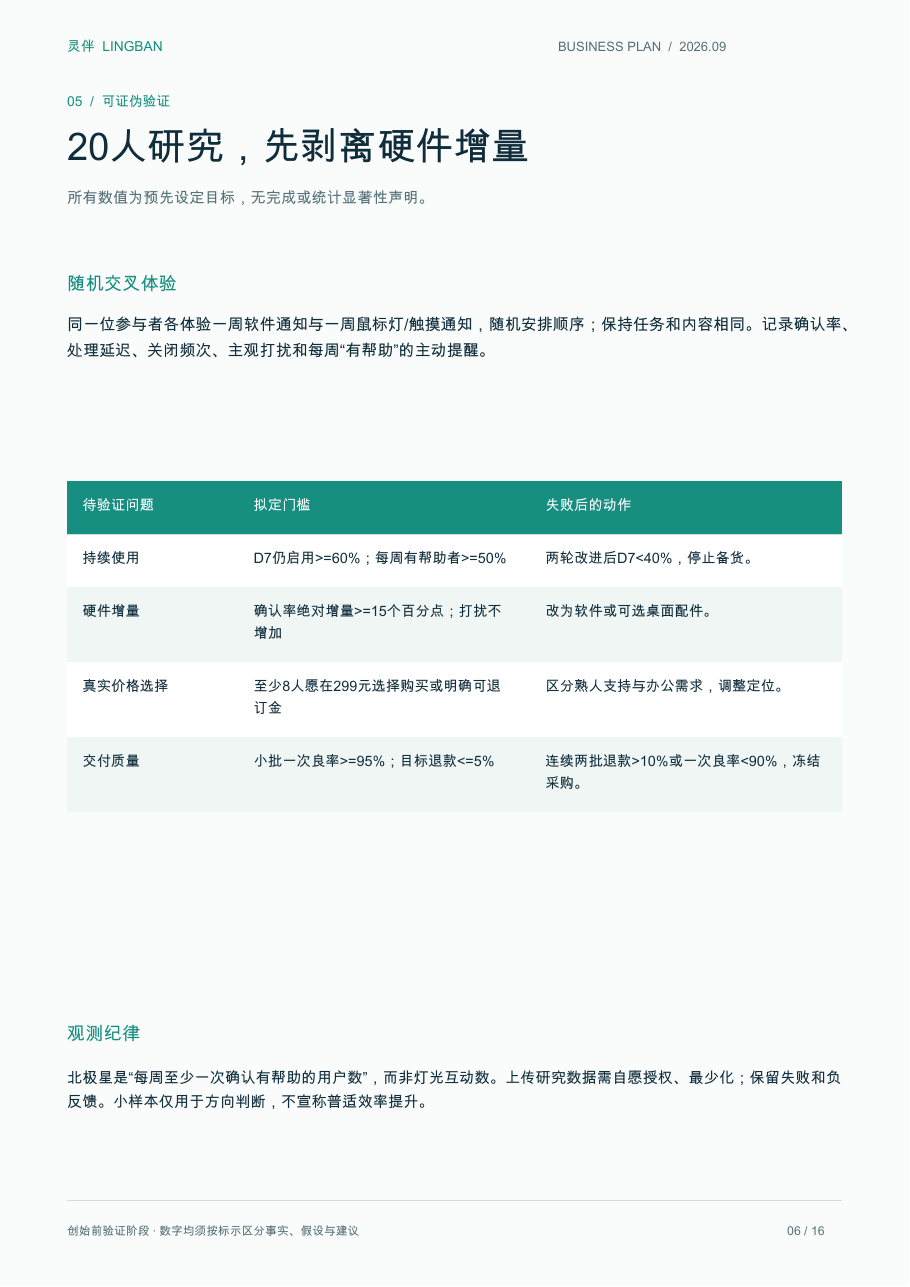
pitch/business-plan/qa/page-06.png
