huapohen/imagine/pitch/business-plan/qa/page-07.png

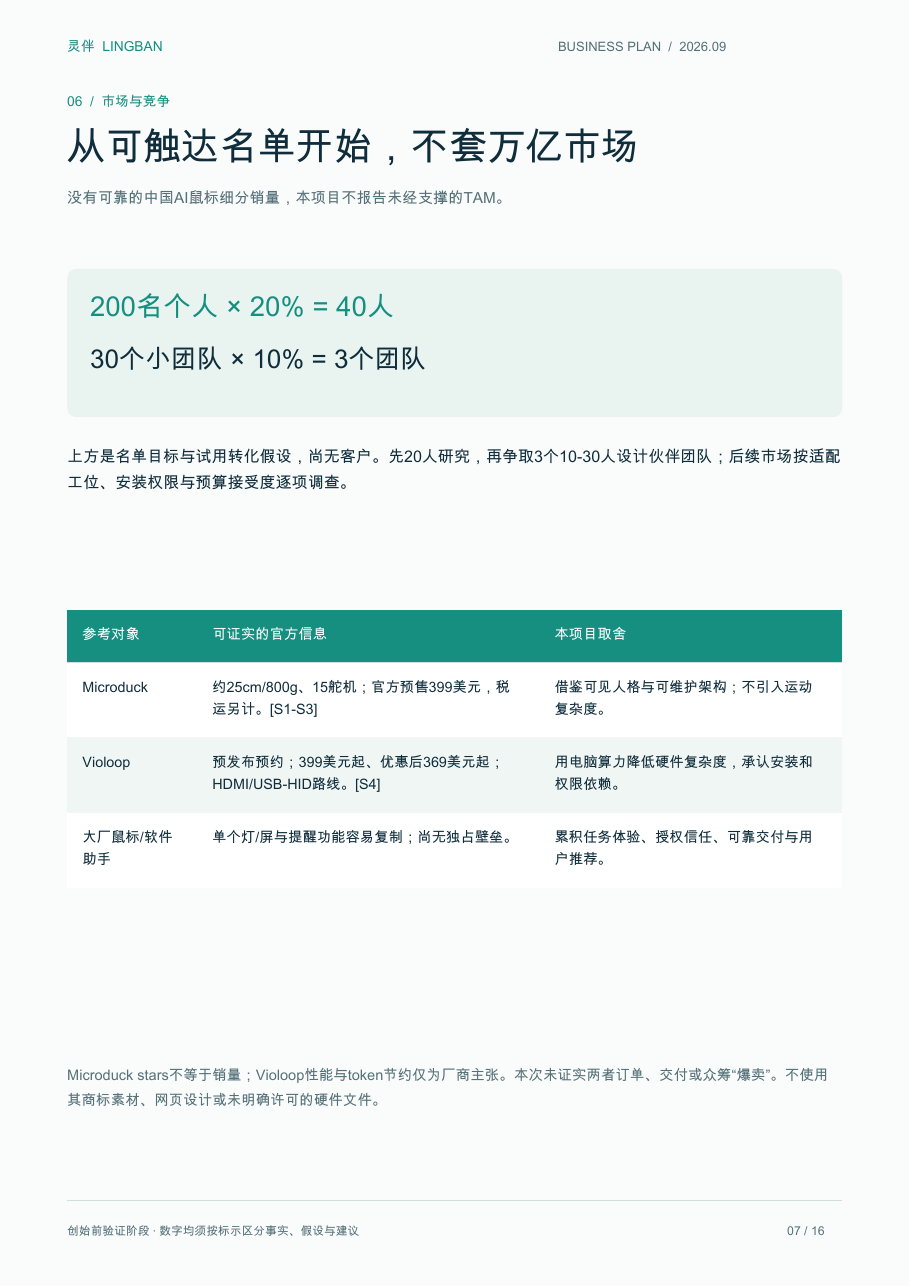
pitch/business-plan/qa/page-07.png
