huapohen/imagine/pitch/business-plan/qa/page-08.png

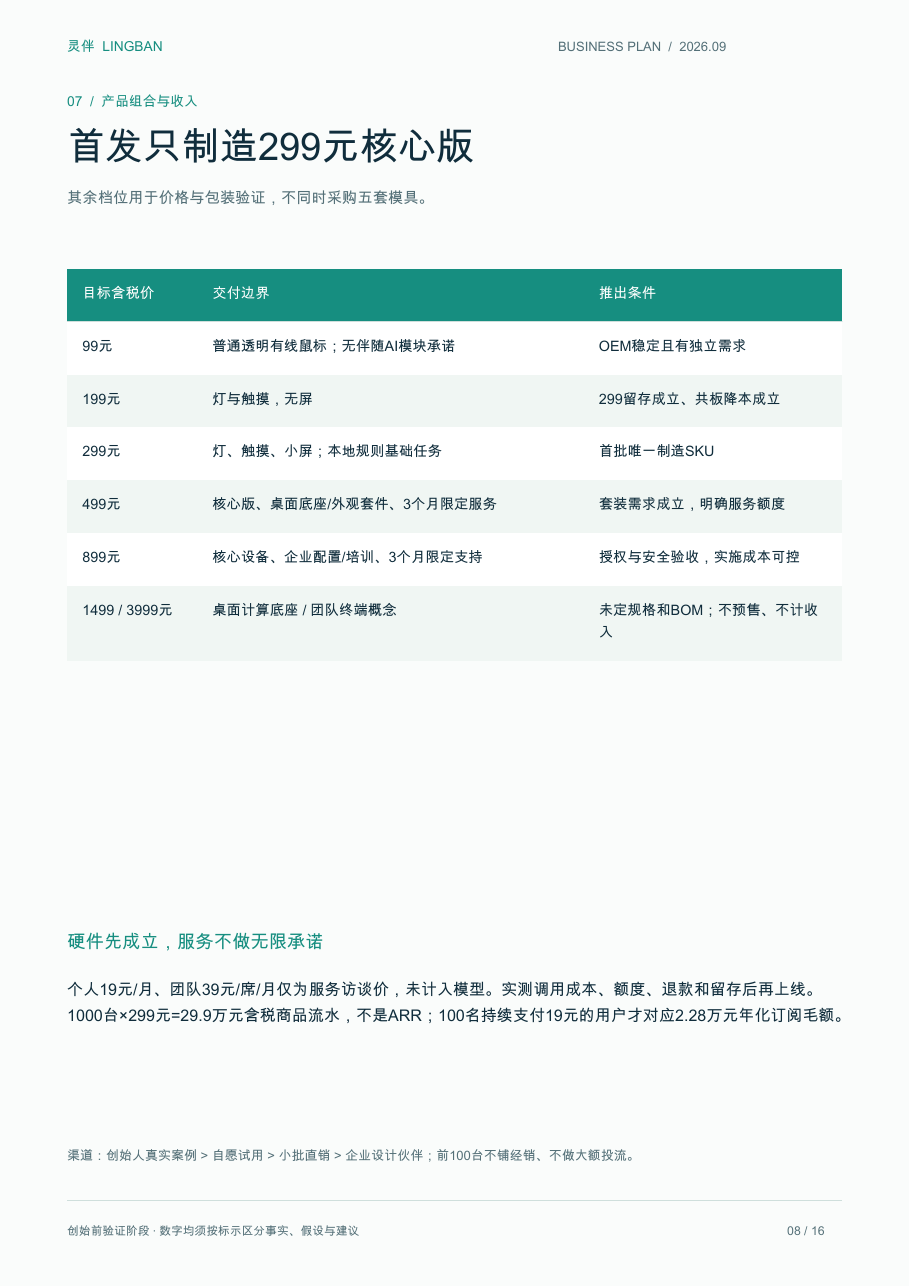
pitch/business-plan/qa/page-08.png
