huapohen/imagine/pitch/business-plan/qa/page-09.png

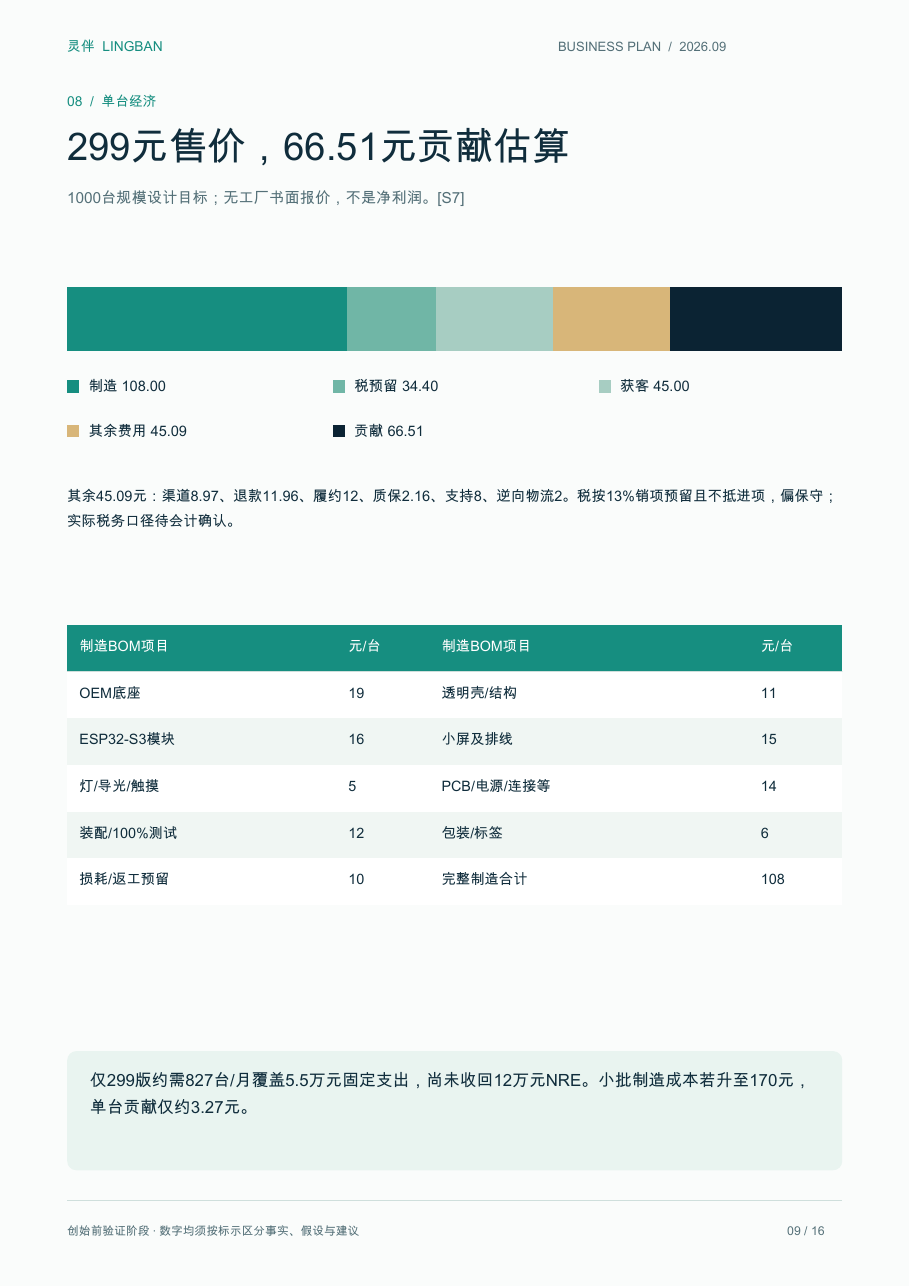
pitch/business-plan/qa/page-09.png
