huapohen/imagine/pitch/business-plan/qa/page-10.png

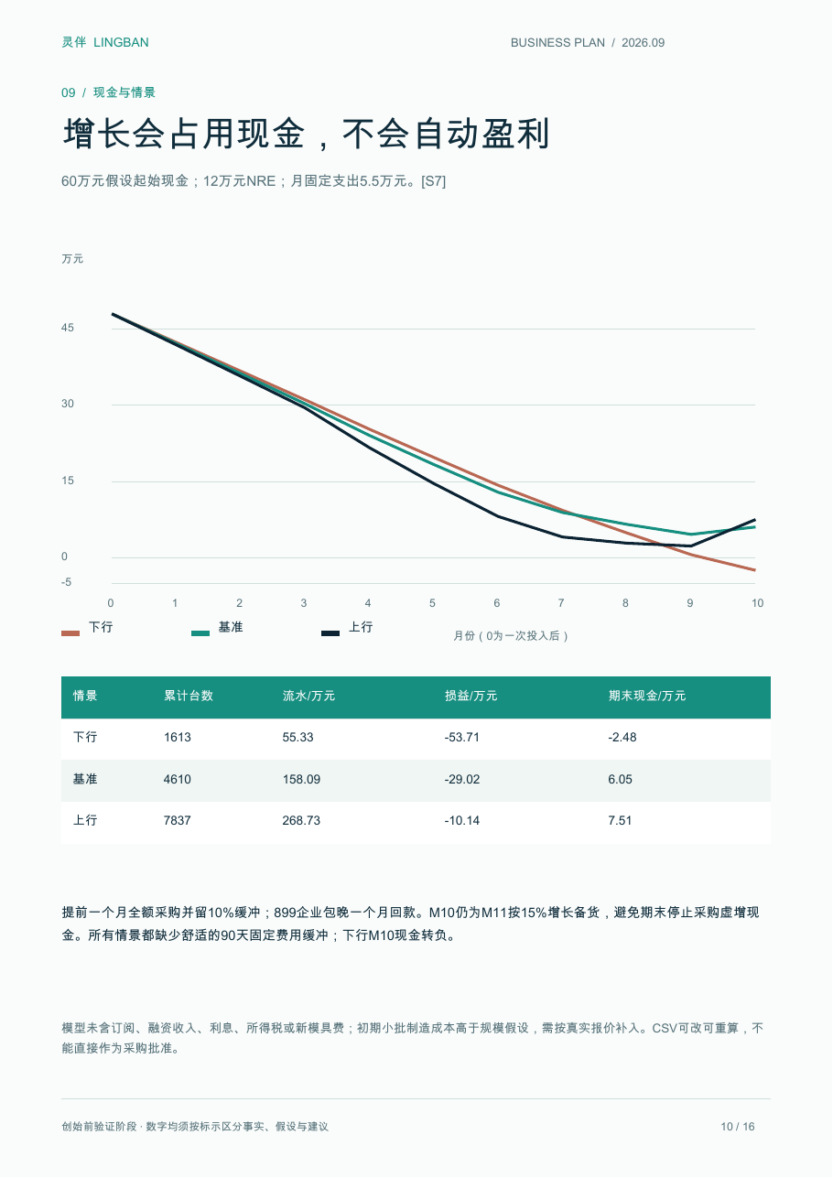
pitch/business-plan/qa/page-10.png
