huapohen/imagine/pitch/business-plan/qa/page-11.png

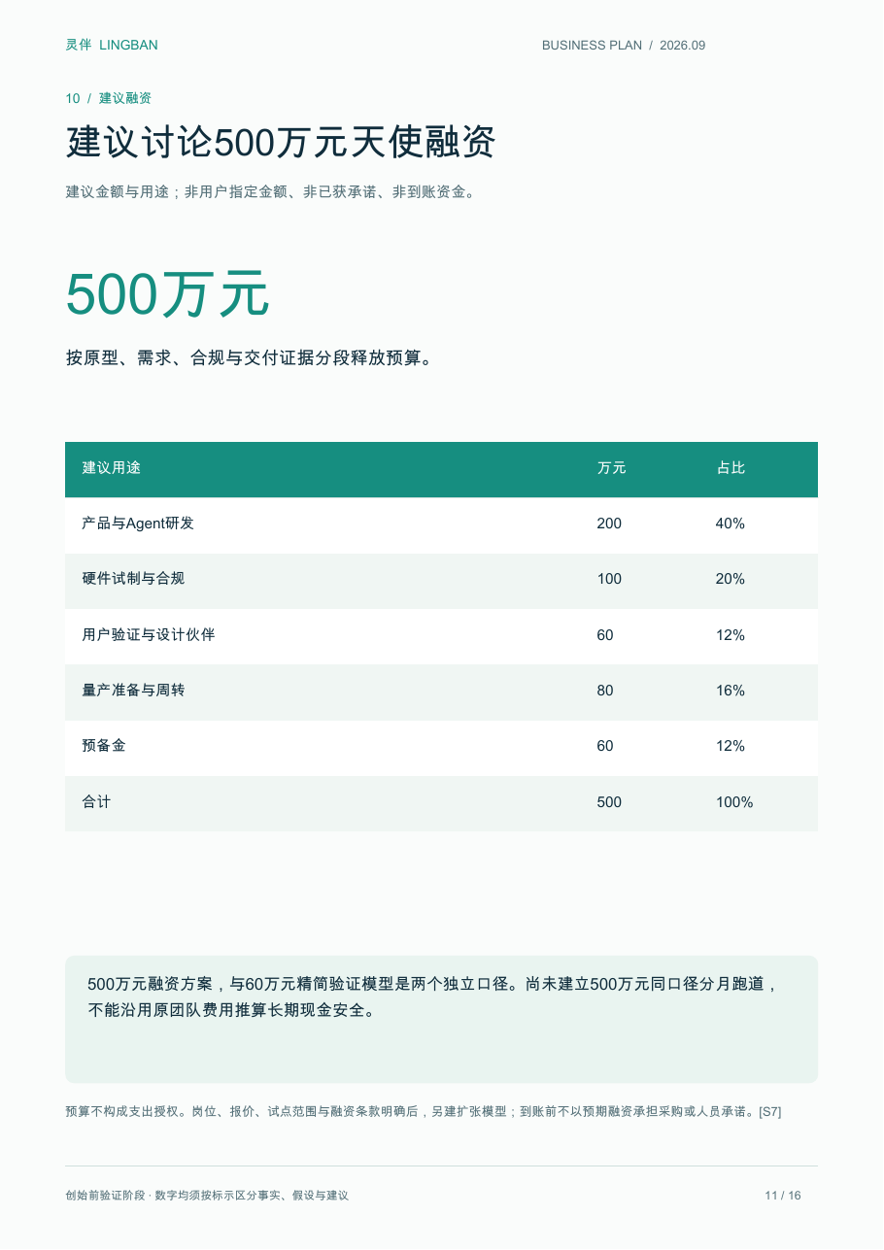
pitch/business-plan/qa/page-11.png
