huapohen/imagine/pitch/business-plan/qa/page-12.png

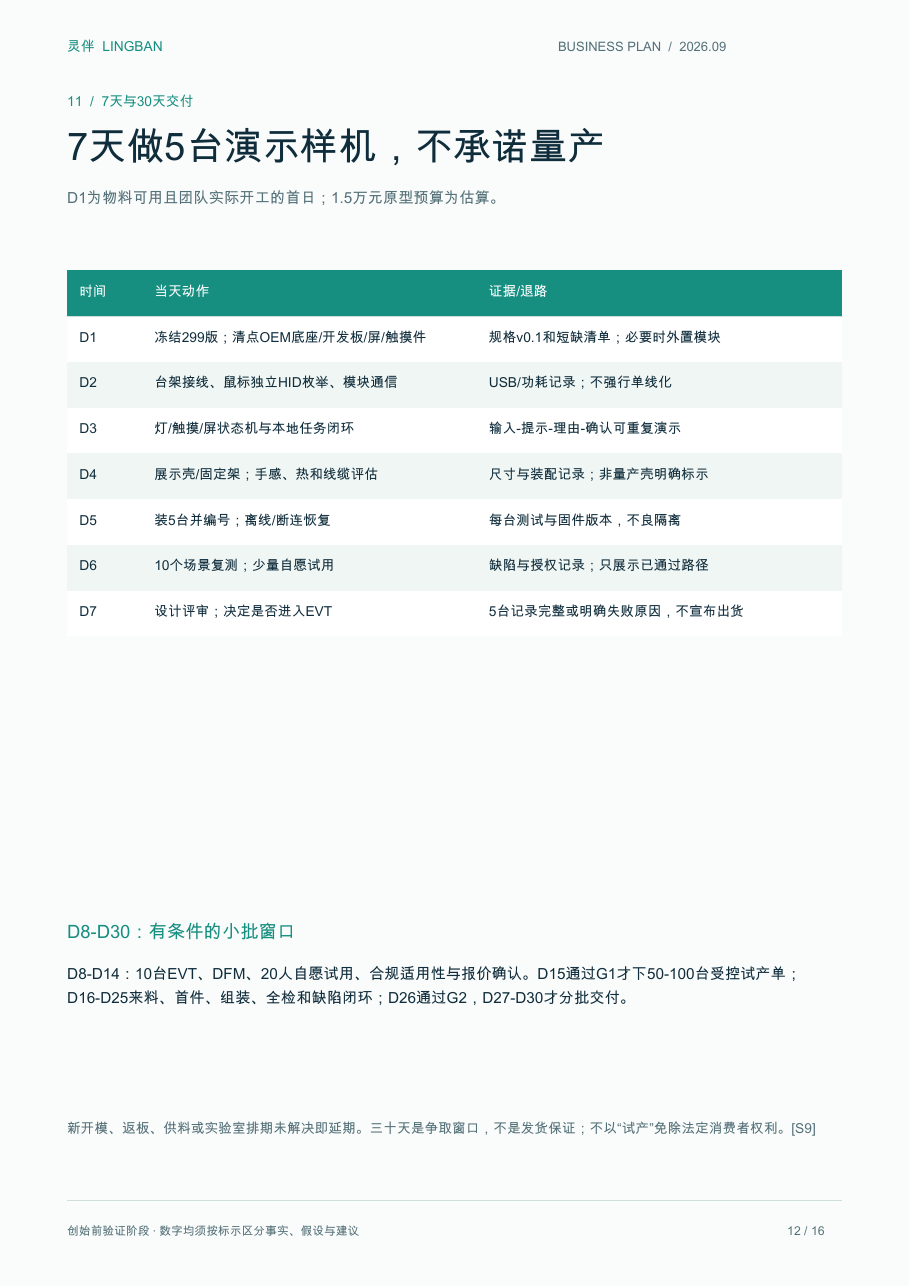
pitch/business-plan/qa/page-12.png
