huapohen/imagine/pitch/business-plan/qa/page-13.png

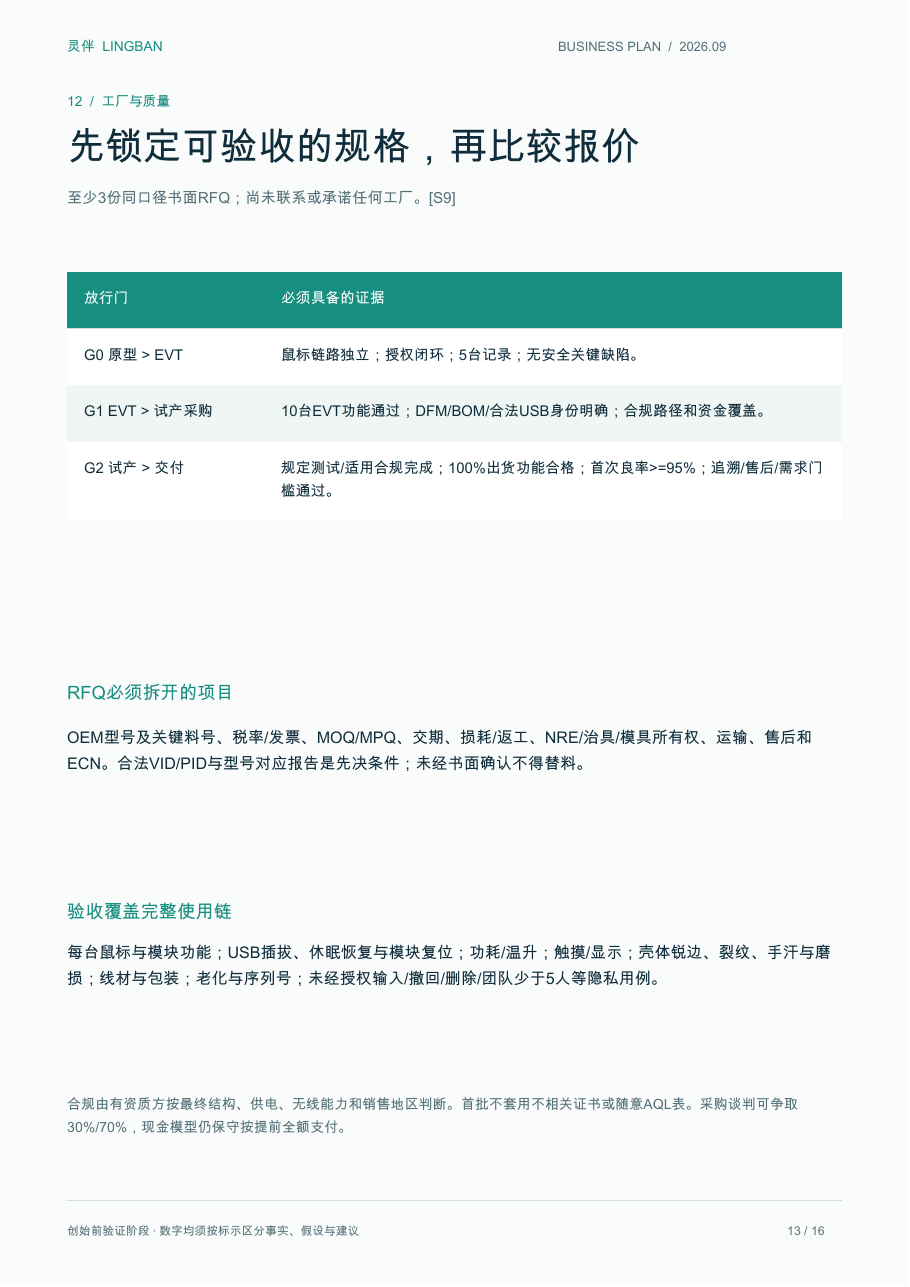
pitch/business-plan/qa/page-13.png
