huapohen/imagine/pitch/business-plan/qa/page-14.png

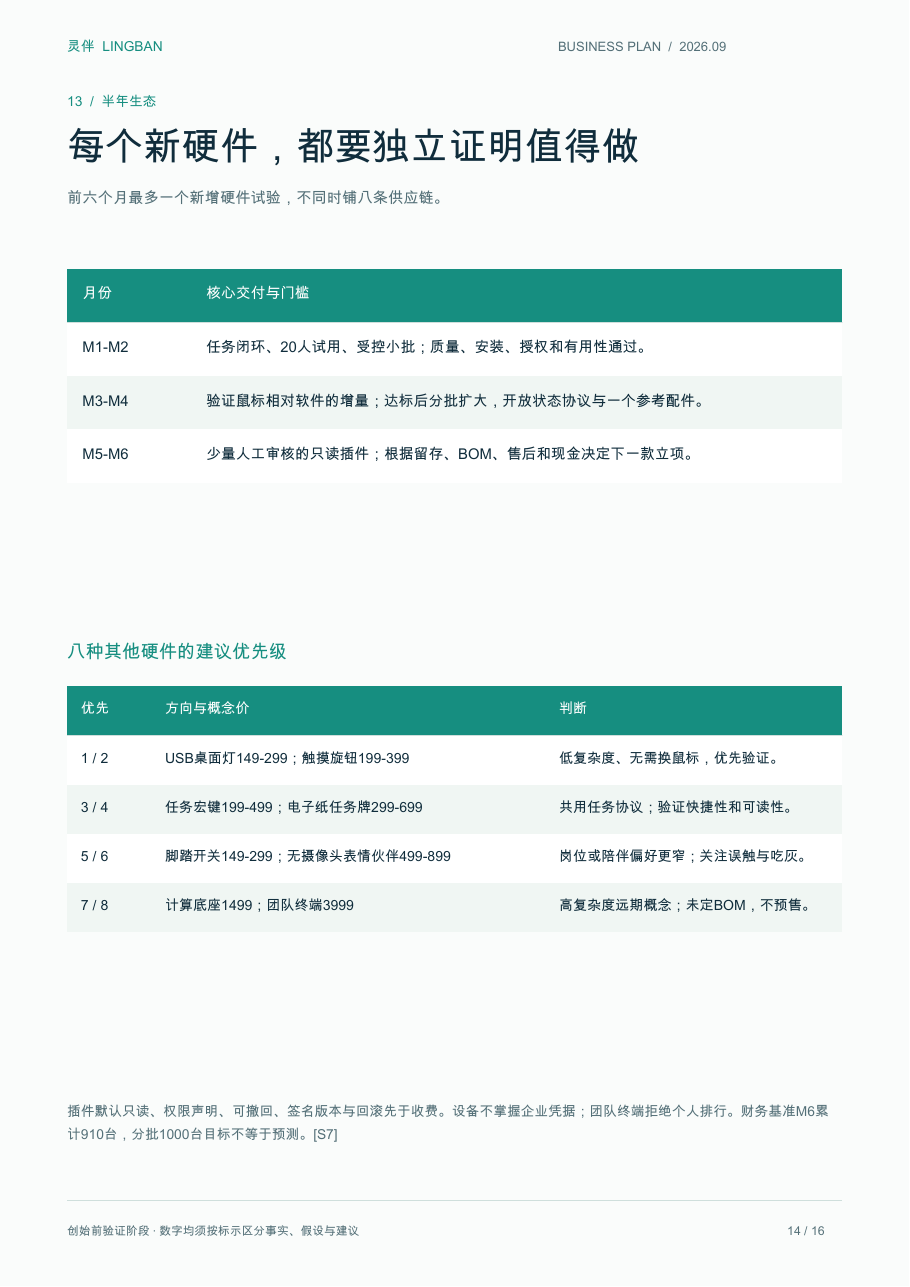
pitch/business-plan/qa/page-14.png
