huapohen/imagine/pitch/business-plan/qa/page-15.png

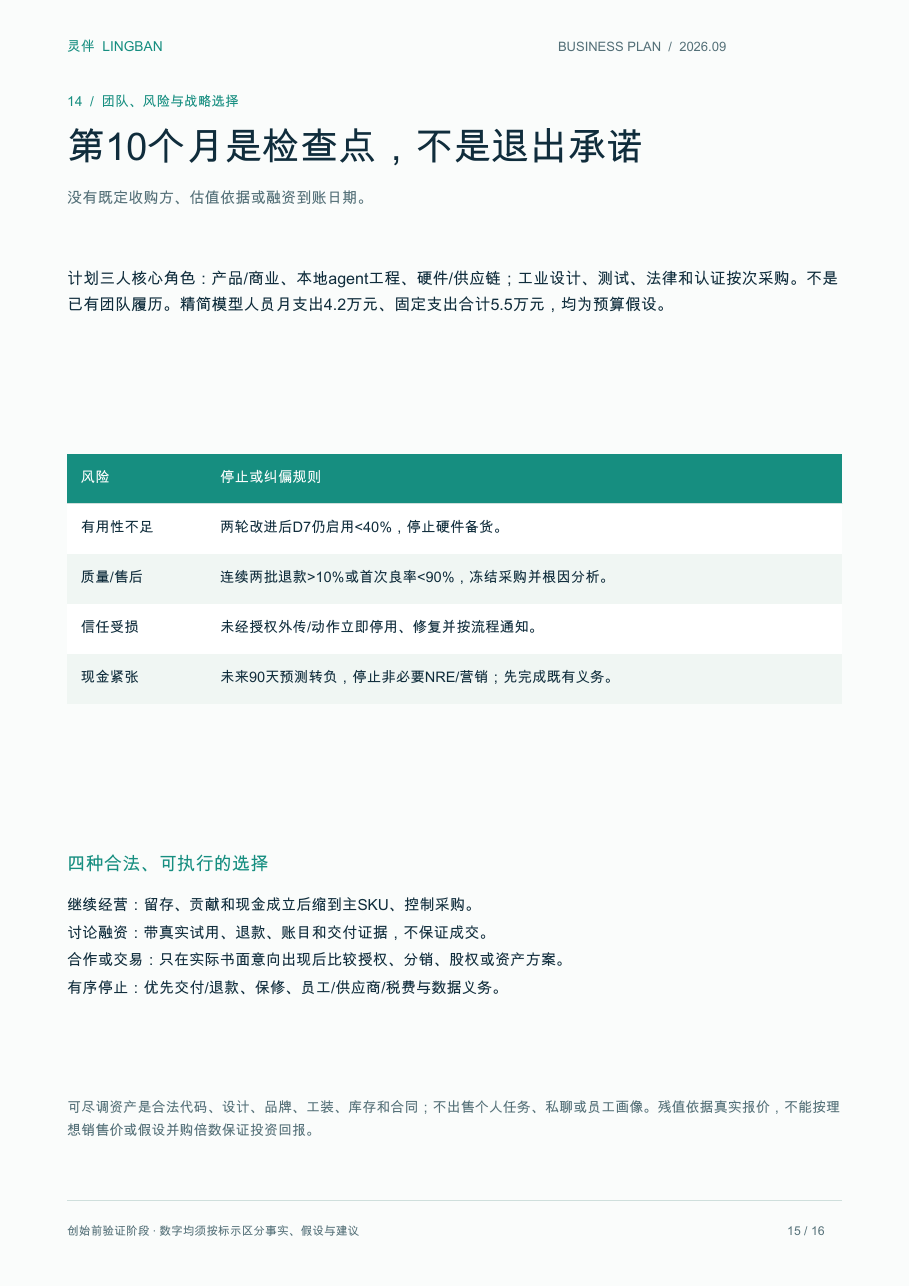
pitch/business-plan/qa/page-15.png
