huapohen/imagine/pitch/business-plan/qa/page-16.png

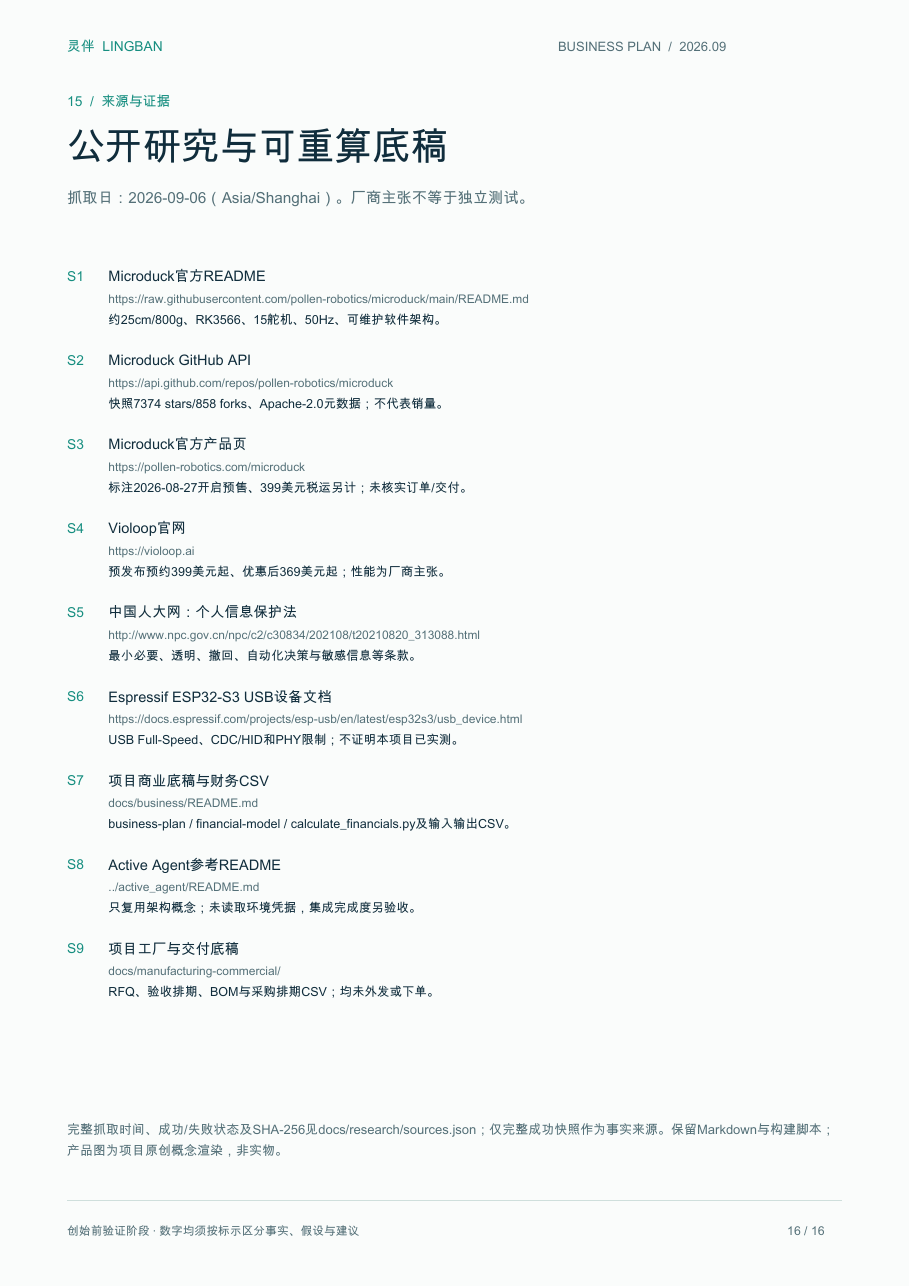
pitch/business-plan/qa/page-16.png
