huapohen/imagine/pitch/qa/contact-sheet.jpg

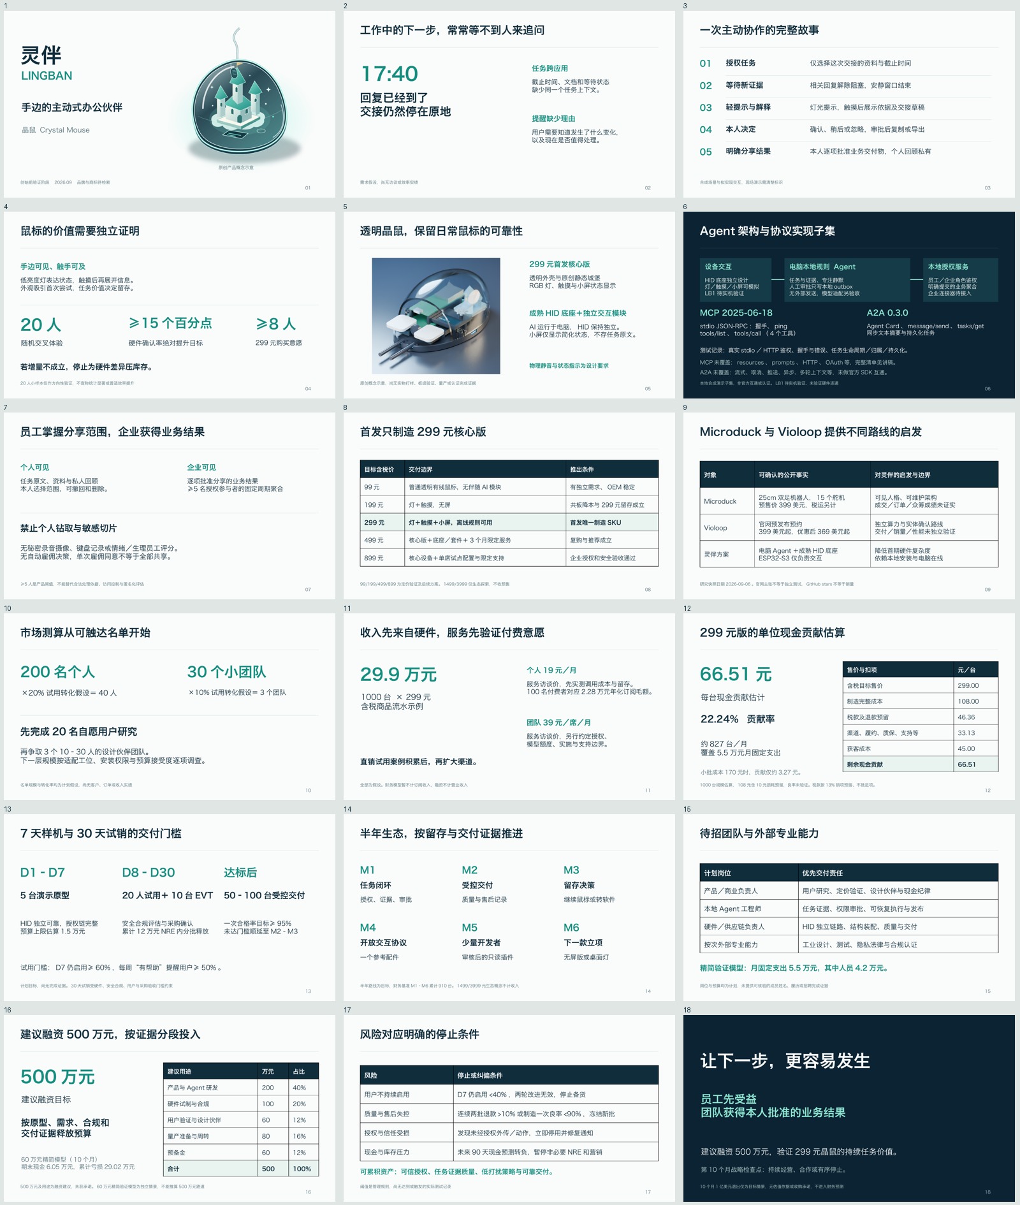
pitch/qa/contact-sheet.jpg
